tebl/RC6502-Apple-1-Replica/Abandoned/RC6502 Video Adapter/export/pcb.png

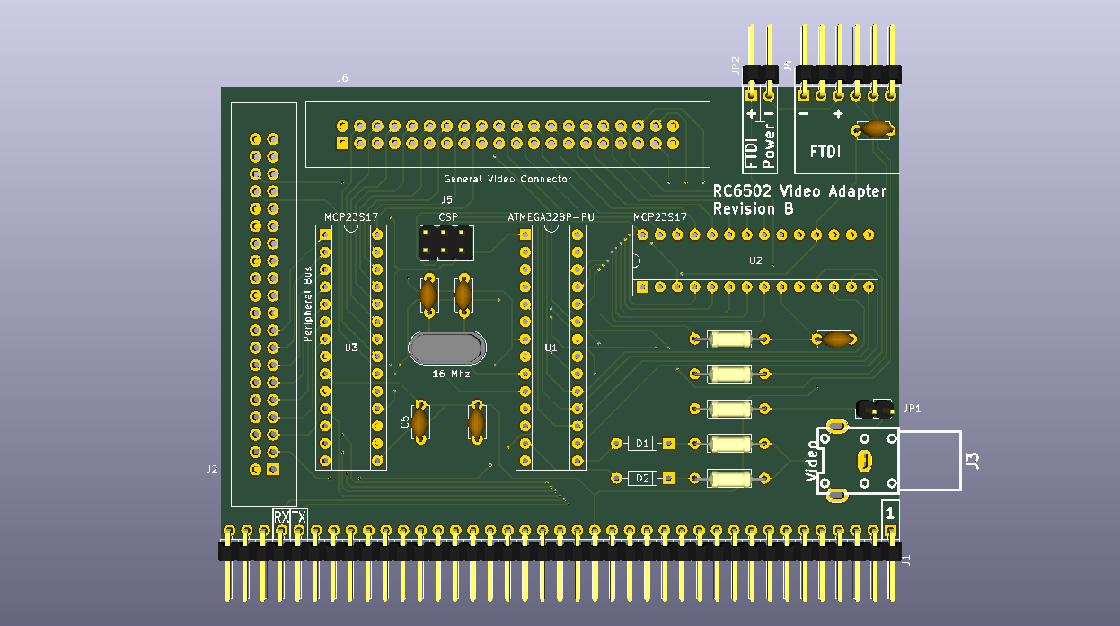
Abandoned/RC6502 Video Adapter/export/pcb.png
