tebl/RC6502-Apple-1-Replica/Gallery/2017-05-26 20.06.36.jpg

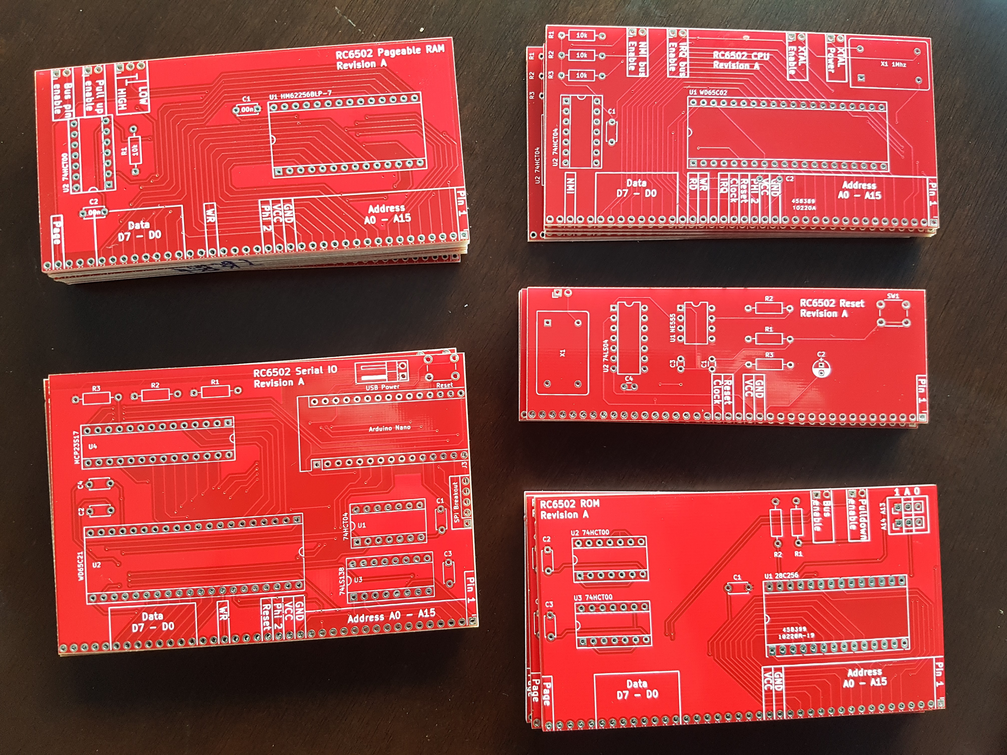
Gallery/2017-05-26 20.06.36.jpg
