tebl/RC6502-Apple-1-Replica/Gallery/2019-02-27 22.19.22.jpg

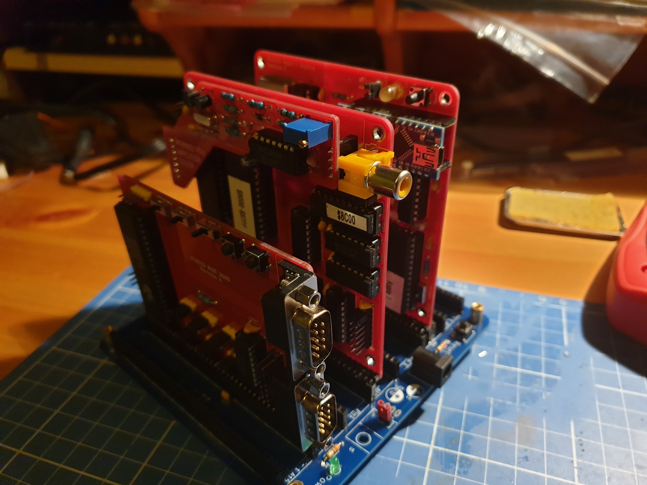
Gallery/2019-02-27 22.19.22.jpg
