tebl/RC6502-Apple-1-Replica/Gallery/apple_1_cover.jpg

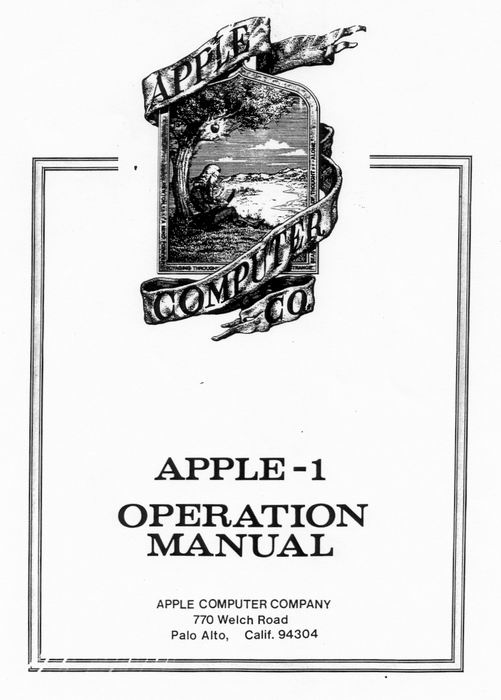
Gallery/apple_1_cover.jpg
