tebl/RC6502-Apple-1-Replica/RC6502 CPU/export/pcb.png

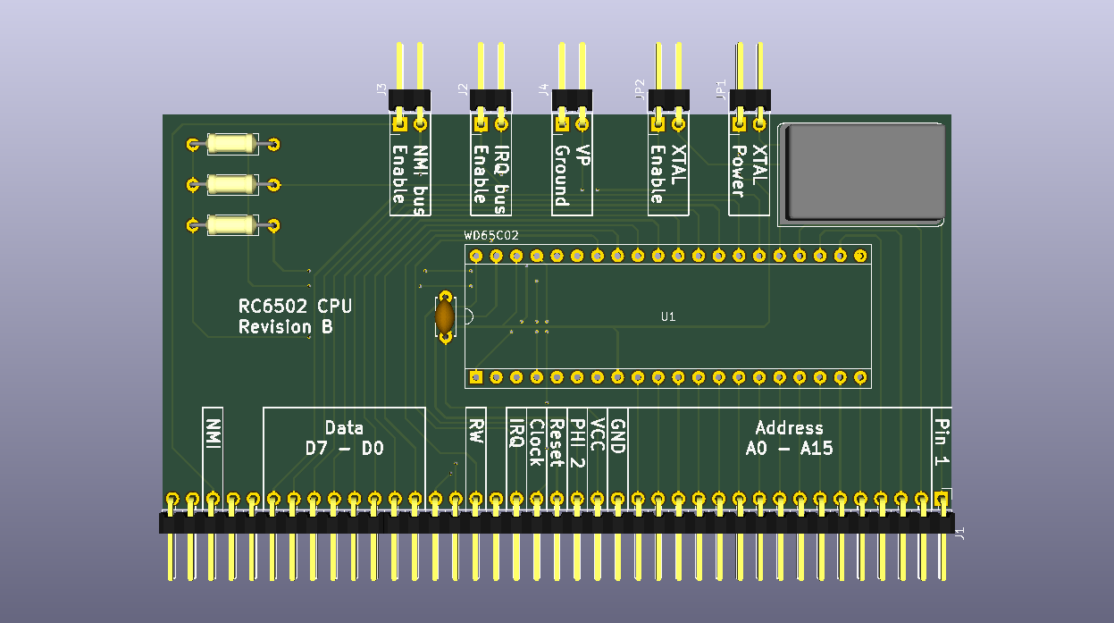
RC6502 CPU/export/pcb.png
