tebl/RC6502-Apple-1-Replica/RC6502 CPU/gallery/preview.PNG

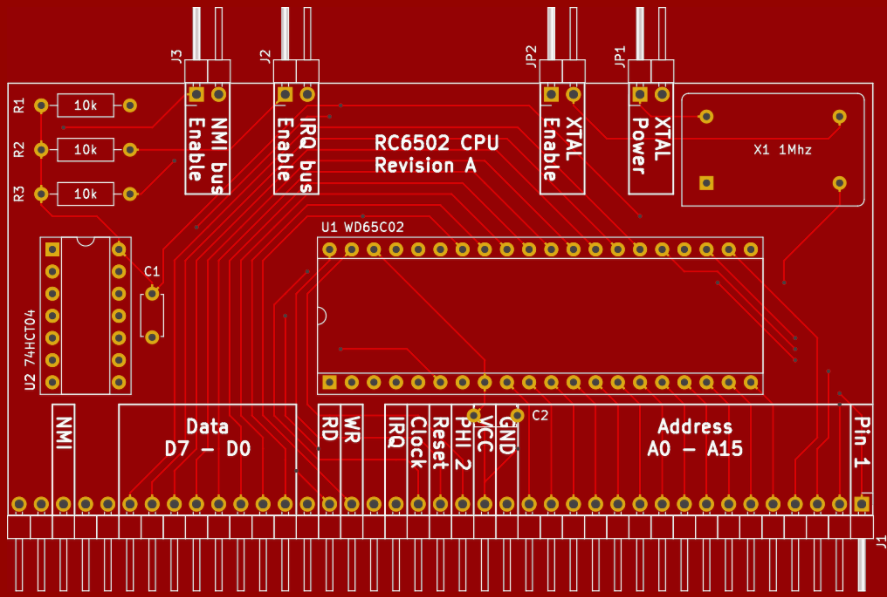
RC6502 CPU/gallery/preview.PNG
