tebl/RC6502-Apple-1-Replica/RC6502 RAM/gallery/RC6502 RAM Preview #1.png

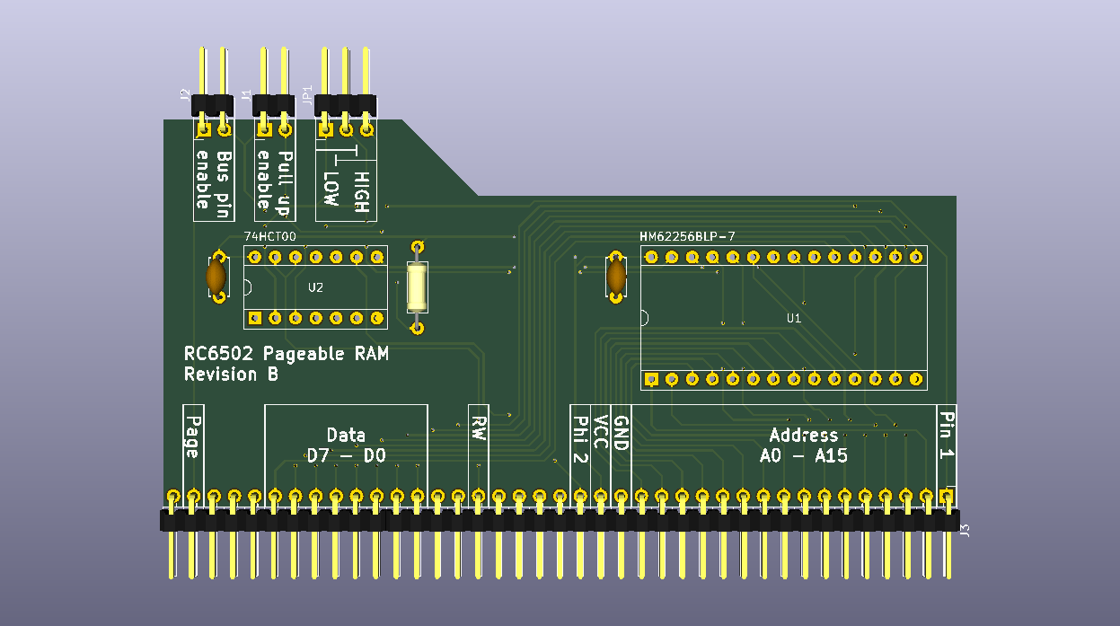
RC6502 RAM/gallery/RC6502 RAM Preview #1.png
