tebl/RC6502-Apple-1-Replica/RC6502 Reset Circuit/export/pcb.png

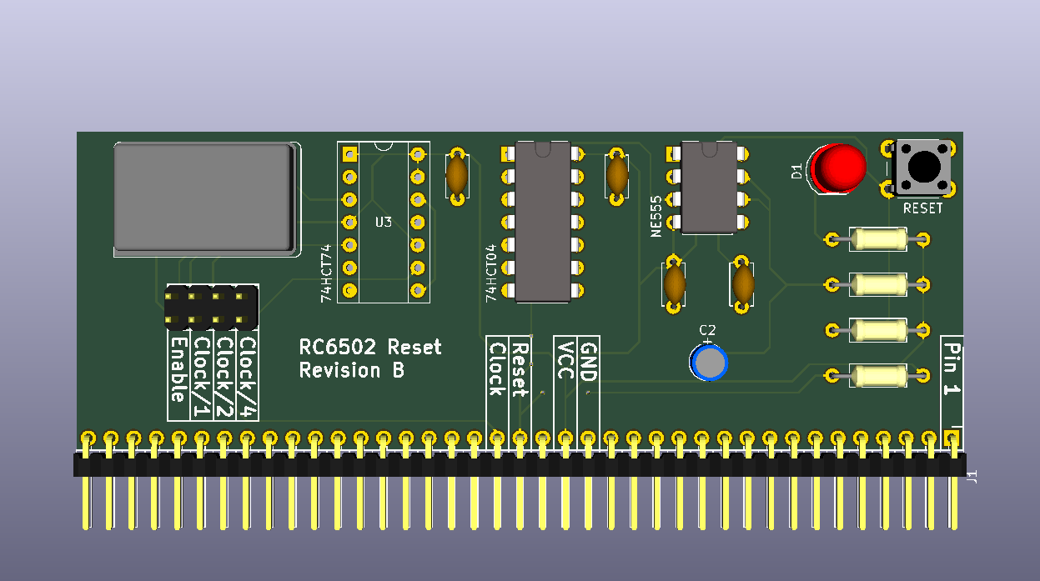
RC6502 Reset Circuit/export/pcb.png
