tebl/RC6502-Apple-1-Replica/RC6502 Reset Circuit/gallery/2017-06-02 19.52.55.jpg

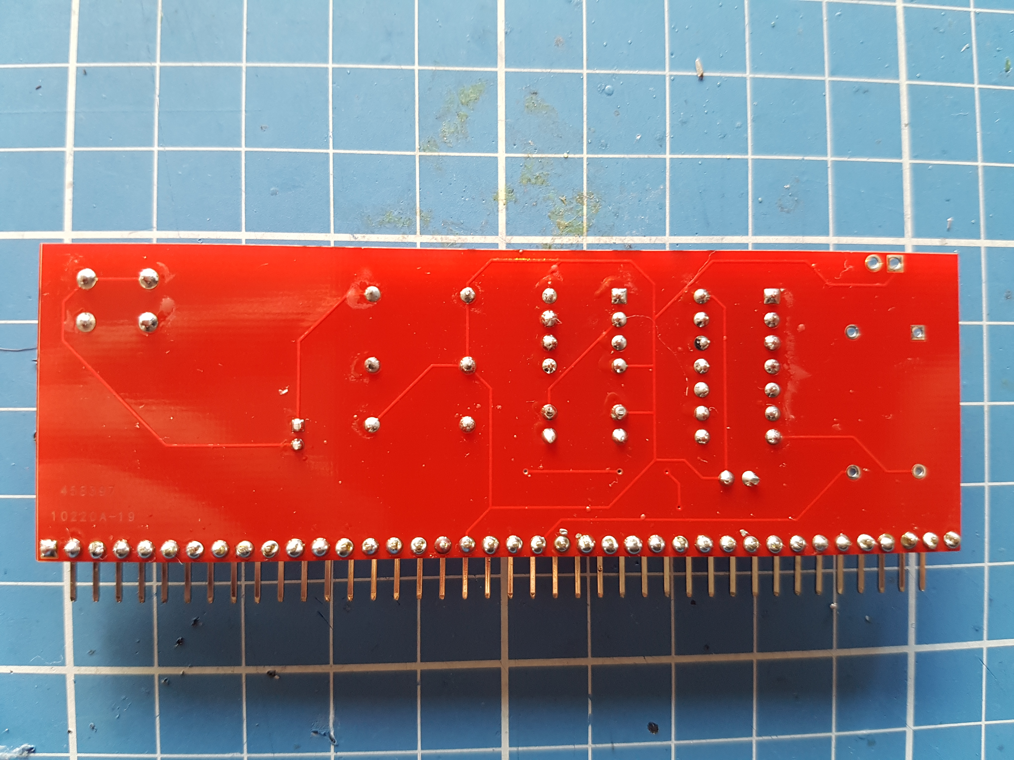
RC6502 Reset Circuit/gallery/2017-06-02 19.52.55.jpg
