tebl/RC6502-Apple-1-Replica/RC6502 RIOT/gallery/2019-02-21 22.14.20.jpg

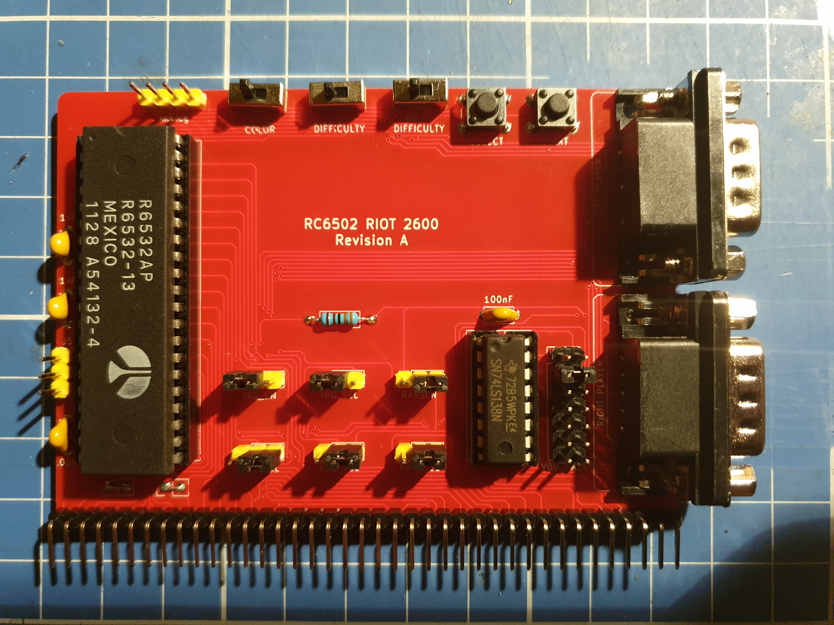
RC6502 RIOT/gallery/2019-02-21 22.14.20.jpg
