tebl/RC6502-Apple-1-Replica/RC6502 ROM/export/pcb.png

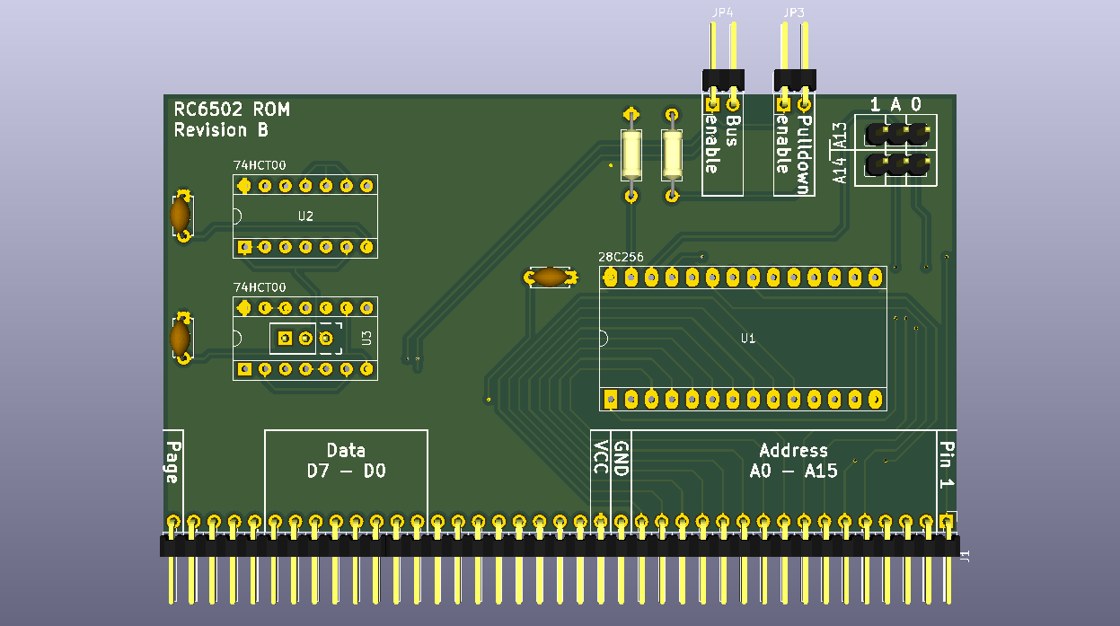
RC6502 ROM/export/pcb.png
