tebl/RC6502-Apple-1-Replica/RC6502 Serial IO/export/pcb.png

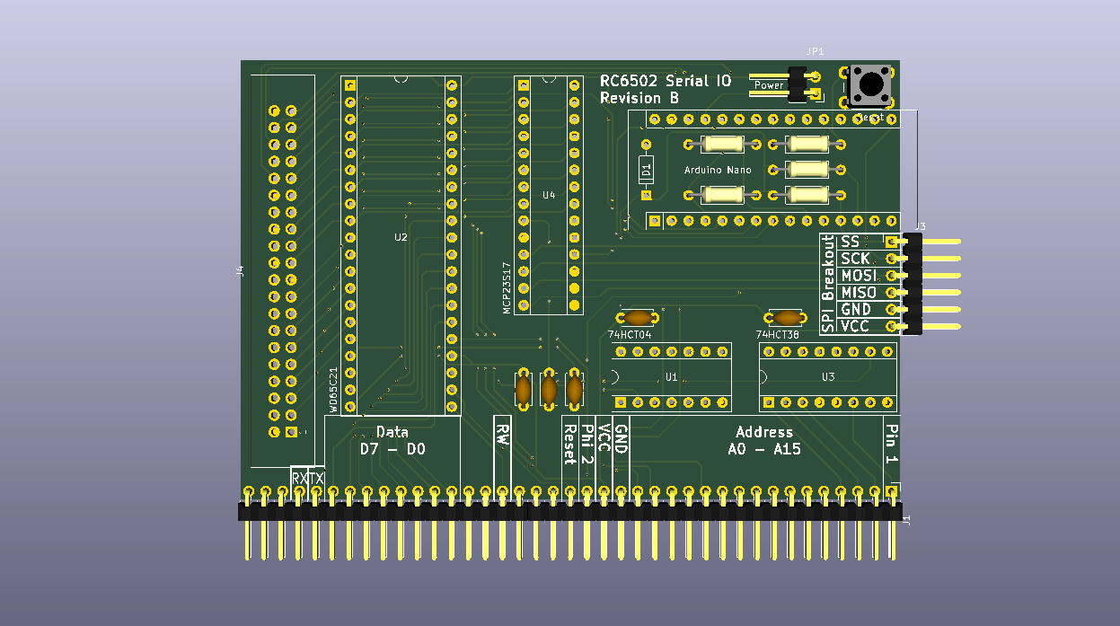
RC6502 Serial IO/export/pcb.png
