tebl/RC6502-Apple-1-Replica/RC6502 Terminal/gallery/2020-02-19 22.15.26.jpg

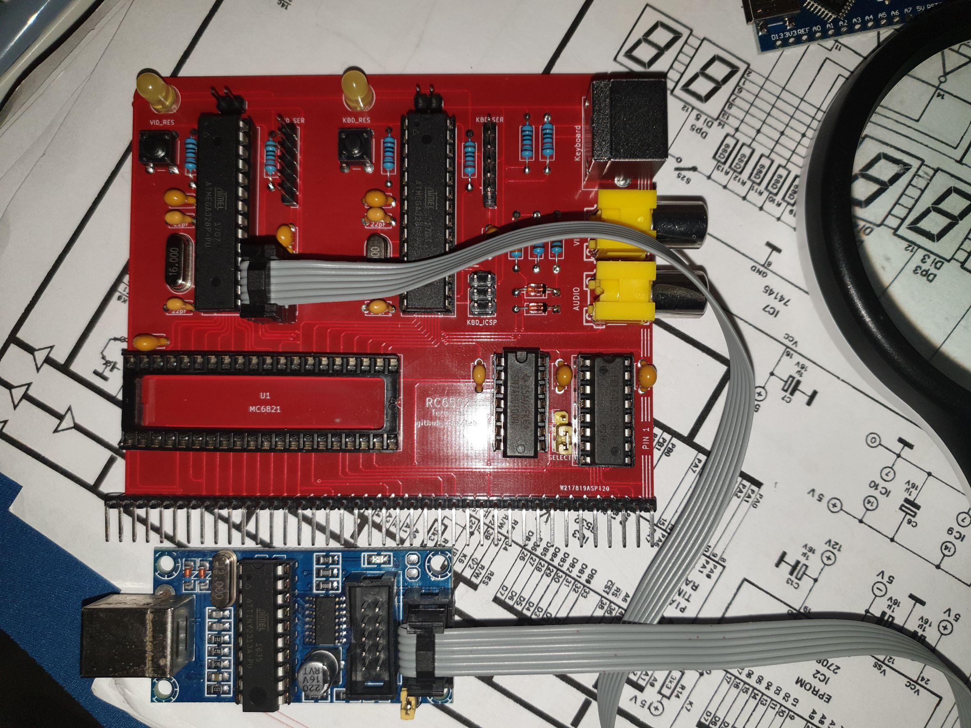
RC6502 Terminal/gallery/2020-02-19 22.15.26.jpg
