tebl/RC6502-Apple-1-Replica/RC6502 Terminal/gallery/2020-02-22 23.22.07.jpg

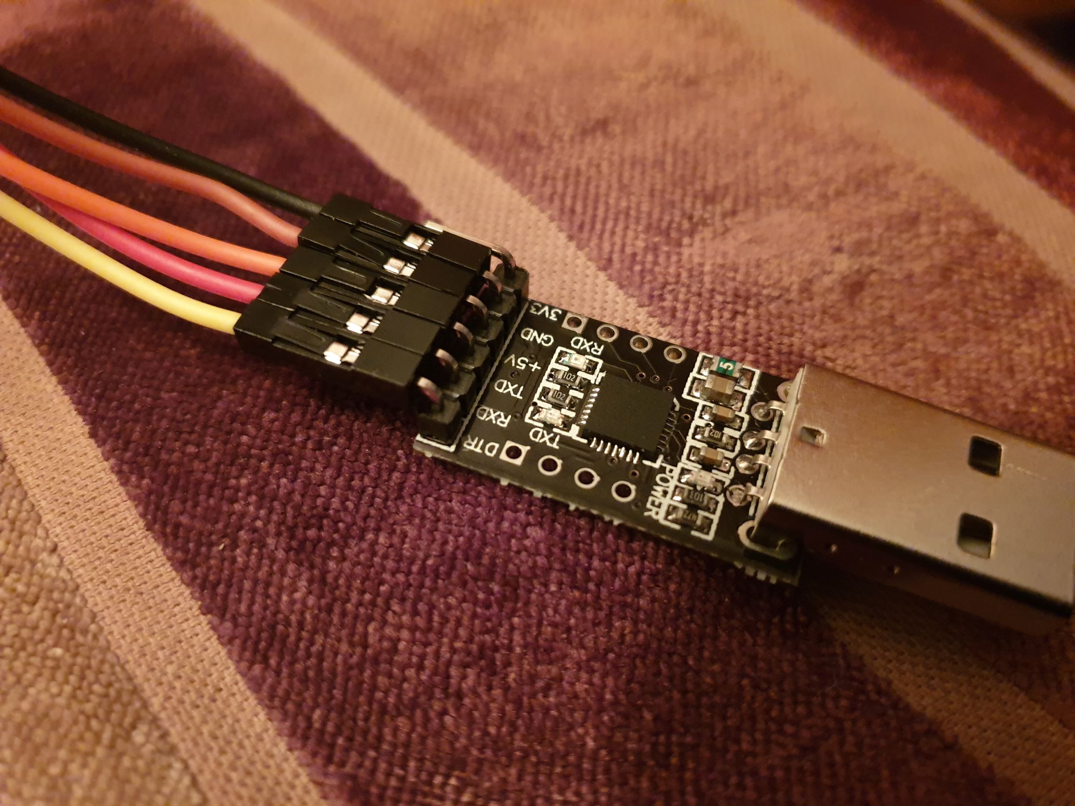
RC6502 Terminal/gallery/2020-02-22 23.22.07.jpg
