tebl/RC6502-Apple-1-Replica/RC6502 Terminal/gallery/2022-01-30 23.49.29.jpg

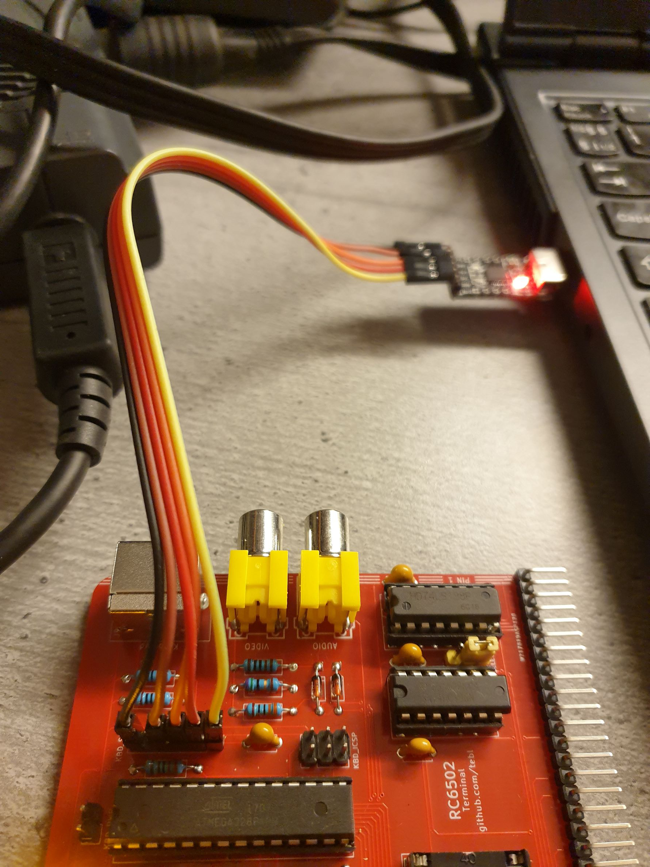
RC6502 Terminal/gallery/2022-01-30 23.49.29.jpg
