tebl/RC6502-Apple-1-Replica/RC6502 Terminal/gallery/Burn bootloader.png

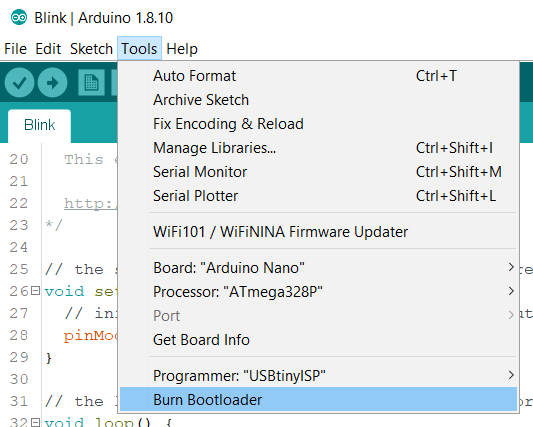
RC6502 Terminal/gallery/Burn bootloader.png
