tebl/RC6502-Apple-1-Replica/RC6502 Terminal/gallery/preview.png

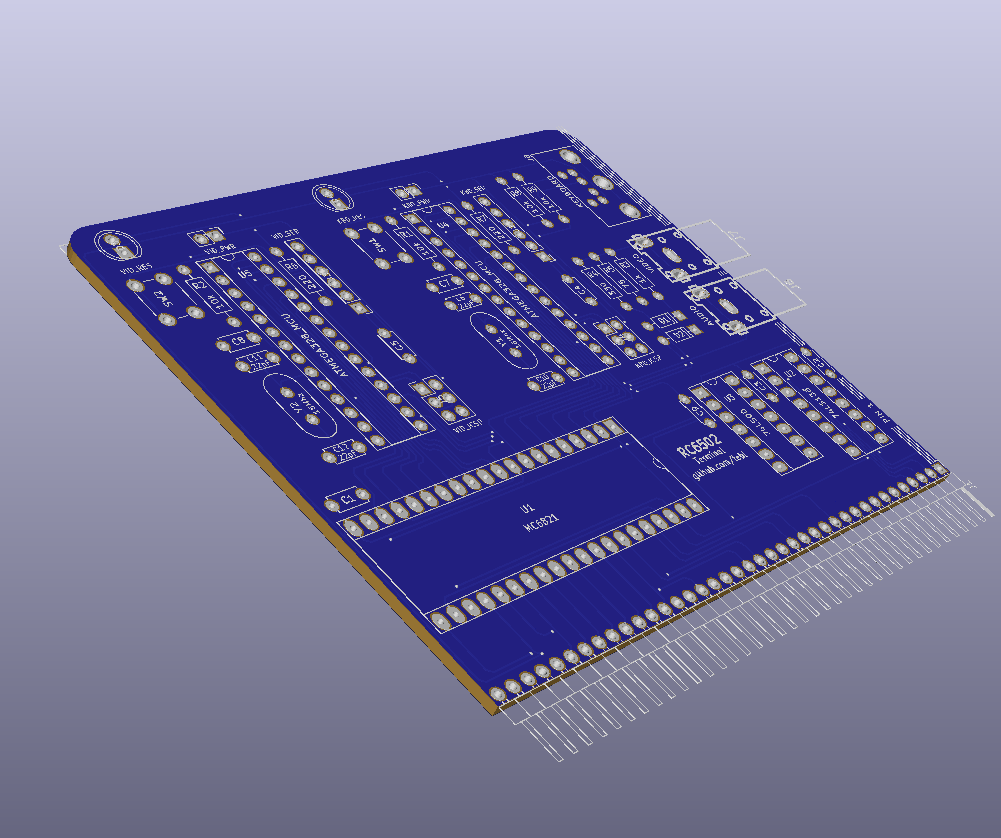
RC6502 Terminal/gallery/preview.png
