tebl/RC6502-Apple-1-Replica/RC6502 VDU Amplifier/gallery/2019-02-18 21.14.59.jpg

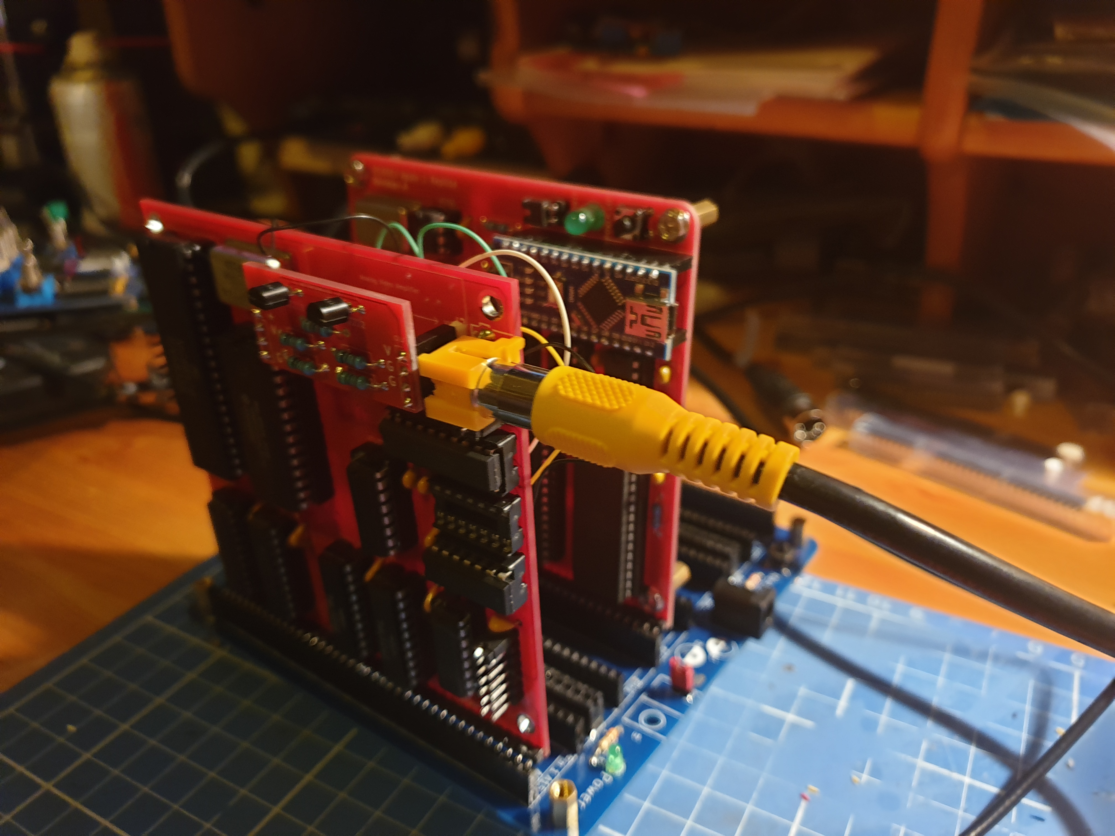
RC6502 VDU Amplifier/gallery/2019-02-18 21.14.59.jpg
