tebl/RC6502-Apple-1-Replica/RC6502 VDU Color Amplifier/gallery/2019-02-27 23.13.01-1.jpg

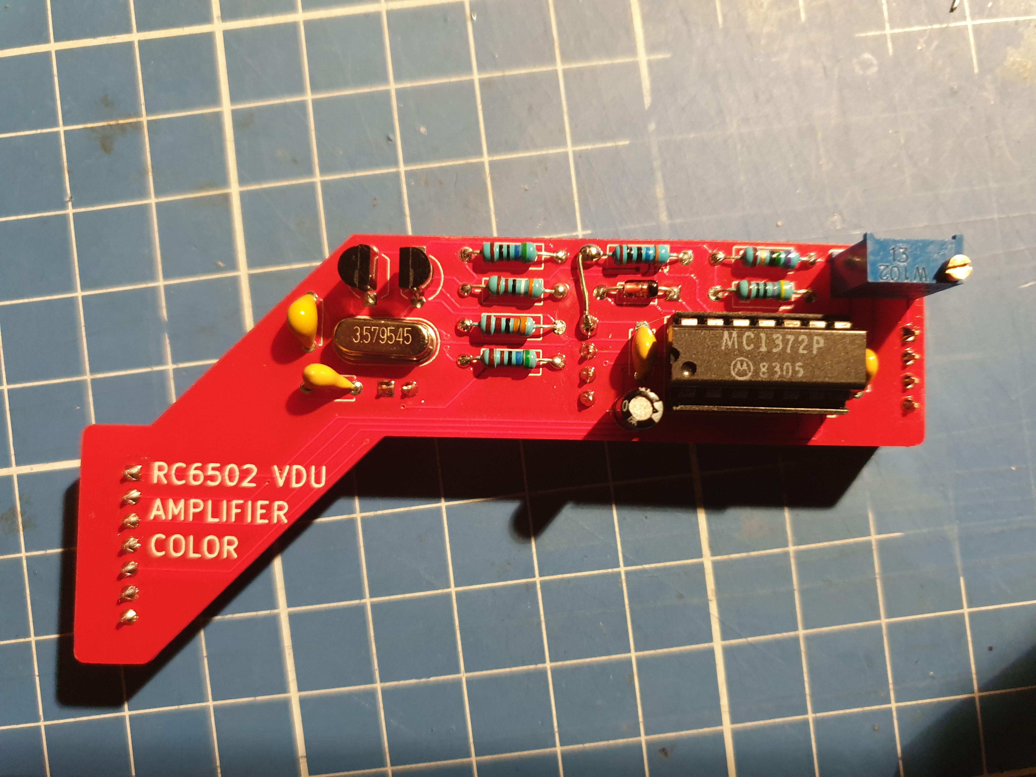
RC6502 VDU Color Amplifier/gallery/2019-02-27 23.13.01-1.jpg
