tebl/RC6502-Apple-1-Replica/Abandoned/RC6502 Video Adapter/export/RC6502 Video Adapter.pdf

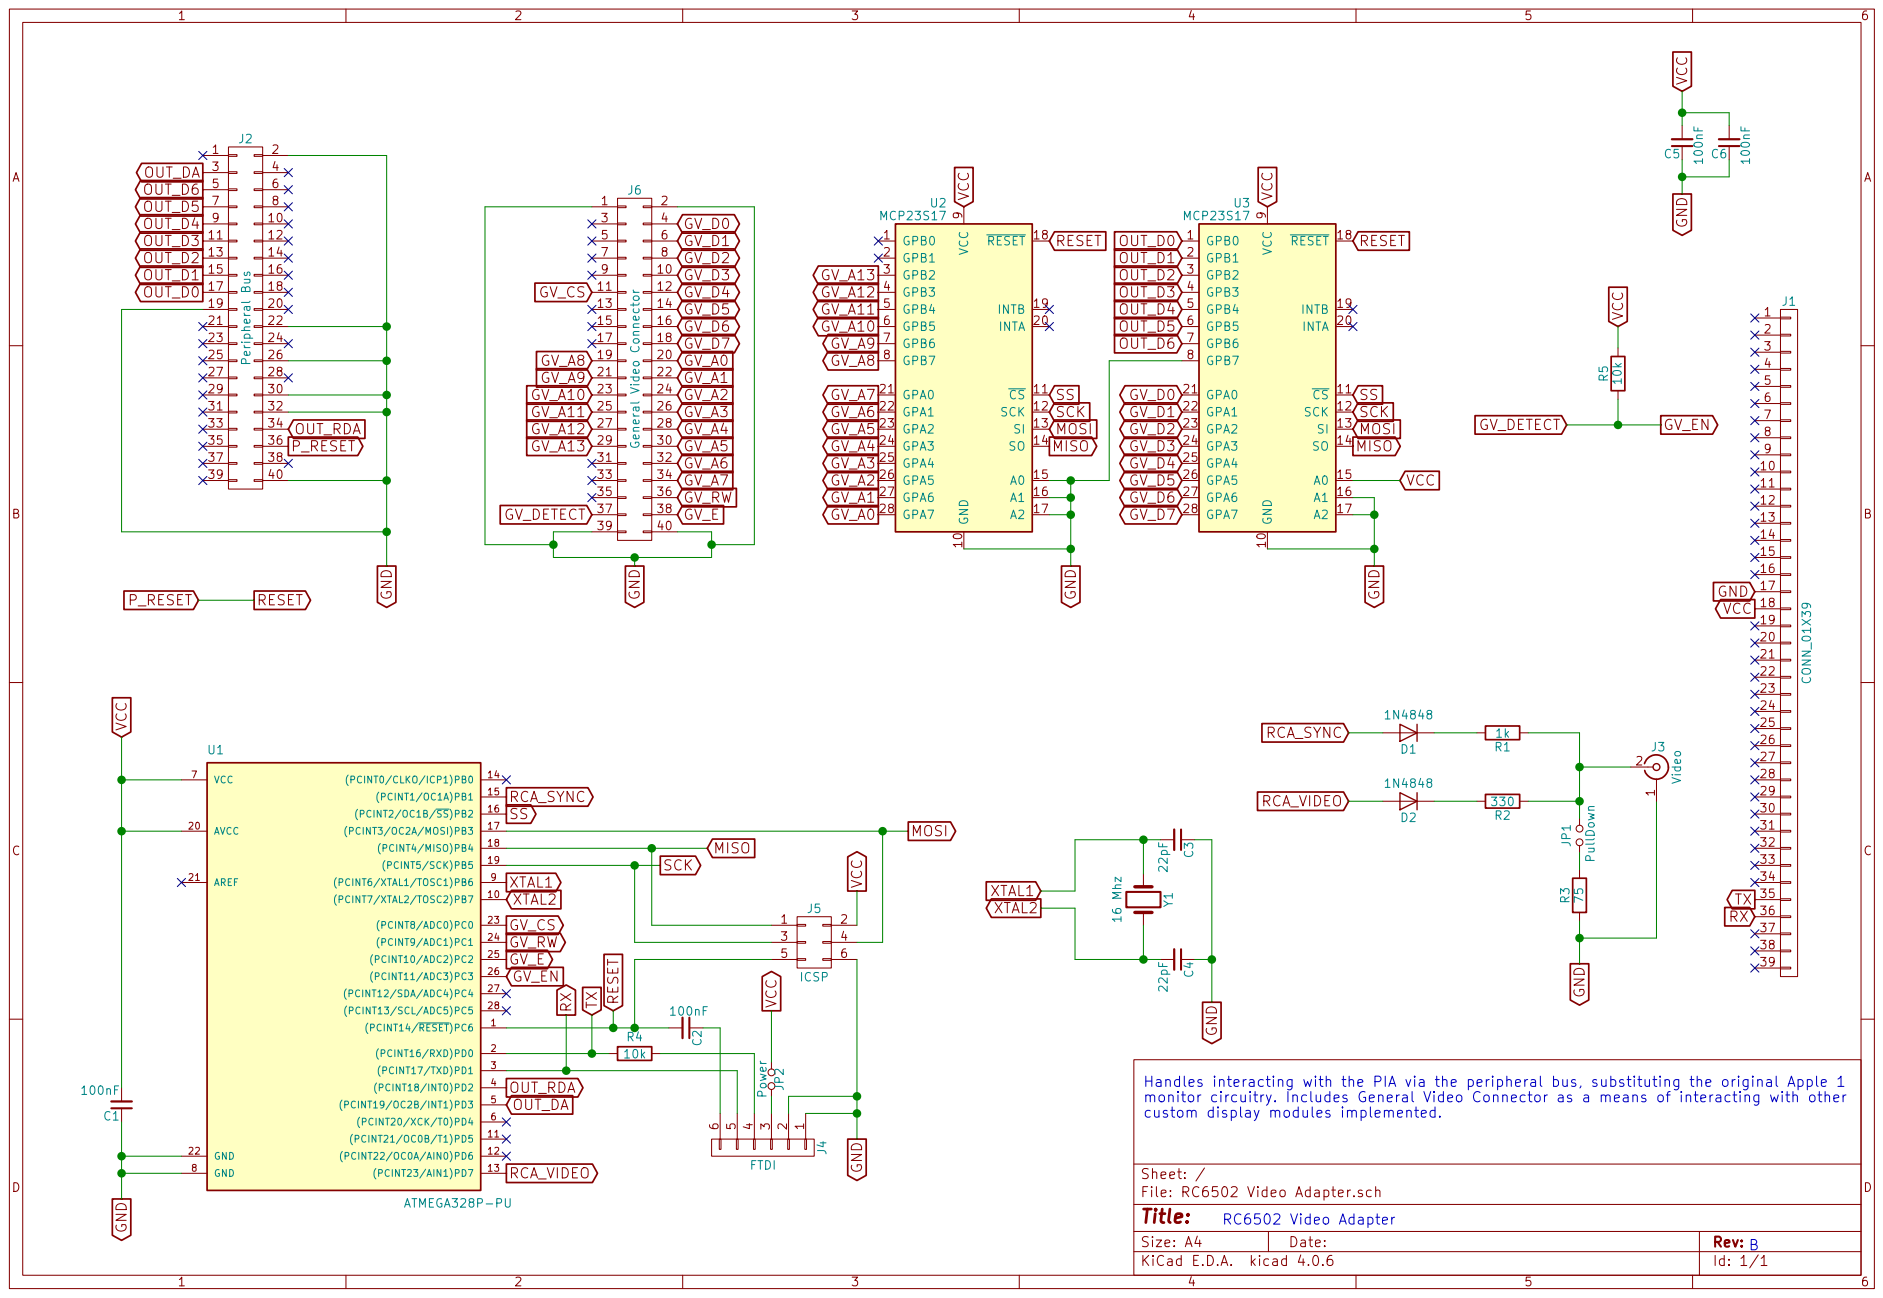
[picture p38: page 1]

Handles interacting with the PIA via the peripheral bus, substituting the original Apple 1
monitor circuitry. Includes General Video Connector as a means of interacting with other
custom display modules implemented.
