tebl/RC6502-Apple-1-Replica/RC6502 Prototyping/export/RC6502 Prototyping.pdf

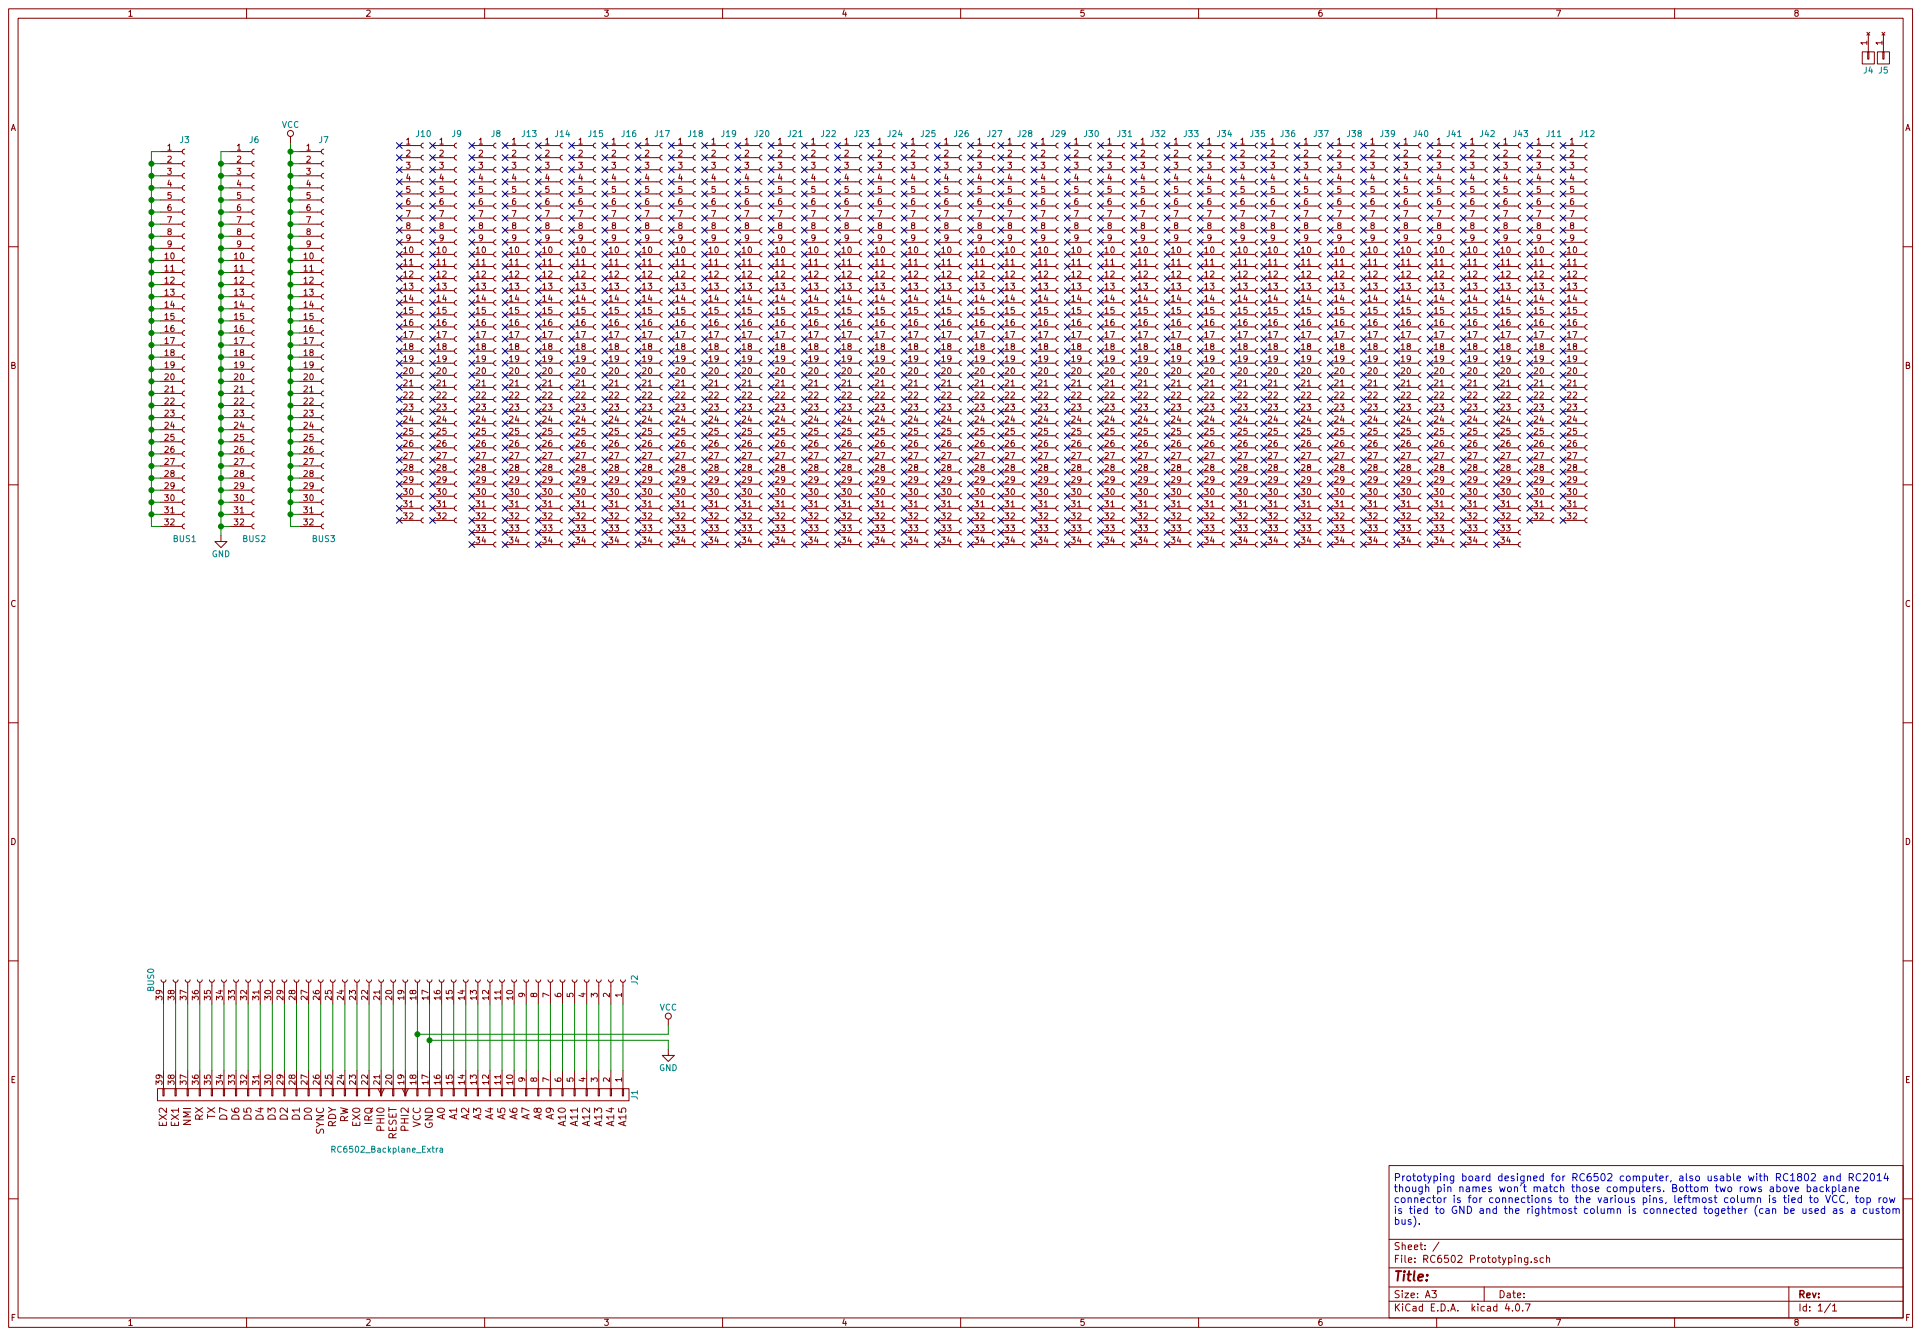
[picture p50: page 1]
