tebl/RC6502-Apple-1-Replica/RC6502 VDU Amplifier/export/RC6502 VDU Amplifier.pdf

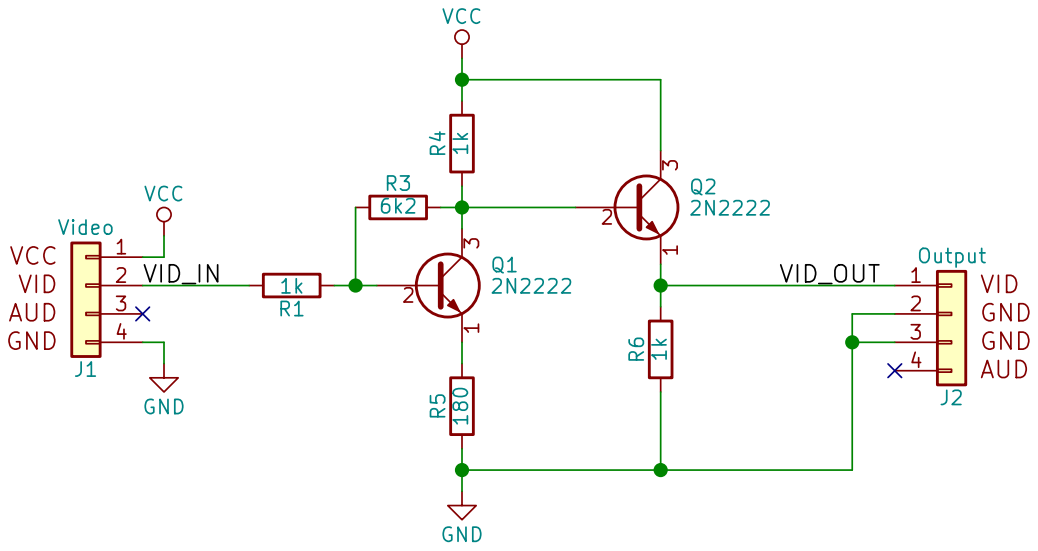
[picture p51: page 1]
