tebl/RC6502-Apple-1-Replica/RC6502 Reset Circuit/export/Reset circuit.pdf

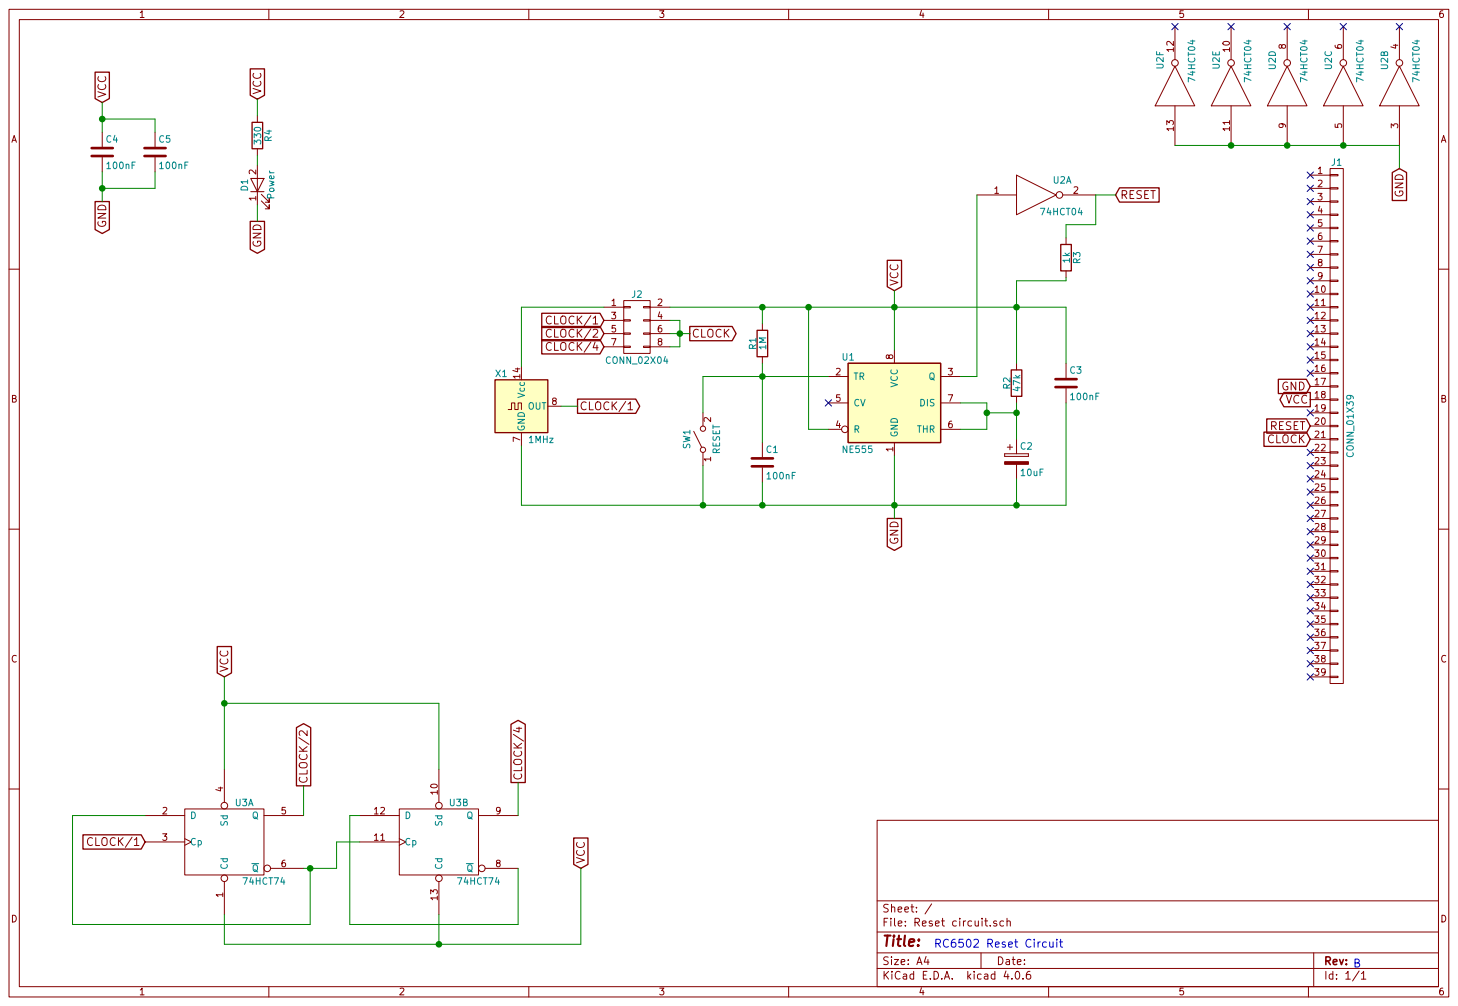
[picture p52: page 1]
