tebl/RC6502-Apple-1-Replica/RC6502 CPU/export/RC6502 CPU.pdf

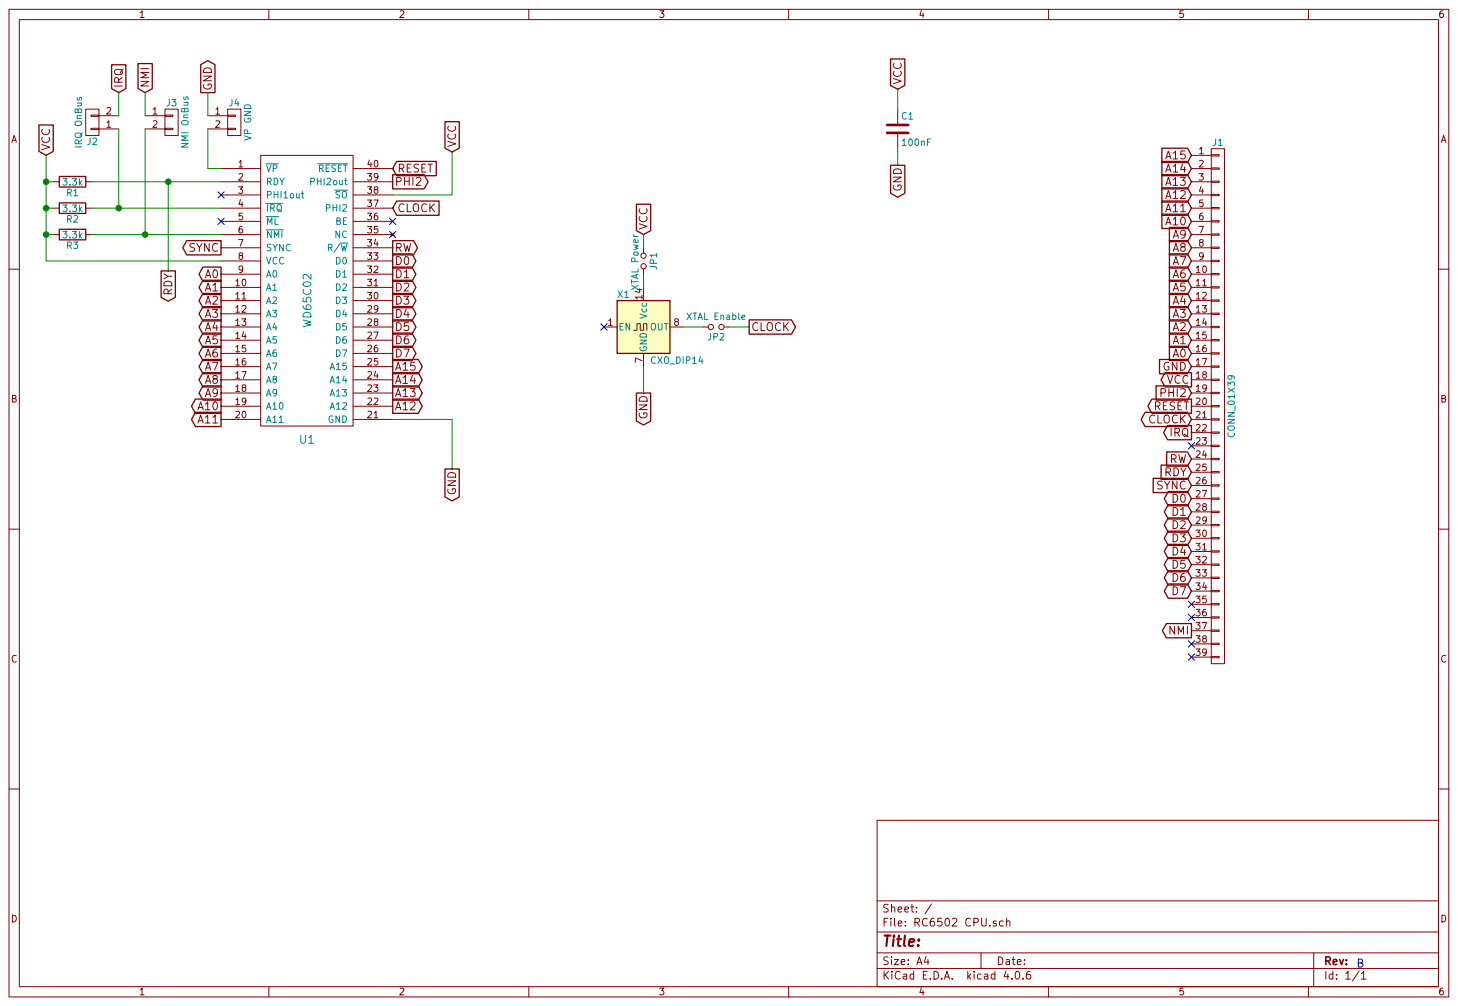
[picture p53: page 1]
