tebl/RC6502-Apple-1-Replica/RC6502 Serial IO/export/RC6502 Serial IO.pdf

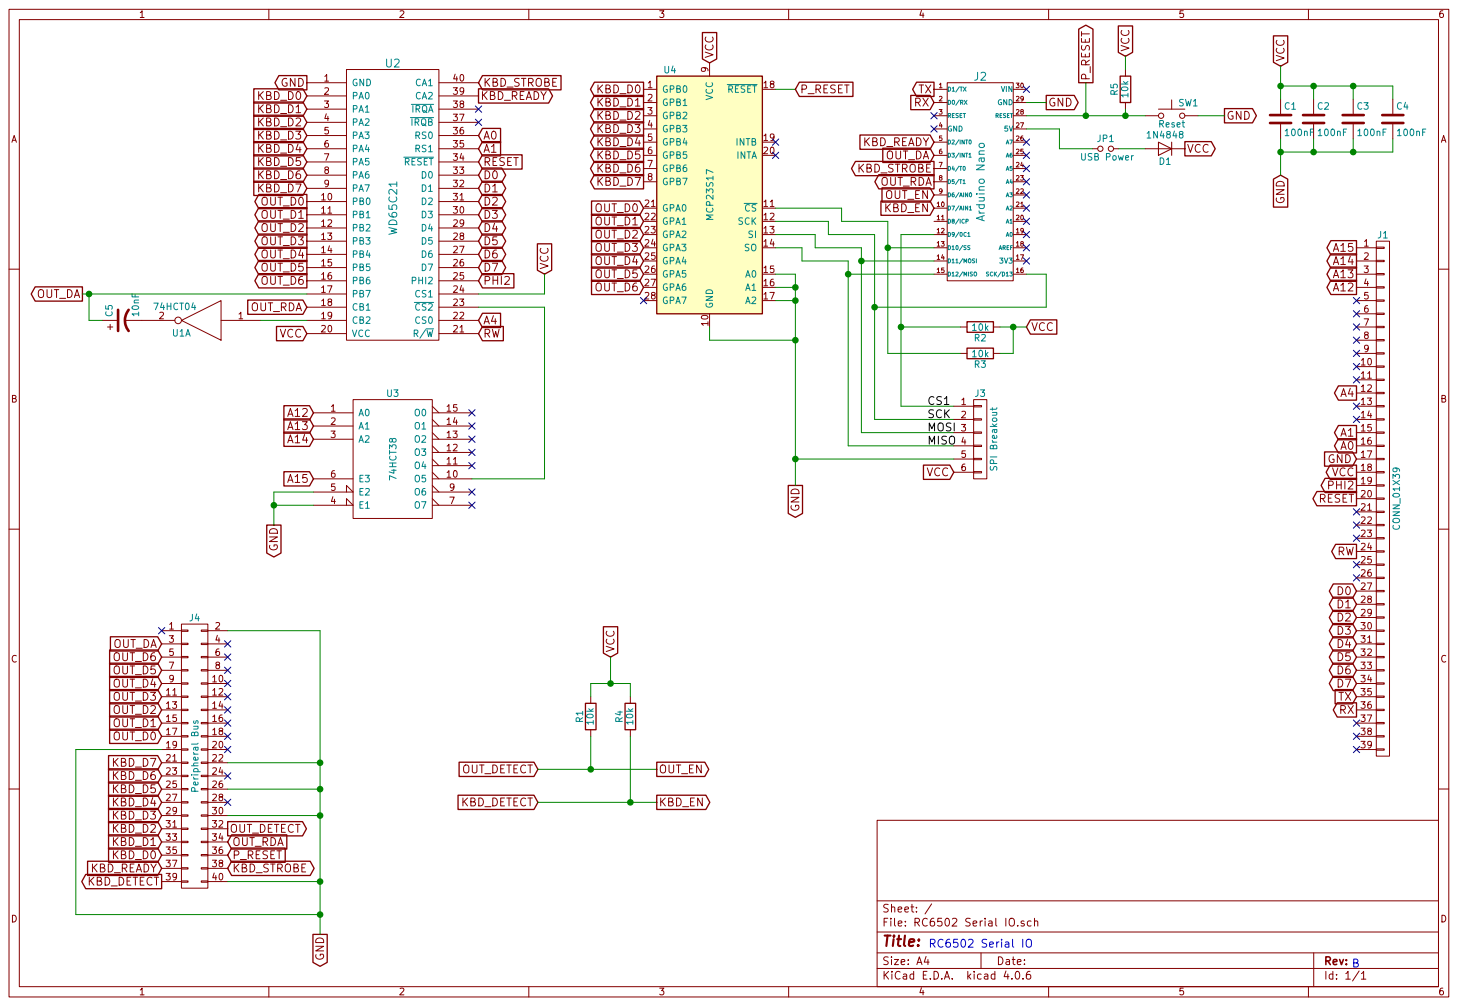
[picture p54: page 1]
