tebl/RC6502-Apple-1-Replica/RC6502 ROM/export/RC6502 ROM.pdf

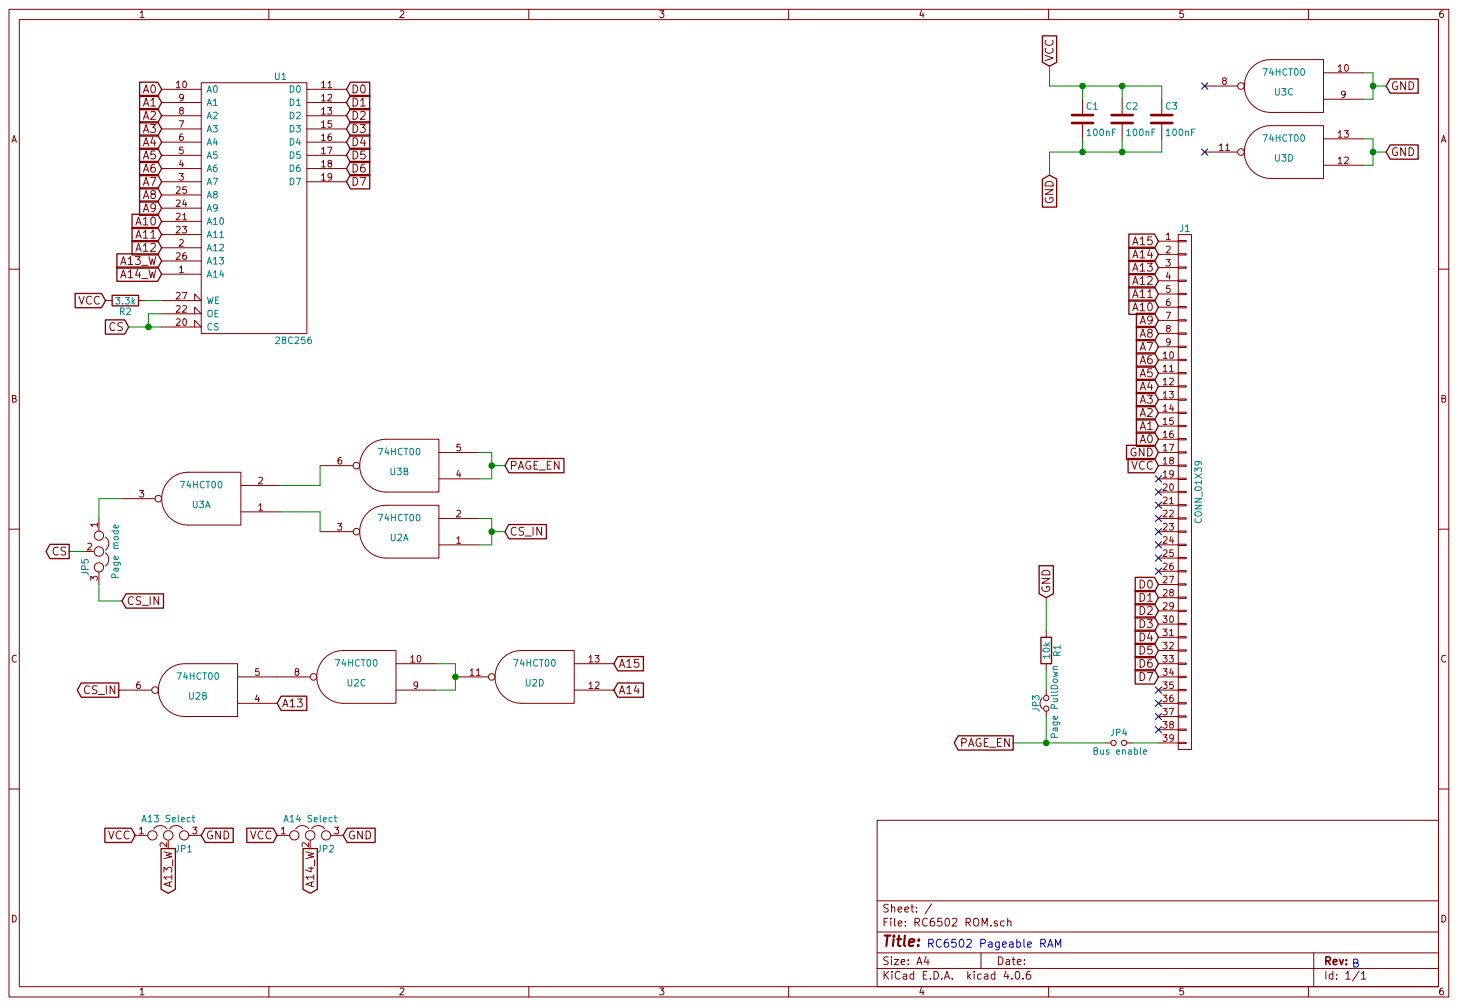
[picture p55: page 1]
