tebl/RC6502-Apple-1-Replica/RC6502 Apple 1 SBC/RC6502 Apple 1 SBC.kicad_pcb

## KiCad design RC6502 Apple 1 SBC/RC6502 Apple 1 SBC.kicad_pcb (2020-01-25)

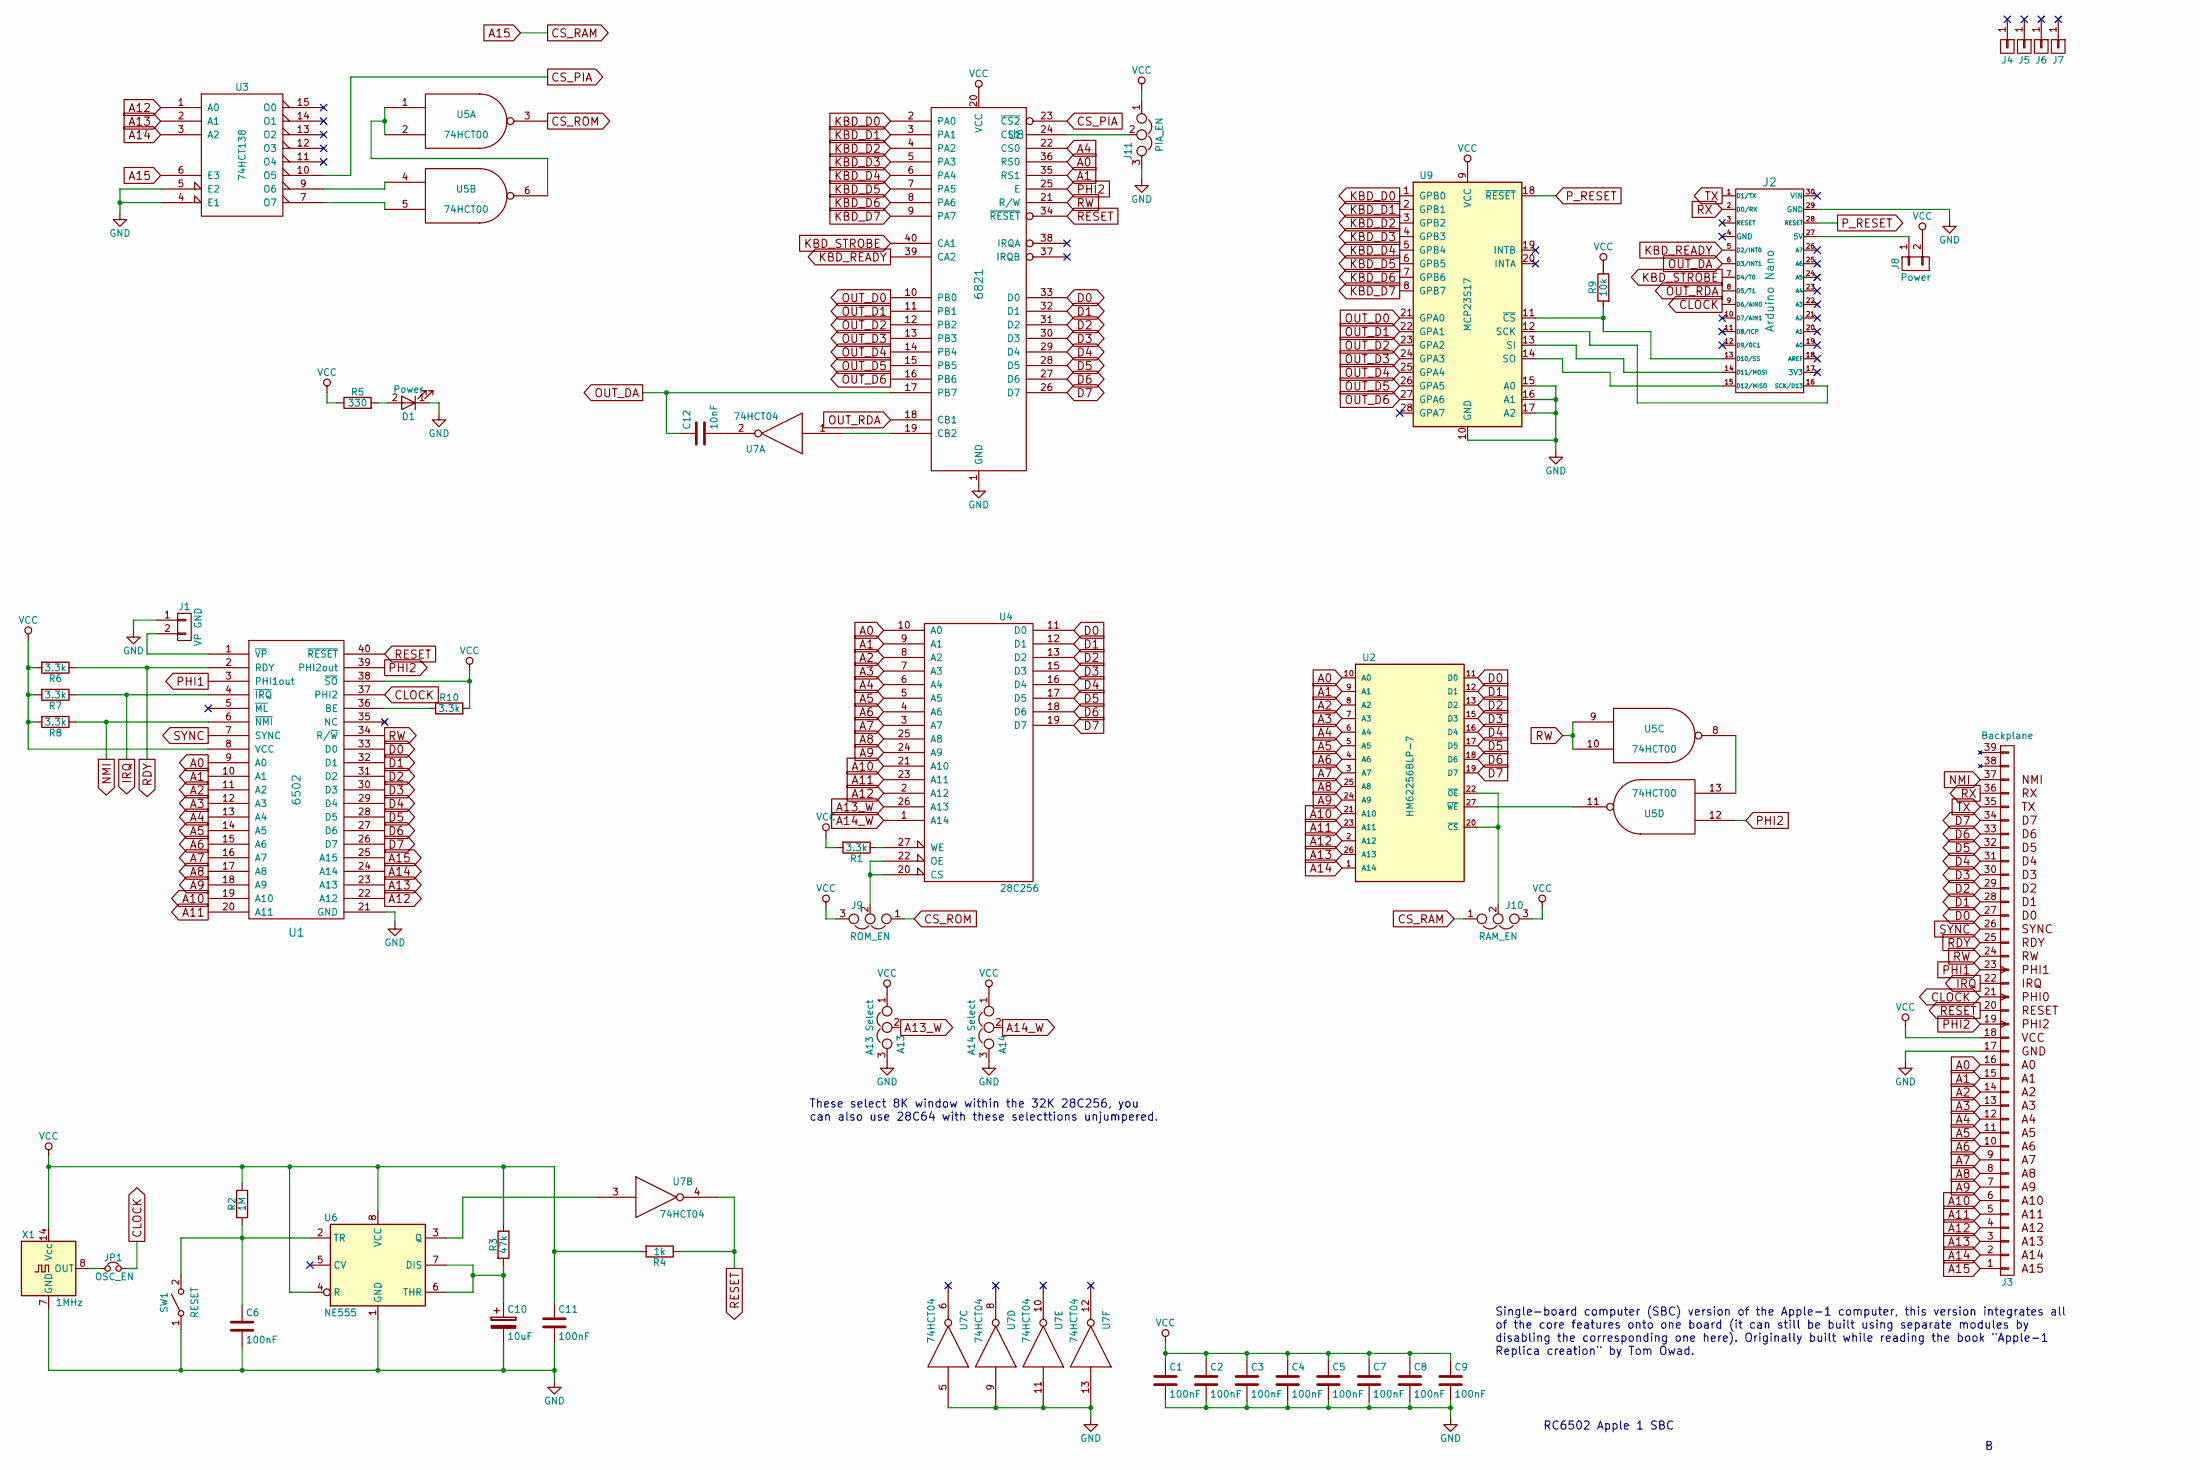
[picture p56: schematic RC6502 Apple 1 SBC.sch]

Parts:
A13: A13 Select; Pin_Header_Straight_1x03_Pitch2.54mm
A14: A14 Select; Pin_Header_Straight_1x03_Pitch2.54mm
C1, C2, C3, C4, C5, C6, C7, C8, C9, C11: 100nF; C_Disc_D4.7mm_W2.5mm_P5.00mm
C10: 10uF; CP_Radial_D4.0mm_P2.00mm
C12: 10nF; C_Disc_D4.7mm_W2.5mm_P5.00mm
D1: Power; LED_D5.0mm
J1: VP GND; Pin_Header_Straight_1x02_Pitch2.54mm
J2: Arduino Nano; Arduino_Nano
J3: Backplane; Pin_Header_Angled_1x39_Pitch2.54mm
J4, J5, J6, J7: Hole; Mounting
J8: Power; Pin_Header_Angled_1x02_Pitch2.54mm
J9: ROM_EN; Pin_Header_Straight_1x03_Pitch2.54mm
J10: RAM_EN; Pin_Header_Straight_1x03_Pitch2.54mm
J11: PIA_EN; Pin_Header_Straight_1x03_Pitch2.54mm
JP1: OSC_EN; Pin_Header_Straight_1x02_Pitch2.54mm
R1, R6, R7, R8, R10: 3.3k; R_Axial_DIN0207_L6.3mm_D2.5mm_P10.16mm_Horizontal
R2: 1M; R_Axial_DIN0207_L6.3mm_D2.5mm_P10.16mm_Horizontal
R3: 47k; R_Axial_DIN0207_L6.3mm_D2.5mm_P10.16mm_Horizontal
R4: 1k; R_Axial_DIN0207_L6.3mm_D2.5mm_P10.16mm_Horizontal
R5: 330; R_Axial_DIN0207_L6.3mm_D2.5mm_P10.16mm_Horizontal
R9: 10k; R_Axial_DIN0207_L6.3mm_D2.5mm_P10.16mm_Horizontal
SW1: RESET; SW_PUSH_6mm
U1: 6502; DIP-40_W15.24mm_Socket
U2: HM62256BLP-7; DIP-28_W15.24mm_Socket
U3: 74HCT138; DIP-16_W7.62mm_Socket
U4: 28C256; DIP-28_W15.24mm_Socket
U5: 74HCT00; DIP-14_W7.62mm_Socket
U6: NE555; DIP-8_W7.62mm
U7: 74HCT04; DIP-14_W7.62mm
U8: 6821; DIP-40_W15.24mm_Socket
U9: MCP23S17; DIP-28_W7.62mm_Socket
X1: 1MHz; Oscillator_DIP-14

Connections:
A0: J3.16 (A0), U1.9 (A0), U2.10 (A0), U4.10 (A0), U8.36 (RS0)
A1: J3.15 (A1), U1.10 (A1), U2.9 (A1), U4.9 (A1), U8.35 (RS1)
A2: J3.14 (A2), U1.11 (A2), U2.8 (A2), U4.8 (A2)
A3: J3.13 (A3), U1.12 (A3), U2.7 (A3), U4.7 (A3)
A4: J3.12 (A4), U1.13 (A4), U2.6 (A4), U4.6 (A4), U8.22 (CS0)
A5: J3.11 (A5), U1.14 (A5), U2.5 (A5), U4.5 (A5)
A6: J3.10 (A6), U1.15 (A6), U2.4 (A6), U4.4 (A6)
A7: J3.9 (A7), U1.16 (A7), U2.3 (A7), U4.3 (A7)
A8: J3.8 (A8), U1.17 (A8), U2.25 (A8), U4.25 (A8)
A9: J3.7 (A9), U1.18 (A9), U2.24 (A9), U4.24 (A9)
A10: J3.6 (A10), U1.19 (A10), U2.21 (A10), U4.21 (A10)
A11: J3.5 (A11), U1.20 (A11), U2.23 (A11), U4.23 (A11)
A12: J3.4 (A12), U1.22 (A12), U2.2 (A12), U3.1 (A0), U4.2 (A12)
A13: J3.3 (A13), U1.23 (A13), U2.26 (A13), U3.2 (A1)
A13_W: A13.2, U4.26 (A13)
A14: J3.2 (A14), U1.24 (A14), U2.1 (A14), U3.3 (A2)
A14_W: A14.2, U4.1 (A14)
A15: J3.1 (A15), J10.1, U1.25 (A15), U3.6 (E3)
CLOCK: J2.9 (D6/AIN0), J3.21 (PHI0), JP1.2, U1.37 (PHI2)
CS_PIA: U3.10 (O5), U8.23 (~CS2)
CS_ROM: J9.1, U5.3
D0: J3.27 (D0), U1.33 (D0), U2.11 (D0), U4.11 (D0), U8.33 (D0)
D1: J3.28 (D1), U1.32 (D1), U2.12 (D1), U4.12 (D1), U8.32 (D1)
D2: J3.29 (D2), U1.31 (D2), U2.13 (D2), U4.13 (D2), U8.31 (D2)
D3: J3.30 (D3), U1.30 (D3), U2.15 (D3), U4.15 (D3), U8.30 (D3)
D4: J3.31 (D4), U1.29 (D4), U2.16 (D4), U4.16 (D4), U8.29 (D4)
D5: J3.32 (D5), U1.28 (D5), U2.17 (D5), U4.17 (D5), U8.28 (D5)
D6: J3.33 (D6), U1.27 (D6), U2.18 (D6), U4.18 (D6), U8.27 (D6)
D7: J3.34 (D7), U1.26 (D7), U2.19 (D7), U4.19 (D7), U8.26 (D7)
GND: A13.3, A14.3, C1.2, C2.2, C3.2, C4.2, C5.2, C6.2, C7.2, C8.2, C9.2, C10.2, C11.2, D1.1 (K), J1.1, J2.29 (GND), J3.17, J11.3, SW1.1 (A), U1.21 (GND), U2.14 (GND), U3.4 (E1), U3.5 (E2), U3.8 (GND), U4.14 (GND), U5.7 (GND), U6.1 (GND), U7.5, U7.7 (GND), U7.9, U7.11, U7.13, U8.1 (GND), U9.10 (GND), U9.15 (A0), U9.16 (A1), U9.17 (A2), X1.7 (GND)
IRQ: J3.22 (IRQ), R7.1, U1.4 (~IRQ)
KBD_D0: U8.2 (PA0), U9.1 (GPB0)
KBD_D1: U8.3 (PA1), U9.2 (GPB1)
KBD_D2: U8.4 (PA2), U9.3 (GPB2)
KBD_D3: U8.5 (PA3), U9.4 (GPB3)
KBD_D4: U8.6 (PA4), U9.5 (GPB4)
KBD_D5: U8.7 (PA5), U9.6 (GPB5)
KBD_D6: U8.8 (PA6), U9.7 (GPB6)
KBD_D7: U8.9 (PA7), U9.8 (GPB7)
KBD_READY: J2.5 (D2/INT0), U8.39 (CA2)
KBD_STROBE: J2.7 (D4/T0), U8.40 (CA1)
NMI: J3.37 (NMI), R8.1, U1.6 (~NMI)
unnamed: C6.1, R2.2, SW1.2 (B), U6.2 (TR)
unnamed: C10.1, R3.2, U6.6 (THR), U6.7 (DIS)
unnamed: C12.2, U7.2
unnamed: D1.2 (A), R5.2
unnamed: J1.2, U1.1 (~VP)
unnamed: J2.13 (D10/SS), R9.2, U9.11 (~CS)
unnamed: J2.14 (D11/MOSI), U9.13 (SI)
unnamed: J2.15 (D12/MISO), U9.14 (SO)
unnamed: J2.16 (SCK/D13), U9.12 (SCK)
unnamed: J2.27 (5V), J8.1
unnamed: J9.2, U4.20 (CS), U4.22 (OE)
unnamed: J10.2, U2.20 (~CS), U2.22 (~OE)
unnamed: J11.2, U8.24 (CS1)
unnamed: JP1.1, X1.8 (OUT)
unnamed: R1.1, U4.27 (WE)
unnamed: R10.1, U1.36 (BE)
unnamed: U2.27 (~WE), U5.11
unnamed: U3.7 (O7), U5.5
unnamed: U3.9 (O6), U5.4
unnamed: U5.1, U5.2, U5.6
unnamed: U5.8, U5.13
unnamed: U6.3 (Q), U7.3
unnamed: U7.1, U8.19 (CB2)
OUT_D0: U8.10 (PB0), U9.21 (GPA0)
OUT_D1: U8.11 (PB1), U9.22 (GPA1)
OUT_D2: U8.12 (PB2), U9.23 (GPA2)
OUT_D3: U8.13 (PB3), U9.24 (GPA3)
OUT_D4: U8.14 (PB4), U9.25 (GPA4)
OUT_D5: U8.15 (PB5), U9.26 (GPA5)
OUT_D6: U8.16 (PB6), U9.27 (GPA6)
OUT_DA: C12.1, J2.6 (D3/INT1), U8.17 (PB7)
OUT_RDA: J2.8 (D5/T1), U8.18 (CB1)
PHI1: J3.23 (PHI1), U1.3 (PHI1out)
PHI2: J3.19 (PHI2), U1.39 (PHI2out), U5.12, U8.25 (E)
P_RESET: J2.28 (RESET), U9.18 (~RESET)
RDY: J3.25 (READY), R6.1, U1.2 (RDY)
RESET: J3.20 (RESET), R4.1, U1.40 (~RESET), U7.4, U8.34 (~RESET)
RW: J3.24 (RW), U1.34 (R/~W), U5.9, U5.10, U8.21 (R/W)
RX: J2.2 (D0/RX), J3.36 (RX)
SYNC: J3.26 (SYNC), U1.7 (SYNC)
TX: J2.1 (D1/TX), J3.35 (TX)
VCC: A13.1, A14.1, C1.1, C2.1, C3.1, C4.1, C5.1, C7.1, C8.1, C9.1, C11.1, J3.18, J8.2, J9.3, J10.3, J11.1, R1.2, R2.1, R3.1, R4.2, R5.1, R6.2, R7.2, R8.2, R9.1, R10.2, U1.8 (VCC), U1.38 (~SO), U2.28 (VCC), U3.16 (VCC), U4.28 (VCC), U5.14 (VCC), U6.4 (R), U6.8 (VCC), U7.14 (VCC), U8.20 (VCC), U9.9 (VCC), X1.14 (Vcc)

Notes on the sheet:
RC6502 Apple 1 SBC
Single-board computer (SBC) version of the Apple-1 computer, this version integrates all of the core features onto one board (it can still be built using separate modules by disabling the corresponding one here). Originally built while reading the book "Apple-1 Replica creation" by Tom Owad.
These select 8K window within the 32K 28C256, you can also use 28C64 with these selecttions unjumpered.

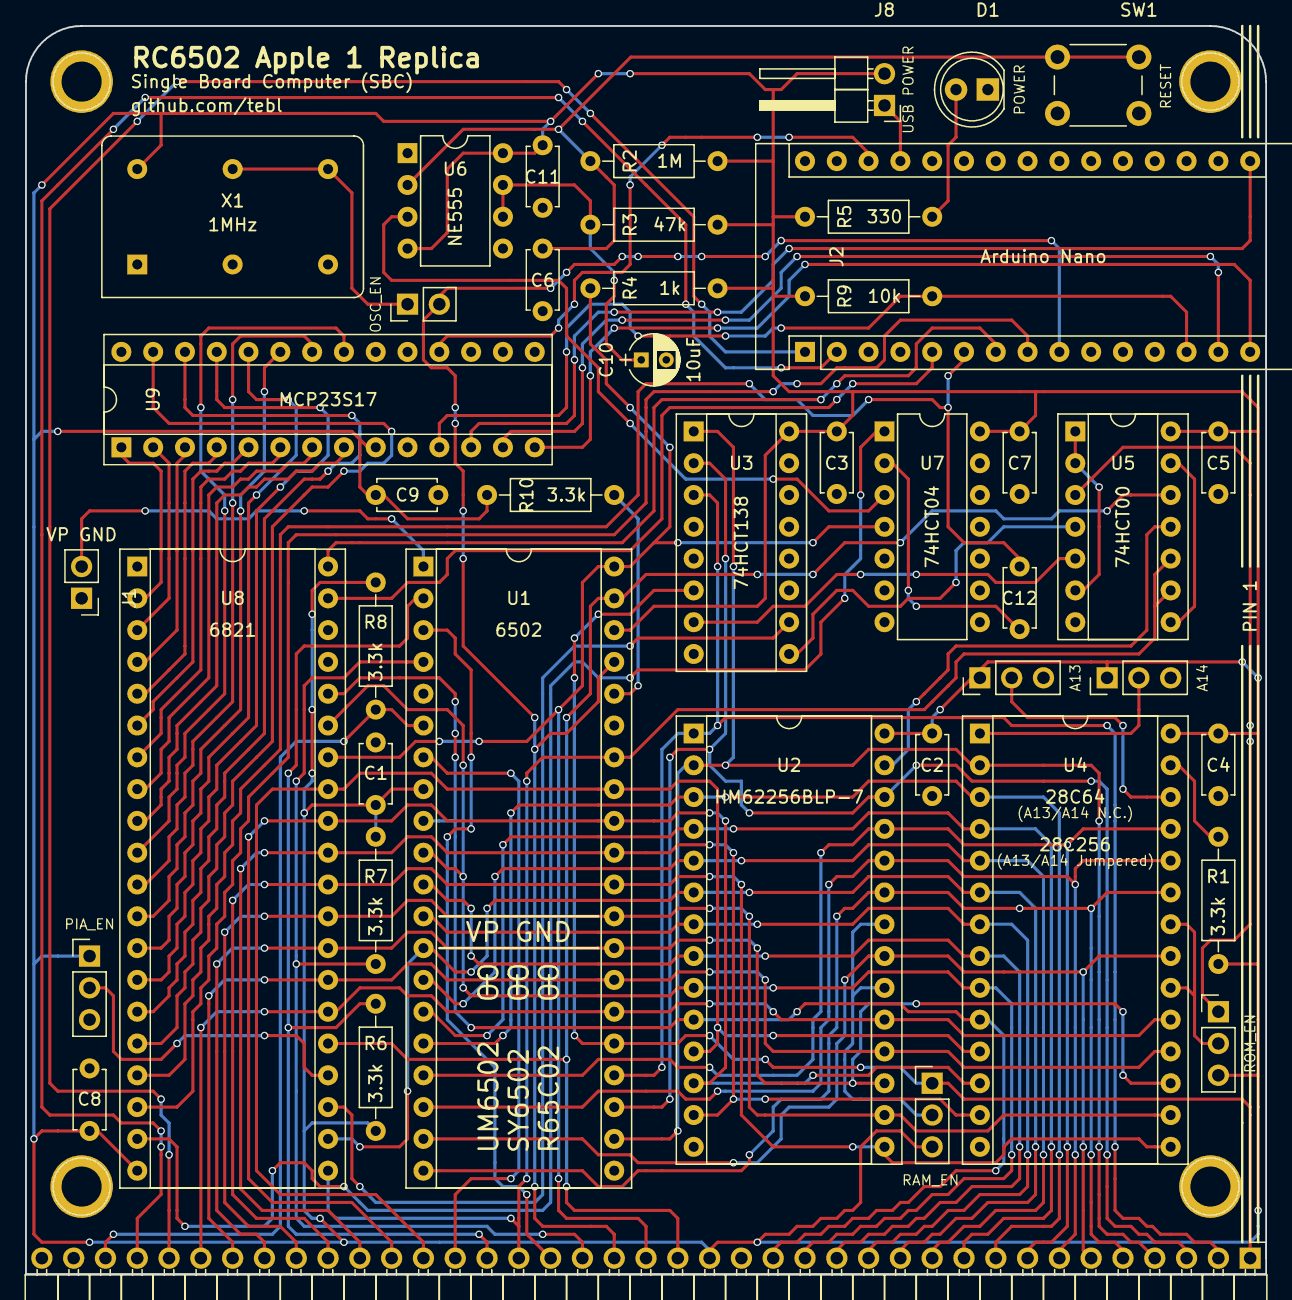
[picture p57: board RC6502 Apple 1 SBC.kicad_pcb from above]

Board: 2 copper layers, 99.1 x 99.7 mm, 48 parts (0 on the bottom side), 84 nets.
