tebl/RC6502-Apple-1-Replica/RC6502 PSG/RC6502 PSG.kicad_pcb

## KiCad design RC6502 PSG/RC6502 PSG.kicad_pcb (2020-01-21)

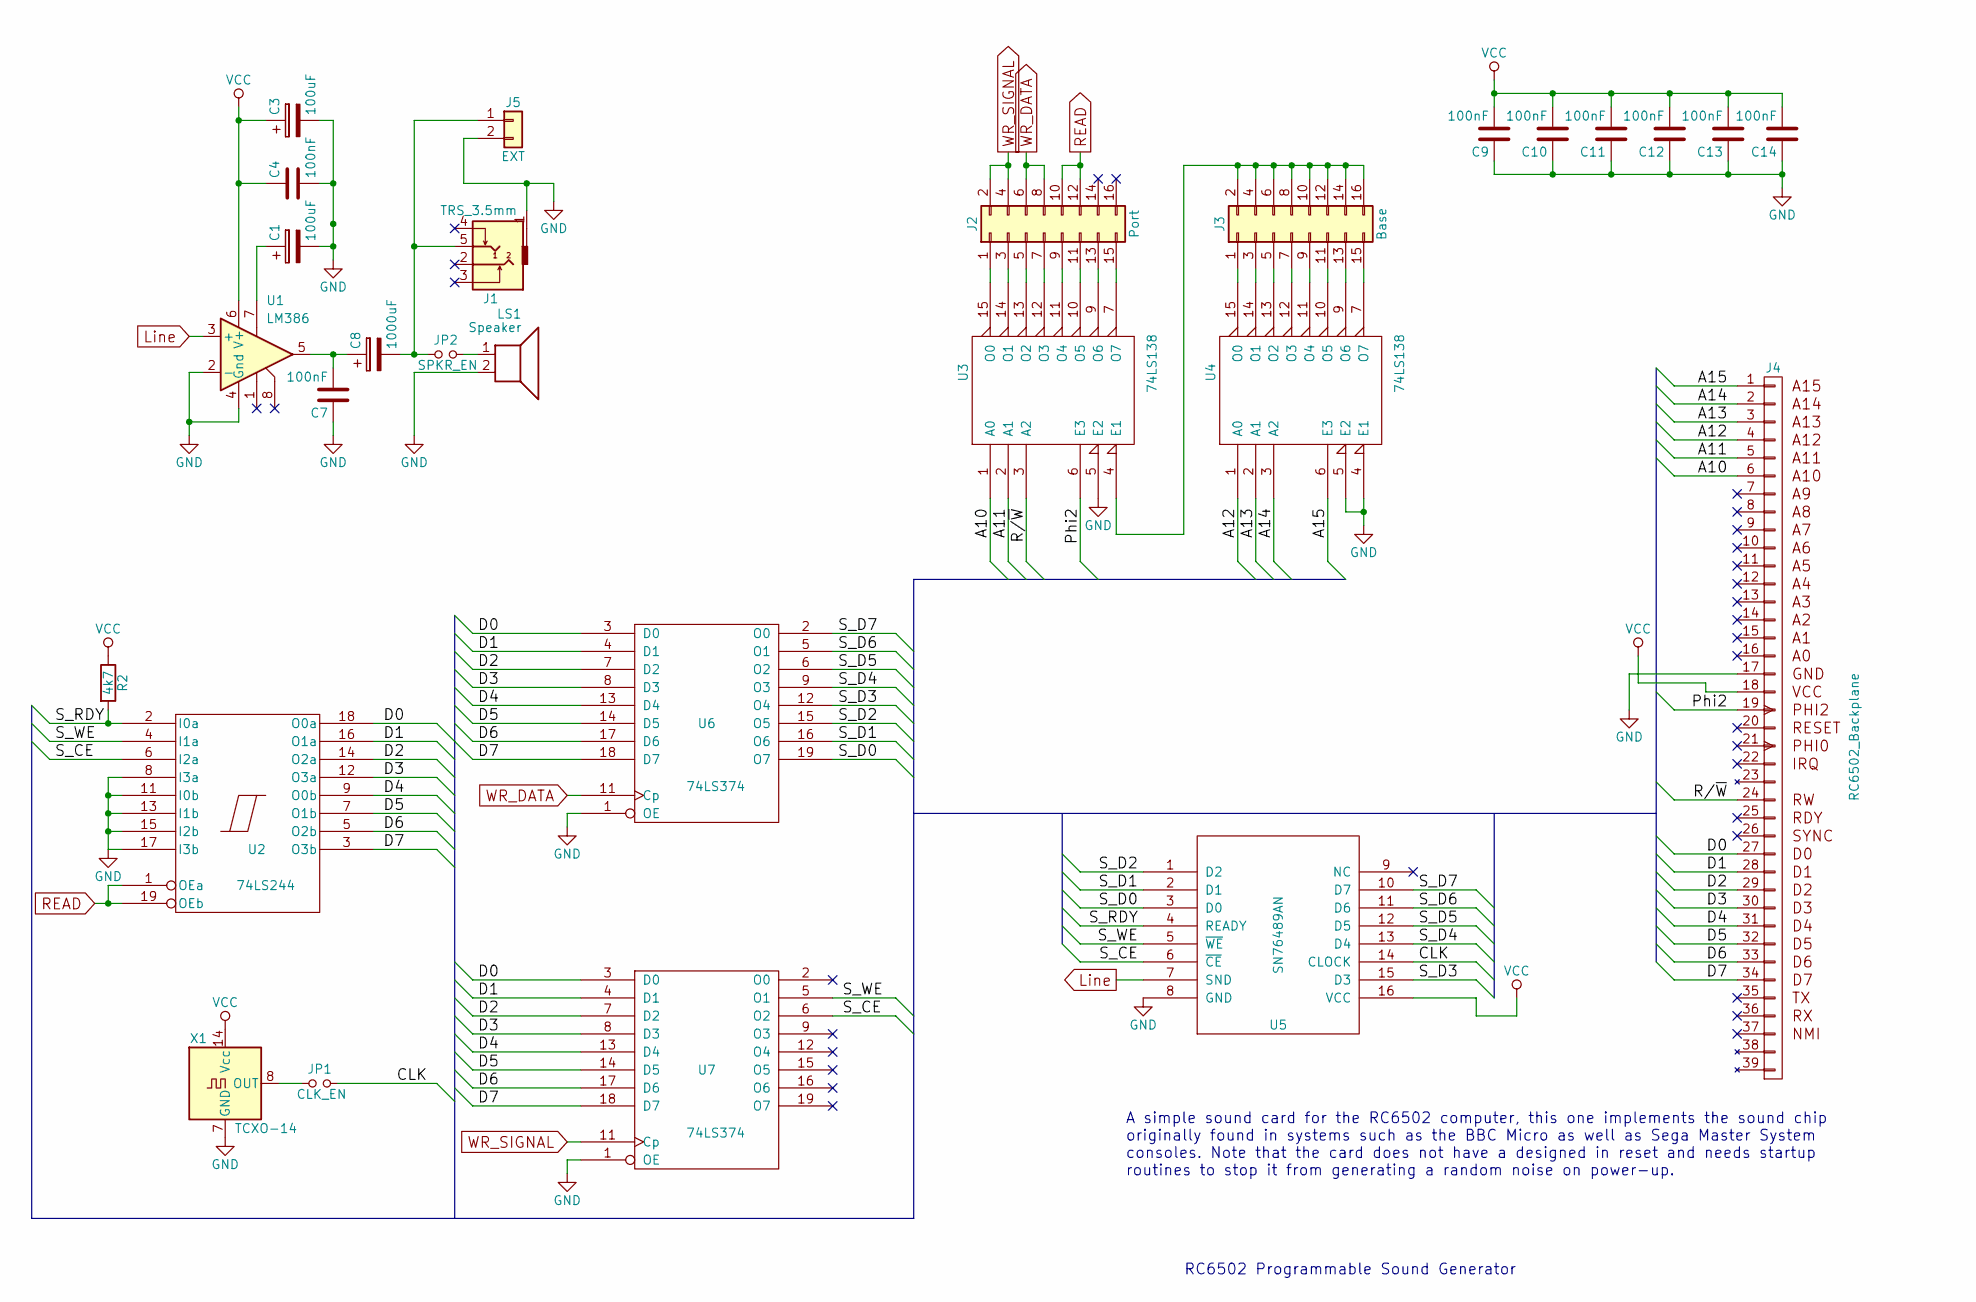
[picture p58: schematic RC6502 PSG.sch]

Parts:
C1, C3: 100uF; CP_Radial_D5.0mm_P2.50mm
C4, C7, C9, C10, C11, C12, C13, C14: 100nF; C_Disc_D4.7mm_W2.5mm_P5.00mm
C8: 1000uF; CP_Radial_D8.0mm_P3.80mm
J1: TRS_3.5mm; Tayda_3.5mm_stereo_TRS_jack_A-853
J2: Port; Pin_Header_Straight_2x08_Pitch2.54mm
J3: Base; Pin_Header_Straight_2x08_Pitch2.54mm
J4: RC6502_Backplane; Pin_Header_Angled_1x39_Pitch2.54mm
J5: EXT; Pin_Header_Angled_1x02_Pitch2.54mm
JP1: CLK_EN; Pin_Header_Straight_1x02_Pitch2.54mm
JP2: SPKR_EN; Pin_Header_Straight_1x02_Pitch2.54mm
LS1: Speaker; Buzzer_12x9.5RM7.6
R2: 4k7; R_Axial_DIN0207_L6.3mm_D2.5mm_P10.16mm_Horizontal
U1: LM386; DIP-8_W7.62mm_Socket
U2: 74LS244; DIP-20_W7.62mm_Socket
U3, U4: 74LS138; DIP-16_W7.62mm_Socket
U5: SN76489AN; DIP-16_W7.62mm_Socket
U6, U7: 74LS374; DIP-20_W7.62mm_Socket
X1: TCXO-14; Oscillator_DIP-14

Connections:
/A10: J4.6 (A10), U3.1 (A0)
/A11: J4.5 (A11), U3.2 (A1)
/A12: J4.4 (A12), U4.1 (A0)
/A13: J4.3 (A13), U4.2 (A1)
/A14: J4.2 (A14), U4.3 (A2)
/A15: J4.1 (A15), U4.6 (E3)
/CLK: JP1.2, U5.14 (CLOCK)
/D0: J4.27 (D0), U2.18 (O0a), U6.3 (D0), U7.3 (D0)
/D1: J4.28 (D1), U2.16 (O1a), U6.4 (D1), U7.4 (D1)
/D2: J4.29 (D2), U2.14 (O2a), U6.7 (D2), U7.7 (D2)
/D3: J4.30 (D3), U2.12 (O3a), U6.8 (D3), U7.8 (D3)
/D4: J4.31 (D4), U2.9 (O0b), U6.13 (D4), U7.13 (D4)
/D5: J4.32 (D5), U2.7 (O1b), U6.14 (D5), U7.14 (D5)
/D6: J4.33 (D6), U2.5 (O2b), U6.17 (D6), U7.17 (D6)
/D7: J4.34 (D7), U2.3 (O3b), U6.18 (D7), U7.18 (D7)
/Phi2: J4.19 (PHI2), U3.6 (E3)
/R/~W: J4.24 (RW), U3.3 (A2)
/S_CE: U2.6 (I2a), U5.6 (~CE), U7.6 (O2)
/S_D0: U5.3 (D0), U6.19 (O7)
/S_D1: U5.2 (D1), U6.16 (O6)
/S_D2: U5.1 (D2), U6.15 (O5)
/S_D3: U5.15 (D3), U6.12 (O4)
/S_D4: U5.13 (D4), U6.9 (O3)
/S_D5: U5.12 (D5), U6.6 (O2)
/S_D6: U5.11 (D6), U6.5 (O1)
/S_D7: U5.10 (D7), U6.2 (O0)
/S_RDY: R2.2, U2.2 (I0a), U5.4 (READY)
/S_WE: U2.4 (I1a), U5.5 (~WE), U7.5 (O1)
GND: C1.2, C3.2, C4.2, C7.1, C9.1, C10.1, C11.1, C12.1, C13.1, C14.1, J1.1, J4.17, J5.2, LS1.2, U1.2 (-), U1.4 (Gnd), U2.8 (I3a), U2.10 (GND), U2.11 (I0b), U2.13 (I1b), U2.15 (I2b), U2.17 (I3b), U3.5 (E2), U3.8 (GND), U4.4 (E1), U4.5 (E2), U4.8 (GND), U5.8 (GND), U6.1 (OE), U6.10 (GND), U7.1 (OE), U7.10 (GND), X1.7 (GND)
Line: U1.3 (+), U5.7 (SND)
unnamed: C1.1, U1.7
unnamed: C7.2, C8.1, U1.5
unnamed: C8.2, J1.5, J5.1, JP2.1
unnamed: J2.1, U3.15 (O0)
unnamed: J2.3, U3.14 (O1)
unnamed: J2.5, U3.13 (O2)
unnamed: J2.7, U3.12 (O3)
unnamed: J2.9, U3.11 (O4)
unnamed: J2.11, U3.10 (O5)
unnamed: J2.13, U3.9 (O6)
unnamed: J2.15, U3.7 (O7)
unnamed: J3.1, U4.15 (O0)
unnamed: J3.3, U4.14 (O1)
unnamed: J3.5, U4.13 (O2)
unnamed: J3.7, U4.12 (O3)
unnamed: J3.9, U4.11 (O4)
unnamed: J3.2, J3.4, J3.6, J3.8, J3.10, J3.12, J3.14, J3.16, U3.4 (E1)
unnamed: J3.11, U4.10 (O5)
unnamed: J3.13, U4.9 (O6)
unnamed: J3.15, U4.7 (O7)
unnamed: JP1.1, X1.8 (OUT)
unnamed: JP2.2, LS1.1
READ: J2.10, J2.12, U2.1 (OEa), U2.19 (OEb)
VCC: C3.1, C4.1, C9.2, C10.2, C11.2, C12.2, C13.2, C14.2, J4.18, R2.1, U1.6 (V+), U2.20 (VCC), U3.16 (VCC), U4.16 (VCC), U5.16 (VCC), U6.20 (VCC), U7.20 (VCC), X1.14 (Vcc)
WR_DATA: J2.6, J2.8, U6.11 (Cp)
WR_SIGNAL: J2.2, J2.4, U7.11 (Cp)

Notes on the sheet:
RC6502 Programmable Sound Generator
A simple sound card for the RC6502 computer, this one implements the sound chip originally found in systems such as the BBC Micro as well as Sega Master System consoles. Note that the card does not have a designed in reset and needs startup routines to stop it from generating a random noise on powe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

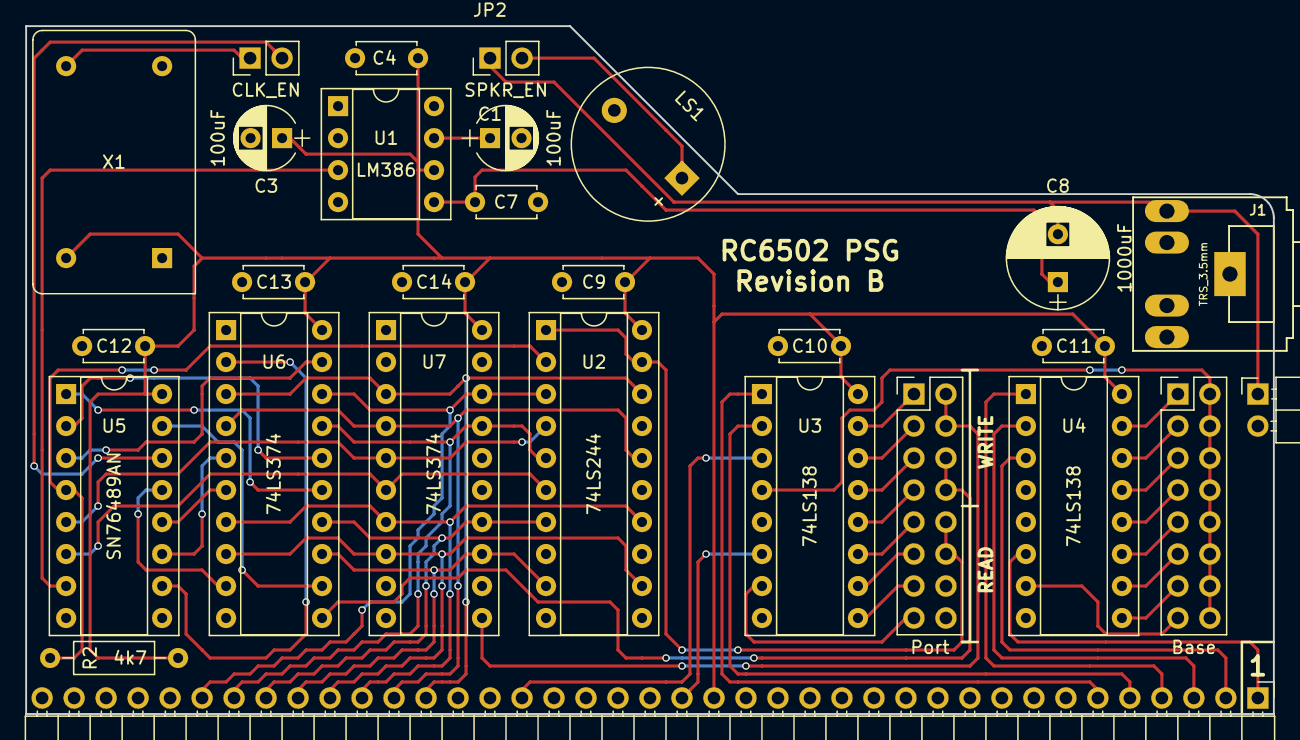
[picture p59: board RC6502 PSG.kicad_pcb from above]

Board: 2 copper layers, 99.1 x 54.6 mm, 28 parts (0 on the bottom side), 56 nets.
