tebl/RC6502-Apple-1-Replica/RC6502 TIA NTSC Clock/RC6502 TIA NTSC Clock.kicad_pcb

## KiCad design RC6502 TIA NTSC Clock/RC6502 TIA NTSC Clock.kicad_pcb (2019-03-08)

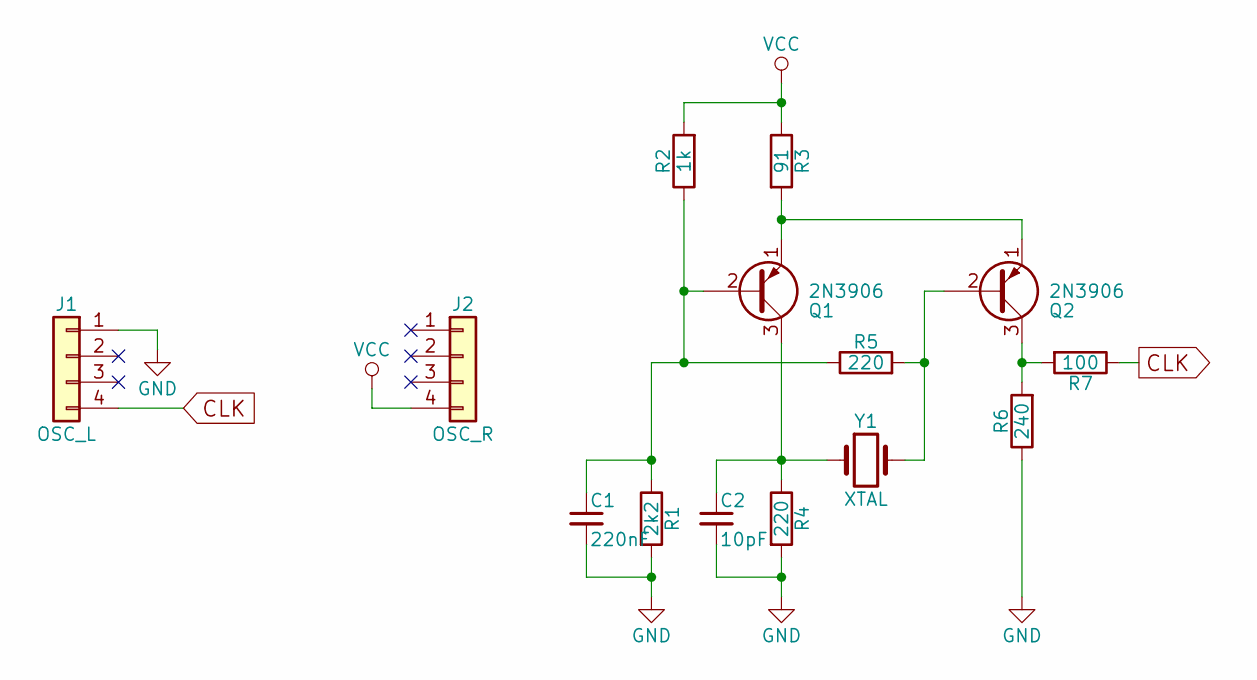
[picture p60: schematic RC6502 TIA NTSC Clock.sch]

Parts:
C1: 220nF; C_Disc_D5.0mm_W2.5mm_P5.00mm
C2: 10pF; C_Disc_D5.0mm_W2.5mm_P5.00mm
J1: OSC_L; Pin_Header_Straight_1x04_Pitch2.54mm
J2: OSC_R; Pin_Header_Straight_1x04_Pitch2.54mm
Q1, Q2: 2N3906; TO-92_Inline_Wide
R1: 2k2; R_Axial_DIN0207_L6.3mm_D2.5mm_P10.16mm_Horizontal
R2: 1k; R_Axial_DIN0207_L6.3mm_D2.5mm_P10.16mm_Horizontal
R3: 91; R_Axial_DIN0207_L6.3mm_D2.5mm_P10.16mm_Horizontal
R4, R5: 220; R_Axial_DIN0207_L6.3mm_D2.5mm_P10.16mm_Horizontal
R6: 240; R_Axial_DIN0207_L6.3mm_D2.5mm_P10.16mm_Horizontal
R7: 100; R_Axial_DIN0207_L6.3mm_D2.5mm_P10.16mm_Horizontal
Y1: XTAL; Crystal_HC49-U_Vertical

Connections:
CLK: J1.4, R7.1
GND: C1.2, C2.2, J1.1, R1.2, R4.2, R6.1
unnamed: C1.1, Q1.2 (B), R1.1, R2.1, R5.1
unnamed: C2.1, Q1.3 (C), R4.1, Y1.1
unnamed: Q1.1 (E), Q2.1 (E), R3.2
unnamed: Q2.2 (B), R5.2, Y1.2
unnamed: Q2.3 (C), R6.2, R7.2
VCC: J2.4, R2.2, R3.1

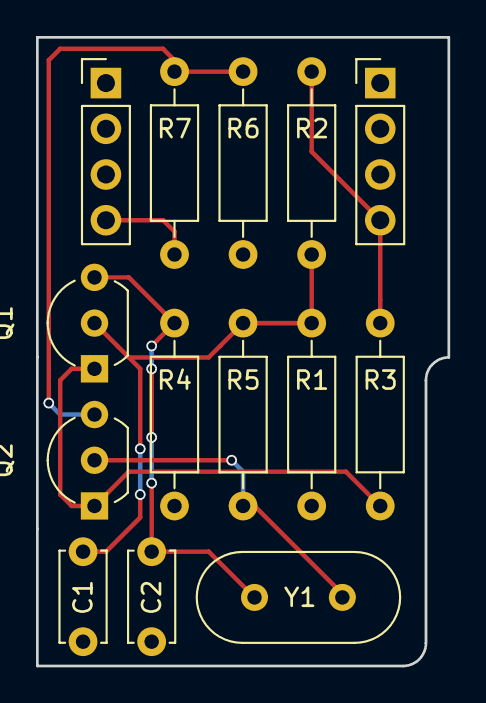
[picture p61: board RC6502 TIA NTSC Clock.kicad_pcb from above]

Board: 2 copper layers, 22.9 x 34.9 mm, 14 parts (0 on the bottom side), 8 nets.
