tebl/RC6502-Apple-1-Replica/RC6502 VDU Color Amplifier/RC6502 VDU Color.kicad_pcb

## KiCad design RC6502 VDU Color Amplifier/RC6502 VDU Color.kicad_pcb (2019-02-28)

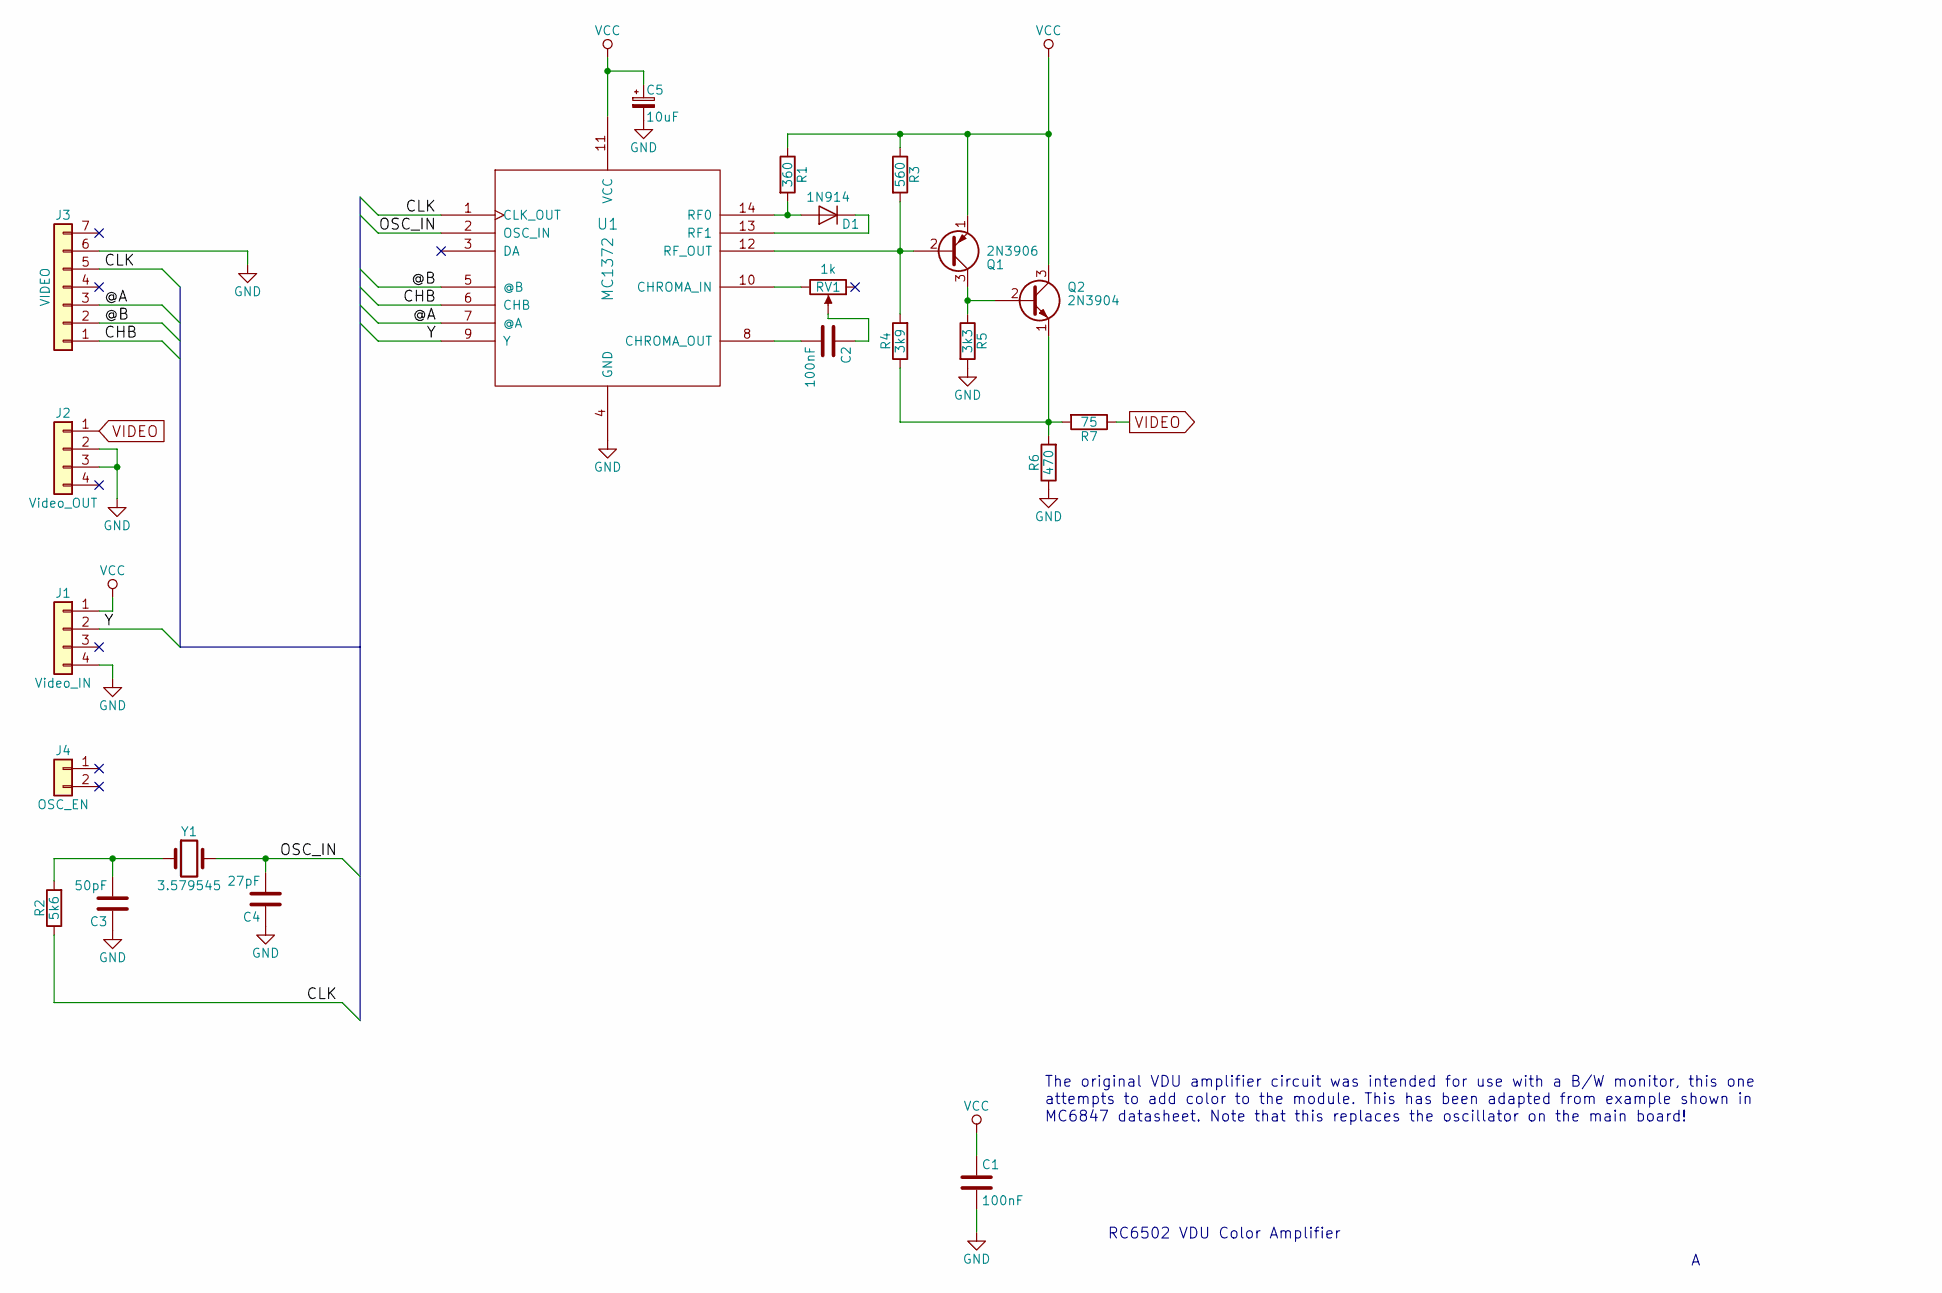
[picture p62: schematic RC6502 VDU Color.sch]

Parts:
C1, C2: 100nF; C_Disc_D4.7mm_W2.5mm_P5.00mm
C3: 50pF; C_Disc_D4.7mm_W2.5mm_P5.00mm
C4: 27pF; C_Disc_D4.7mm_W2.5mm_P5.00mm
C5: 10uF; CP_Radial_D4.0mm_P2.00mm
D1: 1N914; D_DO-35_SOD27_P7.62mm_Horizontal
J1: Video_IN; Pin_Header_Straight_1x04_Pitch2.54mm
J2: Video_OUT; Pin_Header_Straight_1x04_Pitch2.54mm
J3: VIDEO; Pin_Header_Straight_1x07_Pitch2.54mm
J4: OSC_EN; Pin_Header_Straight_1x02_Pitch2.54mm
Q1: 2N3906; TO-92_Inline_Wide
Q2: 2N3904; TO-92_Inline_Wide
R1: 360; R_Axial_DIN0207_L6.3mm_D2.5mm_P10.16mm_Horizontal
R2: 5k6; R_Axial_DIN0207_L6.3mm_D2.5mm_P10.16mm_Horizontal
R3: 560; R_Axial_DIN0207_L6.3mm_D2.5mm_P10.16mm_Horizontal
R4: 3k9; R_Axial_DIN0207_L6.3mm_D2.5mm_P10.16mm_Horizontal
R5: 3k3; R_Axial_DIN0207_L6.3mm_D2.5mm_P10.16mm_Horizontal
R6: 470; R_Axial_DIN0207_L6.3mm_D2.5mm_P10.16mm_Horizontal
R7: 75; R_Axial_DIN0207_L6.3mm_D2.5mm_P10.16mm_Horizontal
RV1: 1k; Potentiometer_Trimmer_Bourns_3296W
U1: MC1372; DIP-14_W7.62mm_Socket
Y1: 3.579545; Crystal_HC49-U_Vertical

Connections:
/@A: J3.3, U1.7 (@A)
/@B: J3.2, U1.5 (@B)
/CHB: J3.1, U1.6 (CHB)
/CLK: J3.5, R2.1, U1.1 (CLK_OUT)
/OSC_IN: C4.2, U1.2 (OSC_IN), Y1.2
/Y: J1.2, U1.9 (Y)
GND: C1.2, C3.1, C4.1, C5.2, J1.4, J2.2, J2.3, J3.6, R5.2, R6.1, U1.4 (GND)
unnamed: C2.1, RV1.2
unnamed: C2.2, U1.8 (CHROMA_OUT)
unnamed: C3.2, R2.2, Y1.1
unnamed: D1.1 (K), U1.13 (RF1)
unnamed: D1.2 (A), R1.2, U1.14 (RF0)
unnamed: Q1.2 (B), R3.2, R4.2, U1.12 (RF_OUT)
unnamed: Q1.3 (C), Q2.2 (B), R5.1
unnamed: Q2.1 (E), R4.1, R6.2, R7.2
unnamed: RV1.3, U1.10 (CHROMA_IN)
VCC: C1.1, C5.1, J1.1, Q1.1 (E), Q2.3 (C), R1.1, R3.1, U1.11 (VCC)
VIDEO: J2.1, R7.1

Notes on the sheet:
RC6502 VDU Color Amplifier
The original VDU amplifier circuit was intended for use with a B/W monitor, this one attempts to add color to the module. This has been adapted from example shown in MC6847 datasheet. Note that this replaces the oscillator on the main board!

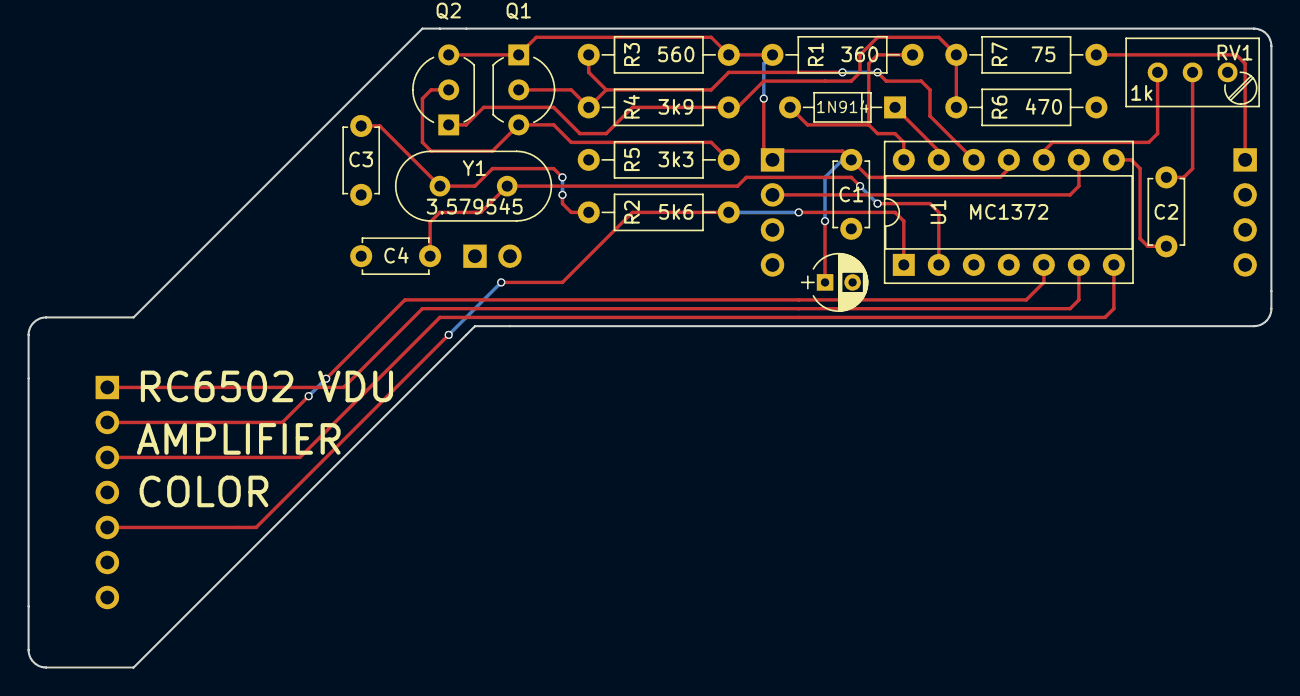
[picture p63: board RC6502 VDU Color.kicad_pcb from above]

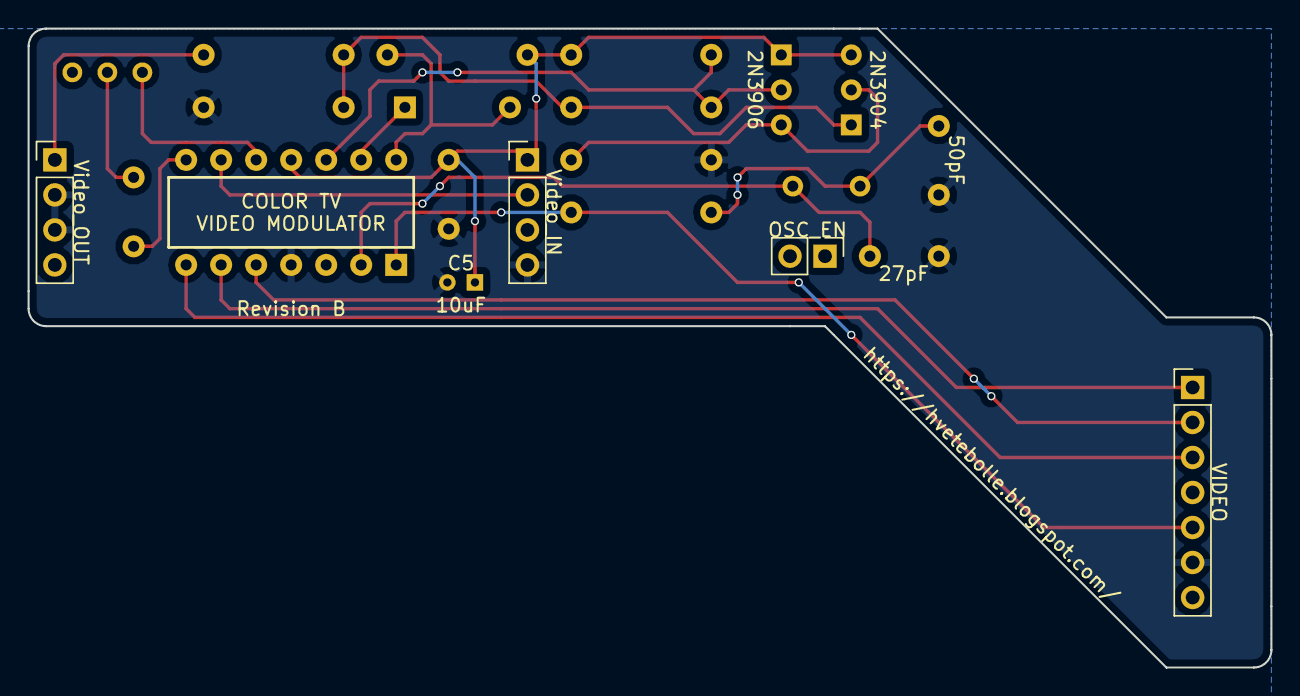
[picture p64: board RC6502 VDU Color.kicad_pcb from below]

Board: 2 copper layers, 90.2 x 46.4 mm, 22 parts (4 on the bottom side), 18 nets.
