tebl/RC6502-Apple-1-Replica/RC6502 VDU/RC6502 VDU.kicad_pcb

## KiCad design RC6502 VDU/RC6502 VDU.kicad_pcb (2019-02-27)

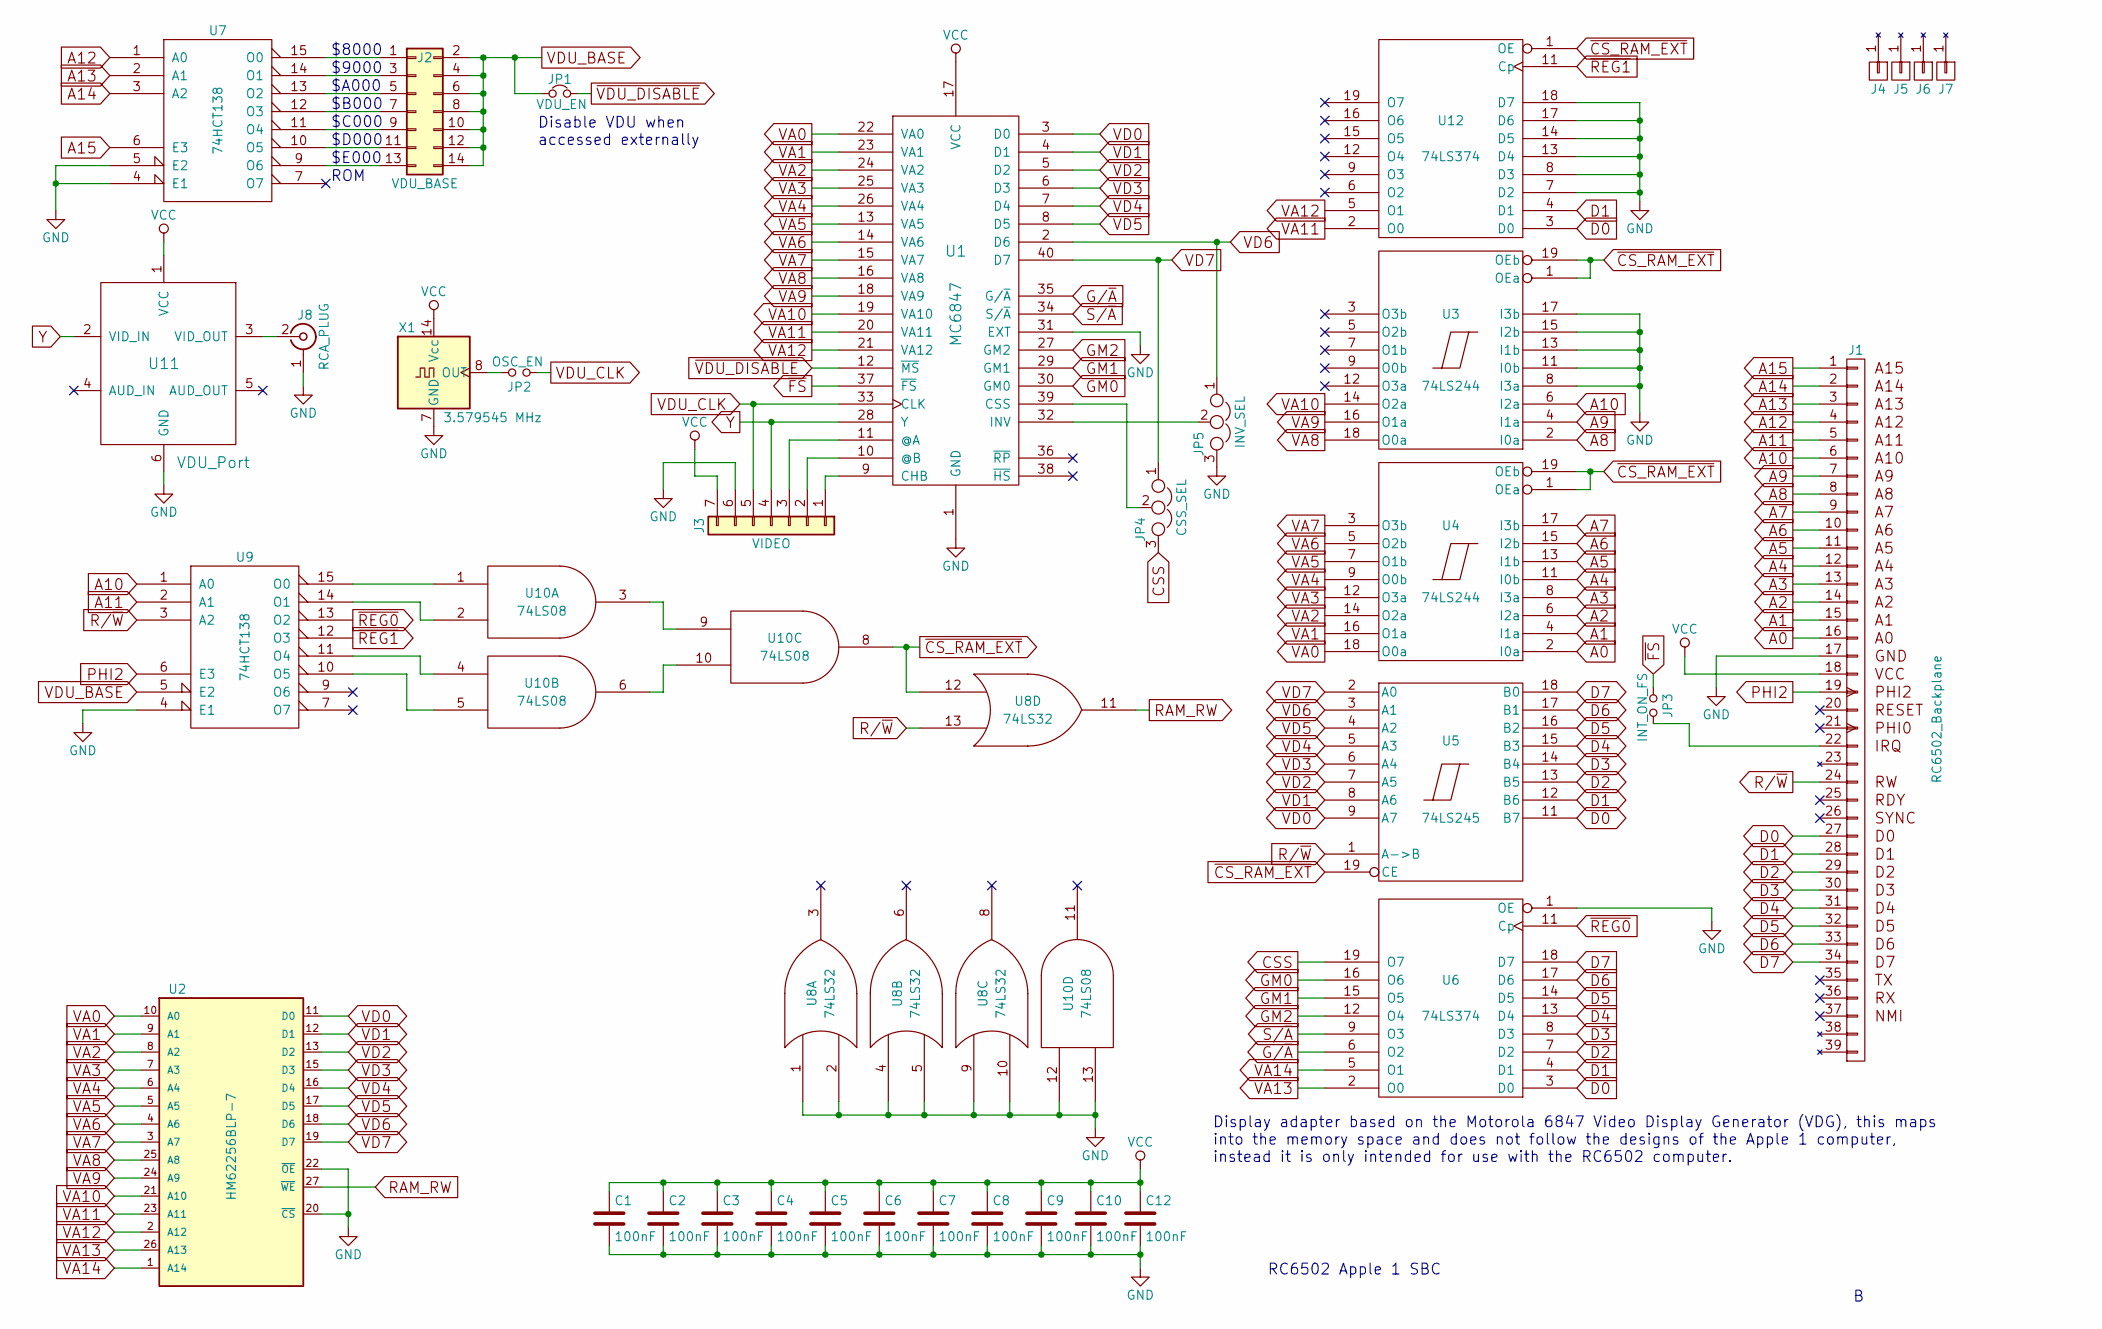
[picture p65: schematic RC6502 VDU.sch]

Parts:
C1, C2, C3, C4, C5, C6, C7, C8, C9, C10, C12: 100nF; C_Disc_D4.7mm_W2.5mm_P5.00mm
J1: RC6502_Backplane; Pin_Header_Angled_1x39_Pitch2.54mm
J2: VDU_BASE; Pin_Header_Straight_2x07_Pitch2.54mm
J3: VIDEO; Pin_Header_Straight_1x07_Pitch2.54mm
J4, J5, J6, J7: Hole; Mounting
J8: RCA_PLUG; rca_yellow
JP1: VDU_EN; Pin_Header_Straight_1x02_Pitch2.54mm
JP2: OSC_EN; Pin_Header_Straight_1x02_Pitch2.54mm
JP3: INT_ON_FS; Pin_Header_Straight_1x02_Pitch2.54mm
JP4: CSS_SEL; Pin_Header_Straight_1x03_Pitch2.54mm
JP5: INV_SEL; Pin_Header_Straight_1x03_Pitch2.54mm
U1: MC6847; DIP-40_W15.24mm_Socket
U2: HM62256BLP-7; DIP-28_W15.24mm_Socket
U3, U4: 74LS244; DIP-20_W7.62mm_Socket
U5: 74LS245; DIP-20_W7.62mm_Socket
U6, U12: 74LS374; DIP-20_W7.62mm_Socket
U7, U9: 74HCT138; DIP-16_W7.62mm_Socket
U8: 74LS32; DIP-14_W7.62mm_Socket
U10: 74LS08; DIP-14_W7.62mm_Socket
U11: VDU_Port; Amplifier
X1: 3.579545 MHz; Oscillator_DIP-14

Connections:
A0: J1.16 (A0), U4.2 (I0a)
A1: J1.15 (A1), U4.4 (I1a)
A2: J1.14 (A2), U4.6 (I2a)
A3: J1.13 (A3), U4.8 (I3a)
A4: J1.12 (A4), U4.11 (I0b)
A5: J1.11 (A5), U4.13 (I1b)
A6: J1.10 (A6), U4.15 (I2b)
A7: J1.9 (A7), U4.17 (I3b)
A8: J1.8 (A8), U3.2 (I0a)
A9: J1.7 (A9), U3.4 (I1a)
A10: J1.6 (A10), U3.6 (I2a), U9.1 (A0)
A11: J1.5 (A11), U9.2 (A1)
A12: J1.4 (A12), U7.1 (A0)
A13: J1.3 (A13), U7.2 (A1)
A14: J1.2 (A14), U7.3 (A2)
A15: J1.1 (A15), U7.6 (E3)
CSS: JP4.3, U6.19 (O7)
D0: J1.27 (D0), U5.11 (B7), U6.3 (D0), U12.3 (D0)
D1: J1.28 (D1), U5.12 (B6), U6.4 (D1), U12.4 (D1)
D2: J1.29 (D2), U5.13 (B5), U6.7 (D2)
D3: J1.30 (D3), U5.14 (B4), U6.8 (D3)
D4: J1.31 (D4), U5.15 (B3), U6.13 (D4)
D5: J1.32 (D5), U5.16 (B2), U6.14 (D5)
D6: J1.33 (D6), U5.17 (B1), U6.17 (D6)
D7: J1.34 (D7), U5.18 (B0), U6.18 (D7)
G/~A: U1.35 (G/~A), U6.6 (O2)
GM0: U1.30 (GM0), U6.16 (O6)
GM1: U1.29 (GM1), U6.15 (O5)
GM2: U1.27 (GM2), U6.12 (O4)
GND: C1.2, C2.2, C3.2, C4.2, C5.2, C6.2, C7.2, C8.2, C9.2, C10.2, C12.2, J1.17, J3.6, J8.1 (Ext), JP5.3, U1.1 (GND), U1.31 (EXT), U2.14 (GND), U2.20 (~CS), U2.22 (~OE), U3.8 (I3a), U3.10 (GND), U3.11 (I0b), U3.13 (I1b), U3.15 (I2b), U3.17 (I3b), U4.10 (GND), U5.10 (GND), U6.1 (OE), U6.10 (GND), U7.4 (E1), U7.5 (E2), U7.8 (GND), U8.1, U8.2, U8.4, U8.5, U8.7 (GND), U8.9, U8.10, U9.4 (E1), U9.8 (GND), U10.7 (GND), U10.12, U10.13, U11.6 (GND), U12.7 (D2), U12.8 (D3), U12.10 (GND), U12.13 (D4), U12.14 (D5), U12.17 (D6), U12.18 (D7), X1.7 (GND)
unnamed: J1.22 (IRQ), JP3.2
unnamed: J2.1, U7.15 (O0)
unnamed: J2.3, U7.14 (O1)
unnamed: J2.5, U7.13 (O2)
unnamed: J2.7, U7.12 (O3)
unnamed: J2.9, U7.11 (O4)
unnamed: J2.11, U7.10 (O5)
unnamed: J2.13, U7.9 (O6)
unnamed: J3.1, U1.9 (CHB)
unnamed: J3.2, U1.10 (@B)
unnamed: J3.3, U1.11 (@A)
unnamed: J8.2 (In), U11.3 (VID_OUT)
unnamed: JP2.2, X1.8 (OUT)
unnamed: JP4.2, U1.39 (CSS)
unnamed: JP5.2, U1.32 (INV)
unnamed: U9.15 (O0), U10.1
unnamed: U9.14 (O1), U10.2
unnamed: U10.3, U10.9
unnamed: U9.11 (O4), U10.4
unnamed: U9.10 (O5), U10.5
unnamed: U10.6, U10.10
PHI2: J1.19 (PHI2), U9.6 (E3)
R/~W: J1.24 (RW), U5.1 (A->B), U8.13, U9.3 (A2)
RAM_RW: U2.27 (~WE), U8.11
S/~A: U1.34 (S/~A), U6.9 (O3)
VA0: U1.22 (VA0), U2.10 (A0), U4.18 (O0a)
VA1: U1.23 (VA1), U2.9 (A1), U4.16 (O1a)
VA2: U1.24 (VA2), U2.8 (A2), U4.14 (O2a)
VA3: U1.25 (VA3), U2.7 (A3), U4.12 (O3a)
VA4: U1.26 (VA4), U2.6 (A4), U4.9 (O0b)
VA5: U1.13 (VA5), U2.5 (A5), U4.7 (O1b)
VA6: U1.14 (VA6), U2.4 (A6), U4.5 (O2b)
VA7: U1.15 (VA7), U2.3 (A7), U4.3 (O3b)
VA8: U1.16 (VA8), U2.25 (A8), U3.18 (O0a)
VA9: U1.18 (VA9), U2.24 (A9), U3.16 (O1a)
VA10: U1.19 (VA10), U2.21 (A10), U3.14 (O2a)
VA11: U1.20 (VA11), U2.23 (A11), U12.2 (O0)
VA12: U1.21 (VA12), U2.2 (A12), U12.5 (O1)
VA13: U2.26 (A13), U6.2 (O0)
VA14: U2.1 (A14), U6.5 (O1)
VCC: C1.1, C2.1, C3.1, C4.1, C5.1, C6.1, C7.1, C8.1, C9.1, C10.1, C12.1, J1.18, J3.7, U1.17 (VCC), U2.28 (VCC), U3.20 (VCC), U4.20 (VCC), U5.20 (VCC), U6.20 (VCC), U7.16 (VCC), U8.14 (VCC), U9.16 (VCC), U10.14 (VCC), U11.1 (VCC), U12.20 (VCC), X1.14 (Vcc)
VD0: U1.3 (D0), U2.11 (D0), U5.9 (A7)
VD1: U1.4 (D1), U2.12 (D1), U5.8 (A6)
VD2: U1.5 (D2), U2.13 (D2), U5.7 (A5)
VD3: U1.6 (D3), U2.15 (D3), U5.6 (A4)
VD4: U1.7 (D4), U2.16 (D4), U5.5 (A3)
VD5: U1.8 (D5), U2.17 (D5), U5.4 (A2)
VD6: JP5.1, U1.2 (D6), U2.18 (D6), U5.3 (A1)
VD7: JP4.1, U1.40 (D7), U2.19 (D7), U5.2 (A0)
VDU_BASE: J2.2, J2.4, J2.6, J2.8, J2.10, J2.12, J2.14, JP1.1, U9.5 (E2)
VDU_CLK: J3.5, JP2.1, U1.33 (CLK)
Y: J3.4, U1.28 (Y), U11.2 (VID_IN)
~CS_RAM_EXT: U3.1 (OEa), U3.19 (OEb), U4.1 (OEa), U4.19 (OEb), U5.19 (CE), U8.12, U10.8, U12.1 (OE)
~FS: JP3.1, U1.37 (~FS)
~REG0: U6.11 (Cp), U9.13 (O2)
~REG1: U9.12 (O3), U12.11 (Cp)
~VDU_DISABLE: JP1.2, U1.12 (~MS)

Notes on the sheet:
RC6502 Apple 1 SBC
ROM
$C000
$B000
$A000
$9000
$8000
Disable VDU when accessed externally
Display adapter based on the Motorola 6847 Video Display Generator (VDG), this maps into the memory space and does not follow the designs of the Apple 1 computer, instead it is only intended for use with the RC6502 computer.
$D000
$E000

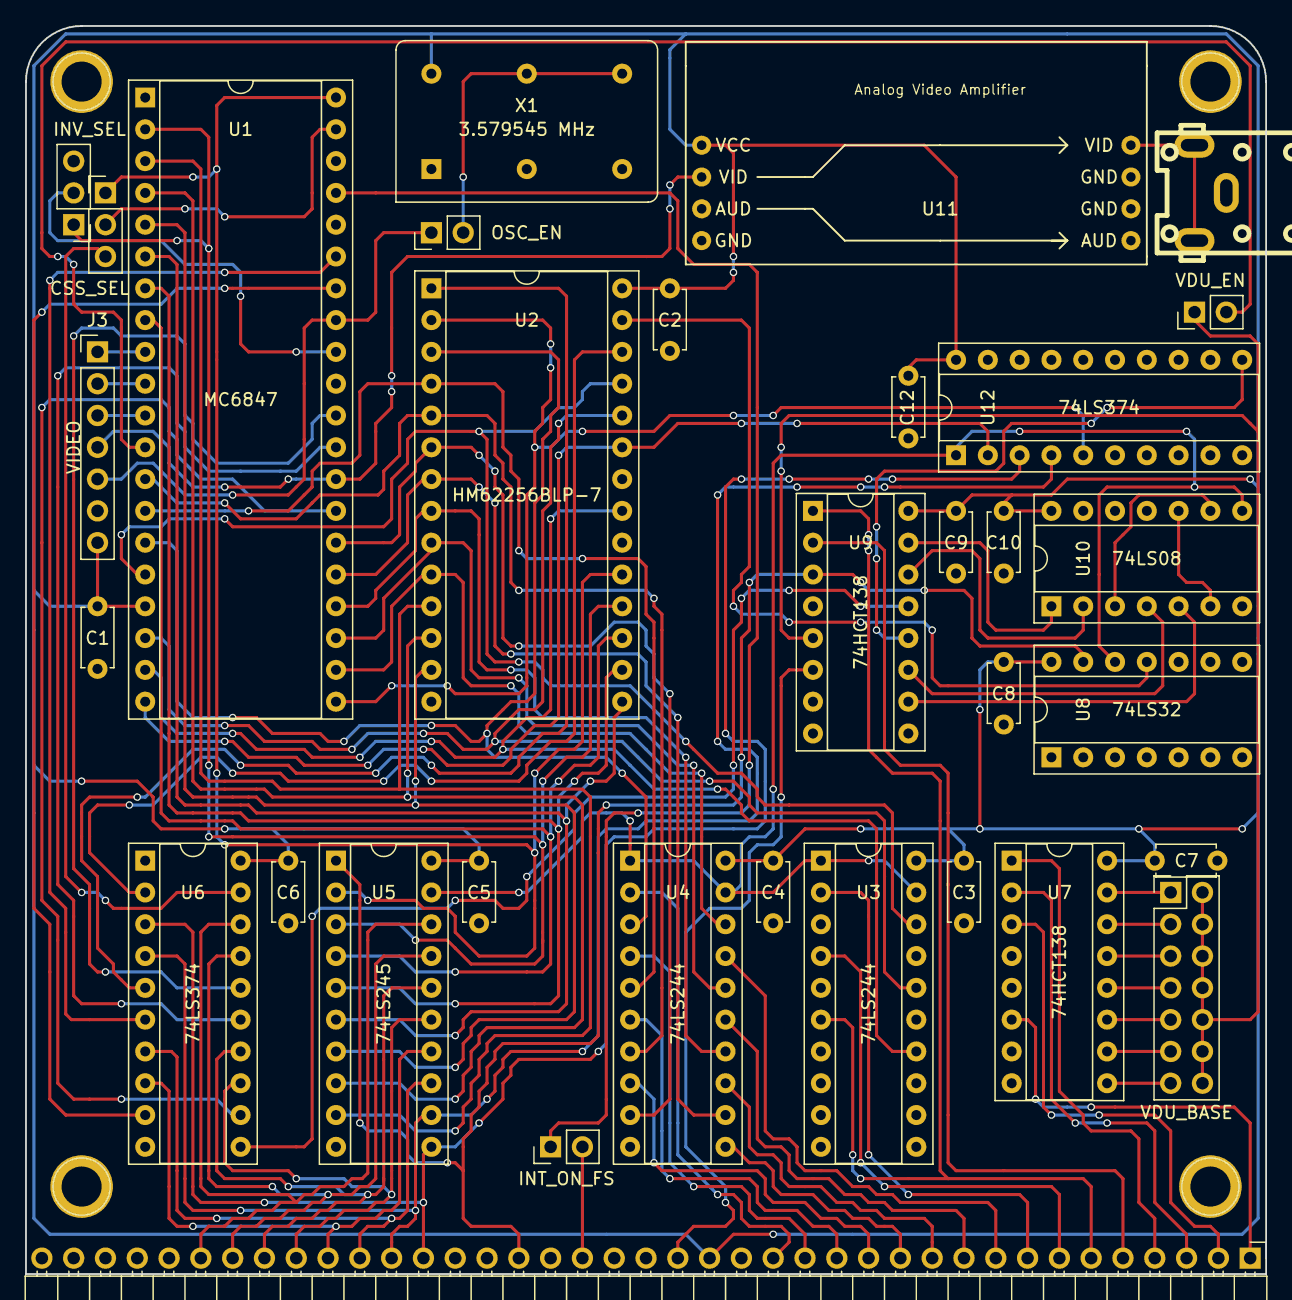
[picture p66: board RC6502 VDU.kicad_pcb from above]

Board: 2 copper layers, 99.1 x 99.7 mm, 37 parts (0 on the bottom side), 87 nets.
