tebl/RC6502-Apple-1-Replica/RC6502 RIOT/RC6502 RIOT.kicad_pcb

## KiCad design RC6502 RIOT/RC6502 RIOT.kicad_pcb (2019-02-20)

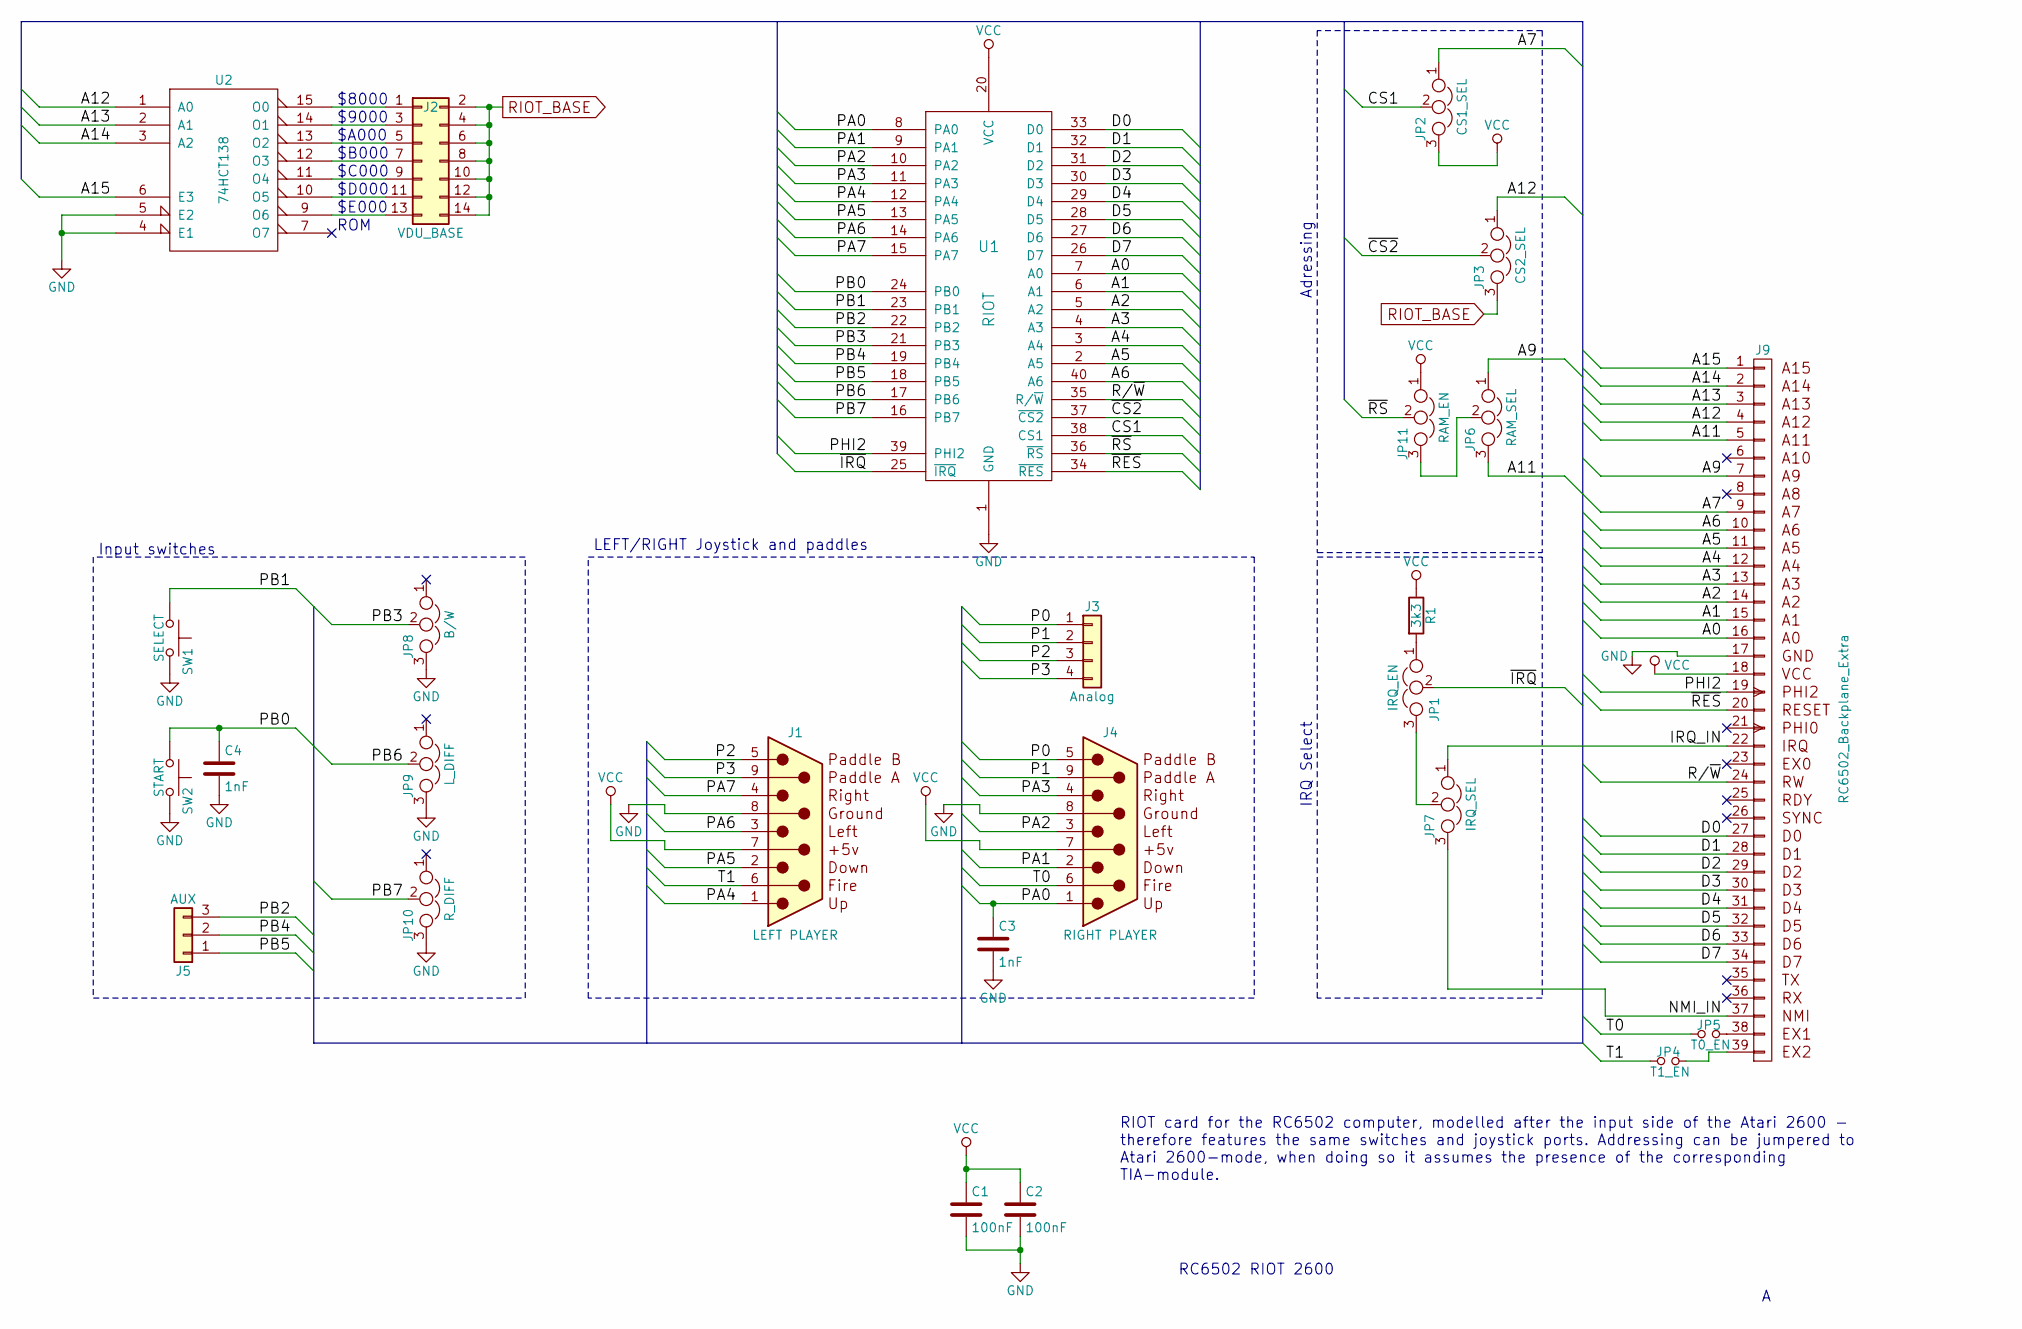
[picture p67: schematic RC6502 RIOT.sch]

Parts:
C1, C2: 100nF; C_Disc_D4.7mm_W2.5mm_P5.00mm
C3, C4: 1nF; C_Disc_D4.7mm_W2.5mm_P5.00mm
J1: LEFT PLAYER; DSUB-9_Male_Vertical_Pitch2.77x2.84mm
J2: VDU_BASE; Pin_Header_Straight_2x07_Pitch2.54mm
J3: Analog; Pin_Header_Straight_1x04_Pitch2.54mm
J4: RIGHT PLAYER; DSUB-9_Male_Vertical_Pitch2.77x2.84mm
J5: AUX; Pin_Header_Straight_1x03_Pitch2.54mm
J9: RC6502_Backplane_Extra; Pin_Header_Angled_1x39_Pitch2.54mm
JP1: IRQ_EN; Pin_Header_Straight_1x03_Pitch2.54mm
JP2: CS1_SEL; Pin_Header_Straight_1x03_Pitch2.54mm
JP3: CS2_SEL; Pin_Header_Straight_1x03_Pitch2.54mm
JP4: T1_EN; Pin_Header_Straight_1x02_Pitch2.54mm
JP5: T0_EN; Pin_Header_Straight_1x02_Pitch2.54mm
JP6: RAM_SEL; Pin_Header_Straight_1x03_Pitch2.54mm
JP7: IRQ_SEL; Pin_Header_Straight_1x03_Pitch2.54mm
JP8: B/W; Pin_Header_Straight_1x03_Pitch2.54mm
JP9: L_DIFF; Pin_Header_Straight_1x03_Pitch2.54mm
JP10: R_DIFF; Pin_Header_Straight_1x03_Pitch2.54mm
JP11: RAM_EN; Pin_Header_Straight_1x03_Pitch2.54mm
R1: 3k3; R_Axial_DIN0207_L6.3mm_D2.5mm_P10.16mm_Horizontal
SW1: SELECT; SW_PUSH_6mm
SW2: START; SW_PUSH_6mm
U1: RIOT; DIP-40_W15.24mm_Socket
U2: 74HCT138; DIP-16_W7.62mm_Socket

Connections:
/A0: J9.16 (A0), U1.7 (A0)
/A1: J9.15 (A1), U1.6 (A1)
/A2: J9.14 (A2), U1.5 (A2)
/A3: J9.13 (A3), U1.4 (A3)
/A4: J9.12 (A4), U1.3 (A4)
/A5: J9.11 (A5), U1.2 (A5)
/A6: J9.10 (A6), U1.40 (A6)
/A7: J9.9 (A7), JP2.1
/A9: J9.7 (A9), JP6.1
/A11: J9.5 (A11), JP6.3
/A12: J9.4 (A12), JP3.1, U2.1 (A0)
/A13: J9.3 (A13), U2.2 (A1)
/A14: J9.2 (A14), U2.3 (A2)
/A15: J9.1 (A15), U2.6 (E3)
/CS1: JP2.2, U1.38 (CS1)
/D0: J9.27 (D0), U1.33 (D0)
/D1: J9.28 (D1), U1.32 (D1)
/D2: J9.29 (D2), U1.31 (D2)
/D3: J9.30 (D3), U1.30 (D3)
/D4: J9.31 (D4), U1.29 (D4)
/D5: J9.32 (D5), U1.28 (D5)
/D6: J9.33 (D6), U1.27 (D6)
/D7: J9.34 (D7), U1.26 (D7)
/IRQ_IN: J9.22 (IRQ), JP7.1
/NMI_IN: J9.37 (NMI), JP7.3
/P0: J3.1, J4.5
/P1: J3.2, J4.9
/P2: J1.5, J3.3
/P3: J1.9, J3.4
/PA0: C3.1, J4.1, U1.8 (PA0)
/PA1: J4.2, U1.9 (PA1)
/PA2: J4.3, U1.10 (PA2)
/PA3: J4.4, U1.11 (PA3)
/PA4: J1.1, U1.12 (PA4)
/PA5: J1.2, U1.13 (PA5)
/PA6: J1.3, U1.14 (PA6)
/PA7: J1.4, U1.15 (PA7)
/PB0: C4.1, SW2.1, U1.24 (PB0)
/PB1: SW1.1, U1.23 (PB1)
/PB2: J5.3, U1.22 (PB2)
/PB3: JP8.2, U1.21 (PB3)
/PB4: J5.2, U1.19 (PB4)
/PB5: J5.1, U1.18 (PB5)
/PB6: JP9.2, U1.17 (PB6)
/PB7: JP10.2, U1.16 (PB7)
/PHI2: J9.19 (PHI2), U1.39 (PHI2)
/R/~W: J9.24 (RW), U1.35 (R/~W)
/T0: J4.6, JP5.1
/T1: J1.6, JP4.1
/~CS2: JP3.2, U1.37 (~CS2)
/~IRQ: JP1.2, U1.25 (~IRQ)
/~RES: J9.20 (RESET), U1.34 (~RES)
/~RS: JP11.2, U1.36 (~RS)
GND: C1.2, C2.2, C3.2, C4.2, J1.8, J4.8, J9.17, JP8.3, JP9.3, JP10.3, SW1.2, SW2.2, U1.1 (GND), U2.4 (E1), U2.5 (E2), U2.8 (GND)
unnamed: J2.1, U2.15 (O0)
unnamed: J2.3, U2.14 (O1)
unnamed: J2.5, U2.13 (O2)
unnamed: J2.7, U2.12 (O3)
unnamed: J2.9, U2.11 (O4)
unnamed: J2.11, U2.10 (O5)
unnamed: J2.13, U2.9 (O6)
unnamed: J9.38 (EX1), JP5.2
unnamed: J9.39 (EX2), JP4.2
unnamed: JP1.1, R1.2
unnamed: JP1.3, JP7.2
unnamed: JP6.2, JP11.3
RIOT_BASE: J2.2, J2.4, J2.6, J2.8, J2.10, J2.12, J2.14, JP3.3
VCC: C1.1, C2.1, J1.7, J4.7, J9.18, JP2.3, JP11.1, R1.1, U1.20 (VCC), U2.16 (VCC)

Notes on the sheet:
RC6502 RIOT 2600
ROM
$C000
$B000
$A000
$9000
$8000
$D000
$E000
Adressing
IRQ Select
LEFT/RIGHT Joystick and paddles
Input switches
RIOT card for the RC6502 computer, modelled after the input side of the Atari 2600 - therefore features the same switches and joystick ports. Addressing can be jumpered to Atari 2600-mode, when doing so it assumes the presence of the corresponding TIA-module.

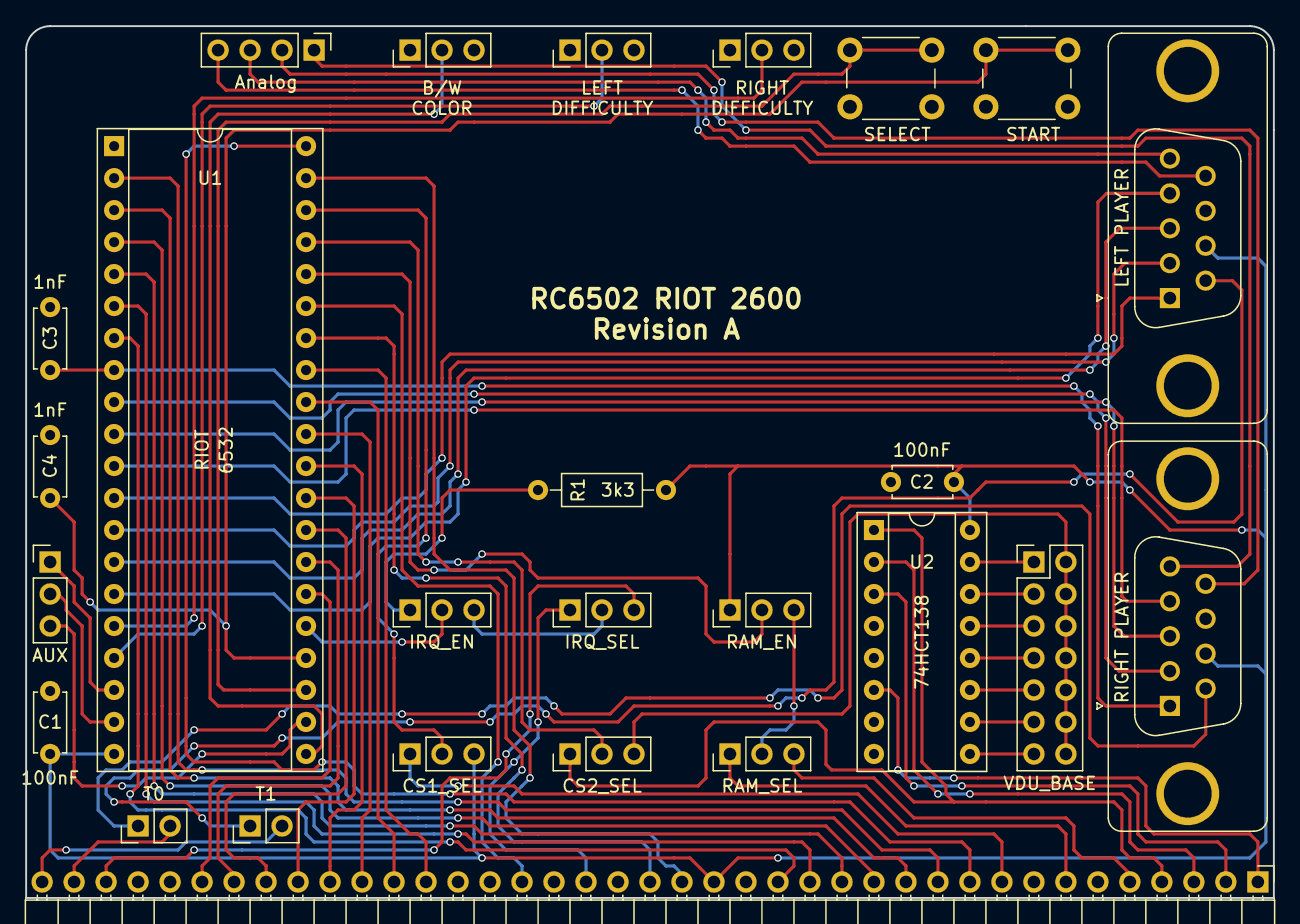
[picture p68: board RC6502 RIOT.kicad_pcb from above]

Board: 2 copper layers, 99.1 x 69.2 mm, 26 parts (0 on the bottom side), 68 nets.
