tebl/RC6502-Apple-1-Replica/RC6502 RAM/RC6502 RAM.kicad_pcb

## KiCad design RC6502 RAM/RC6502 RAM.kicad_pcb (2019-02-16)

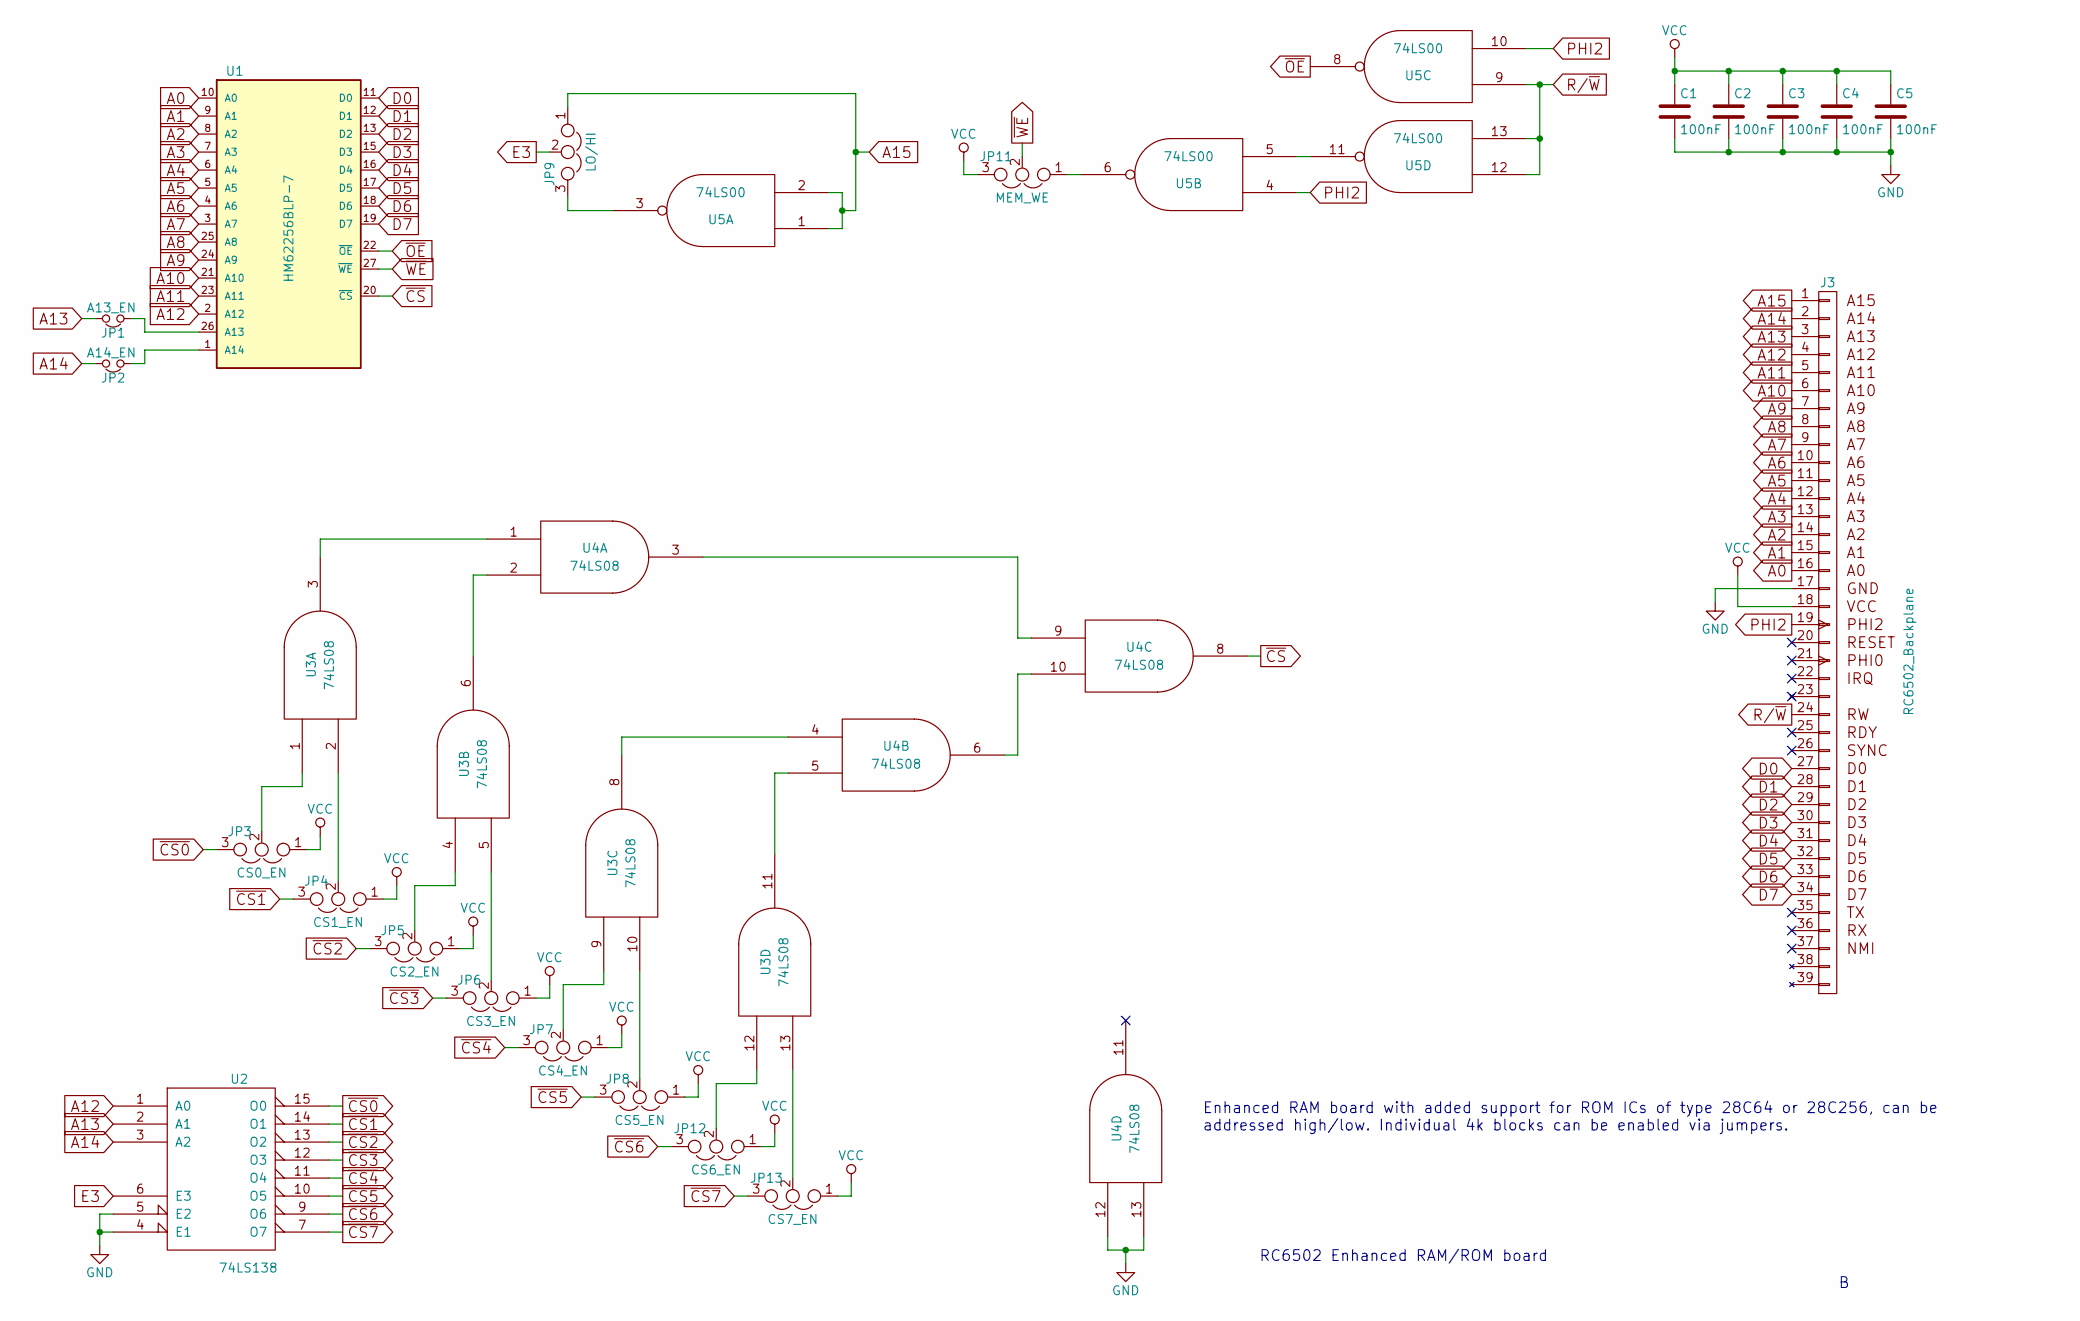
[picture p69: schematic RC6502 RAM.sch]

Parts:
C1, C2, C3, C4, C5: 100nF; C_Disc_D4.7mm_W2.5mm_P5.00mm
J3: RC6502_Backplane; Pin_Header_Angled_1x39_Pitch2.54mm
JP1: A13_EN; Pin_Header_Straight_1x02_Pitch2.54mm
JP2: A14_EN; Pin_Header_Straight_1x02_Pitch2.54mm
JP3: CS0_EN; Pin_Header_Straight_1x03_Pitch2.54mm
JP4: CS1_EN; Pin_Header_Straight_1x03_Pitch2.54mm
JP5: CS2_EN; Pin_Header_Straight_1x03_Pitch2.54mm
JP6: CS3_EN; Pin_Header_Straight_1x03_Pitch2.54mm
JP7: CS4_EN; Pin_Header_Straight_1x03_Pitch2.54mm
JP8: CS5_EN; Pin_Header_Straight_1x03_Pitch2.54mm
JP9: LO/HI; Pin_Header_Straight_1x03_Pitch2.54mm
JP11: MEM_WE; Pin_Header_Straight_1x03_Pitch2.54mm
JP12: CS6_EN; Pin_Header_Straight_1x03_Pitch2.54mm
JP13: CS7_EN; Pin_Header_Straight_1x03_Pitch2.54mm
U1: HM62256BLP-7; DIP-28_W15.24mm_Socket
U2: 74LS138; DIP-16_W7.62mm_Socket
U3, U4: 74LS08; DIP-14_W7.62mm_Socket
U5: 74LS00; DIP-14_W7.62mm_Socket

Connections:
A0: J3.16 (A0), U1.10 (A0)
A1: J3.15 (A1), U1.9 (A1)
A2: J3.14 (A2), U1.8 (A2)
A3: J3.13 (A3), U1.7 (A3)
A4: J3.12 (A4), U1.6 (A4)
A5: J3.11 (A5), U1.5 (A5)
A6: J3.10 (A6), U1.4 (A6)
A7: J3.9 (A7), U1.3 (A7)
A8: J3.8 (A8), U1.25 (A8)
A9: J3.7 (A9), U1.24 (A9)
A10: J3.6 (A10), U1.21 (A10)
A11: J3.5 (A11), U1.23 (A11)
A12: J3.4 (A12), U1.2 (A12), U2.1 (A0)
A13: J3.3 (A13), JP1.2, U2.2 (A1)
A14: J3.2 (A14), JP2.2, U2.3 (A2)
A15: J3.1 (A15), JP9.1, U5.1, U5.2
D0: J3.27 (D0), U1.11 (D0)
D1: J3.28 (D1), U1.12 (D1)
D2: J3.29 (D2), U1.13 (D2)
D3: J3.30 (D3), U1.15 (D3)
D4: J3.31 (D4), U1.16 (D4)
D5: J3.32 (D5), U1.17 (D5)
D6: J3.33 (D6), U1.18 (D6)
D7: J3.34 (D7), U1.19 (D7)
E3: JP9.2, U2.6 (E3)
GND: C1.2, C2.2, C3.2, C4.2, C5.2, J3.17, U1.14 (GND), U2.4 (E1), U2.5 (E2), U2.8 (GND), U3.7 (GND), U4.7 (GND), U4.12, U4.13, U5.7 (GND)
unnamed: JP1.1, U1.26 (A13)
unnamed: JP2.1, U1.1 (A14)
unnamed: JP3.2, U3.1
unnamed: JP4.2, U3.2
unnamed: JP5.2, U3.4
unnamed: JP6.2, U3.5
unnamed: JP7.2, U3.9
unnamed: JP8.2, U3.10
unnamed: JP9.3, U5.3
unnamed: JP11.1, U5.6
unnamed: JP12.2, U3.12
unnamed: JP13.2, U3.13
unnamed: U3.3, U4.1
unnamed: U3.6, U4.2
unnamed: U3.8, U4.4
unnamed: U3.11, U4.5
unnamed: U4.3, U4.9
unnamed: U4.6, U4.10
unnamed: U5.5, U5.11
PHI2: J3.19 (PHI2), U5.4, U5.10
R/~W: J3.24 (RW), U5.9, U5.12, U5.13
VCC: C1.1, C2.1, C3.1, C4.1, C5.1, J3.18, JP3.1, JP4.1, JP5.1, JP6.1, JP7.1, JP8.1, JP11.3, JP12.1, JP13.1, U1.28 (VCC), U2.16 (VCC), U3.14 (VCC), U4.14 (VCC), U5.14 (VCC)
~CS: U1.20 (~CS), U4.8
~CS0: JP3.3, U2.15 (O0)
~CS1: JP4.3, U2.14 (O1)
~CS2: JP5.3, U2.13 (O2)
~CS3: JP6.3, U2.12 (O3)
~CS4: JP7.3, U2.11 (O4)
~CS5: JP8.3, U2.10 (O5)
~CS6: JP12.3, U2.9 (O6)
~CS7: JP13.3, U2.7 (O7)
~OE: U1.22 (~OE), U5.8
~WE: JP11.2, U1.27 (~WE)

Notes on the sheet:
RC6502 Enhanced RAM/ROM board
Enhanced RAM board with added support for ROM ICs of type 28C64 or 28C256, can be addressed high/low. Individual 4k blocks can be enabled via jumpers.

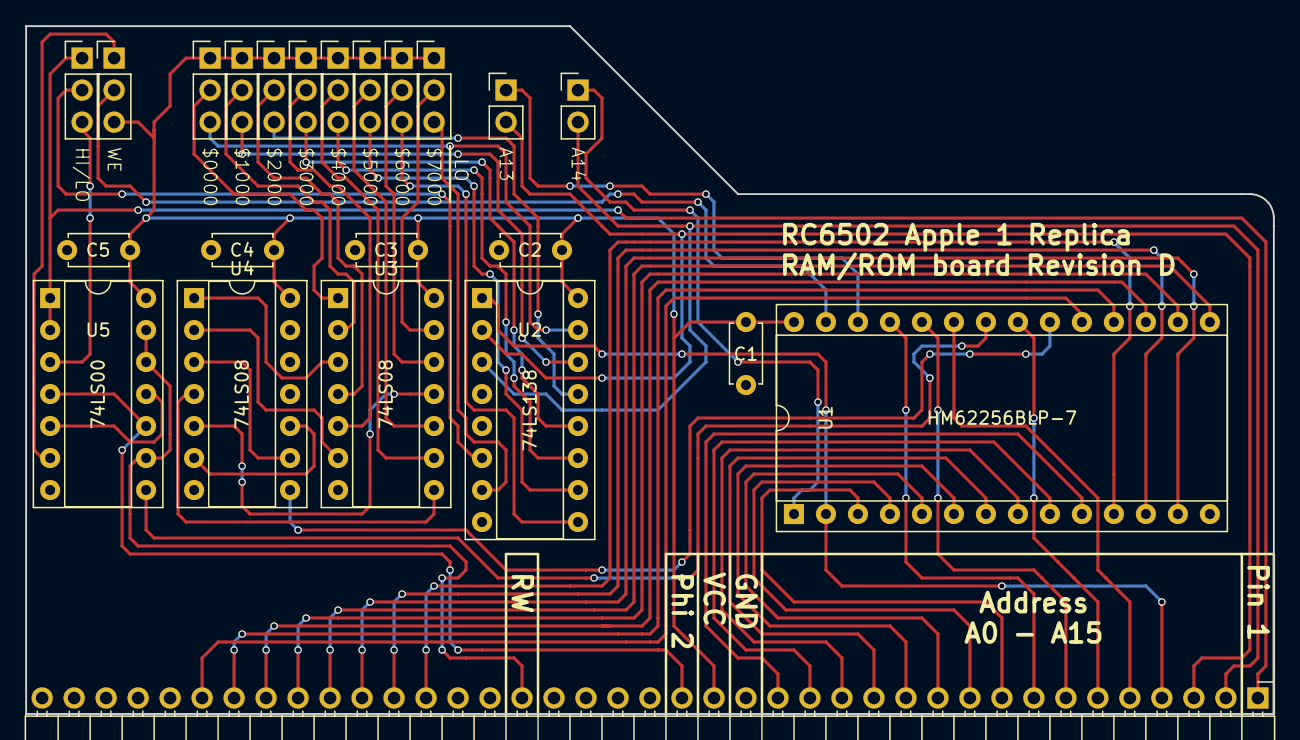
[picture p70: board RC6502 RAM.kicad_pcb from above]

Board: 2 copper layers, 99.1 x 54.6 mm, 23 parts (0 on the bottom side), 59 nets.
