tebl/RC6502-Apple-1-Replica/RC6502 TIA NTSC/RC6502 TIA NTSC.kicad_pcb

## KiCad design RC6502 TIA NTSC/RC6502 TIA NTSC.kicad_pcb (2019-02-14)

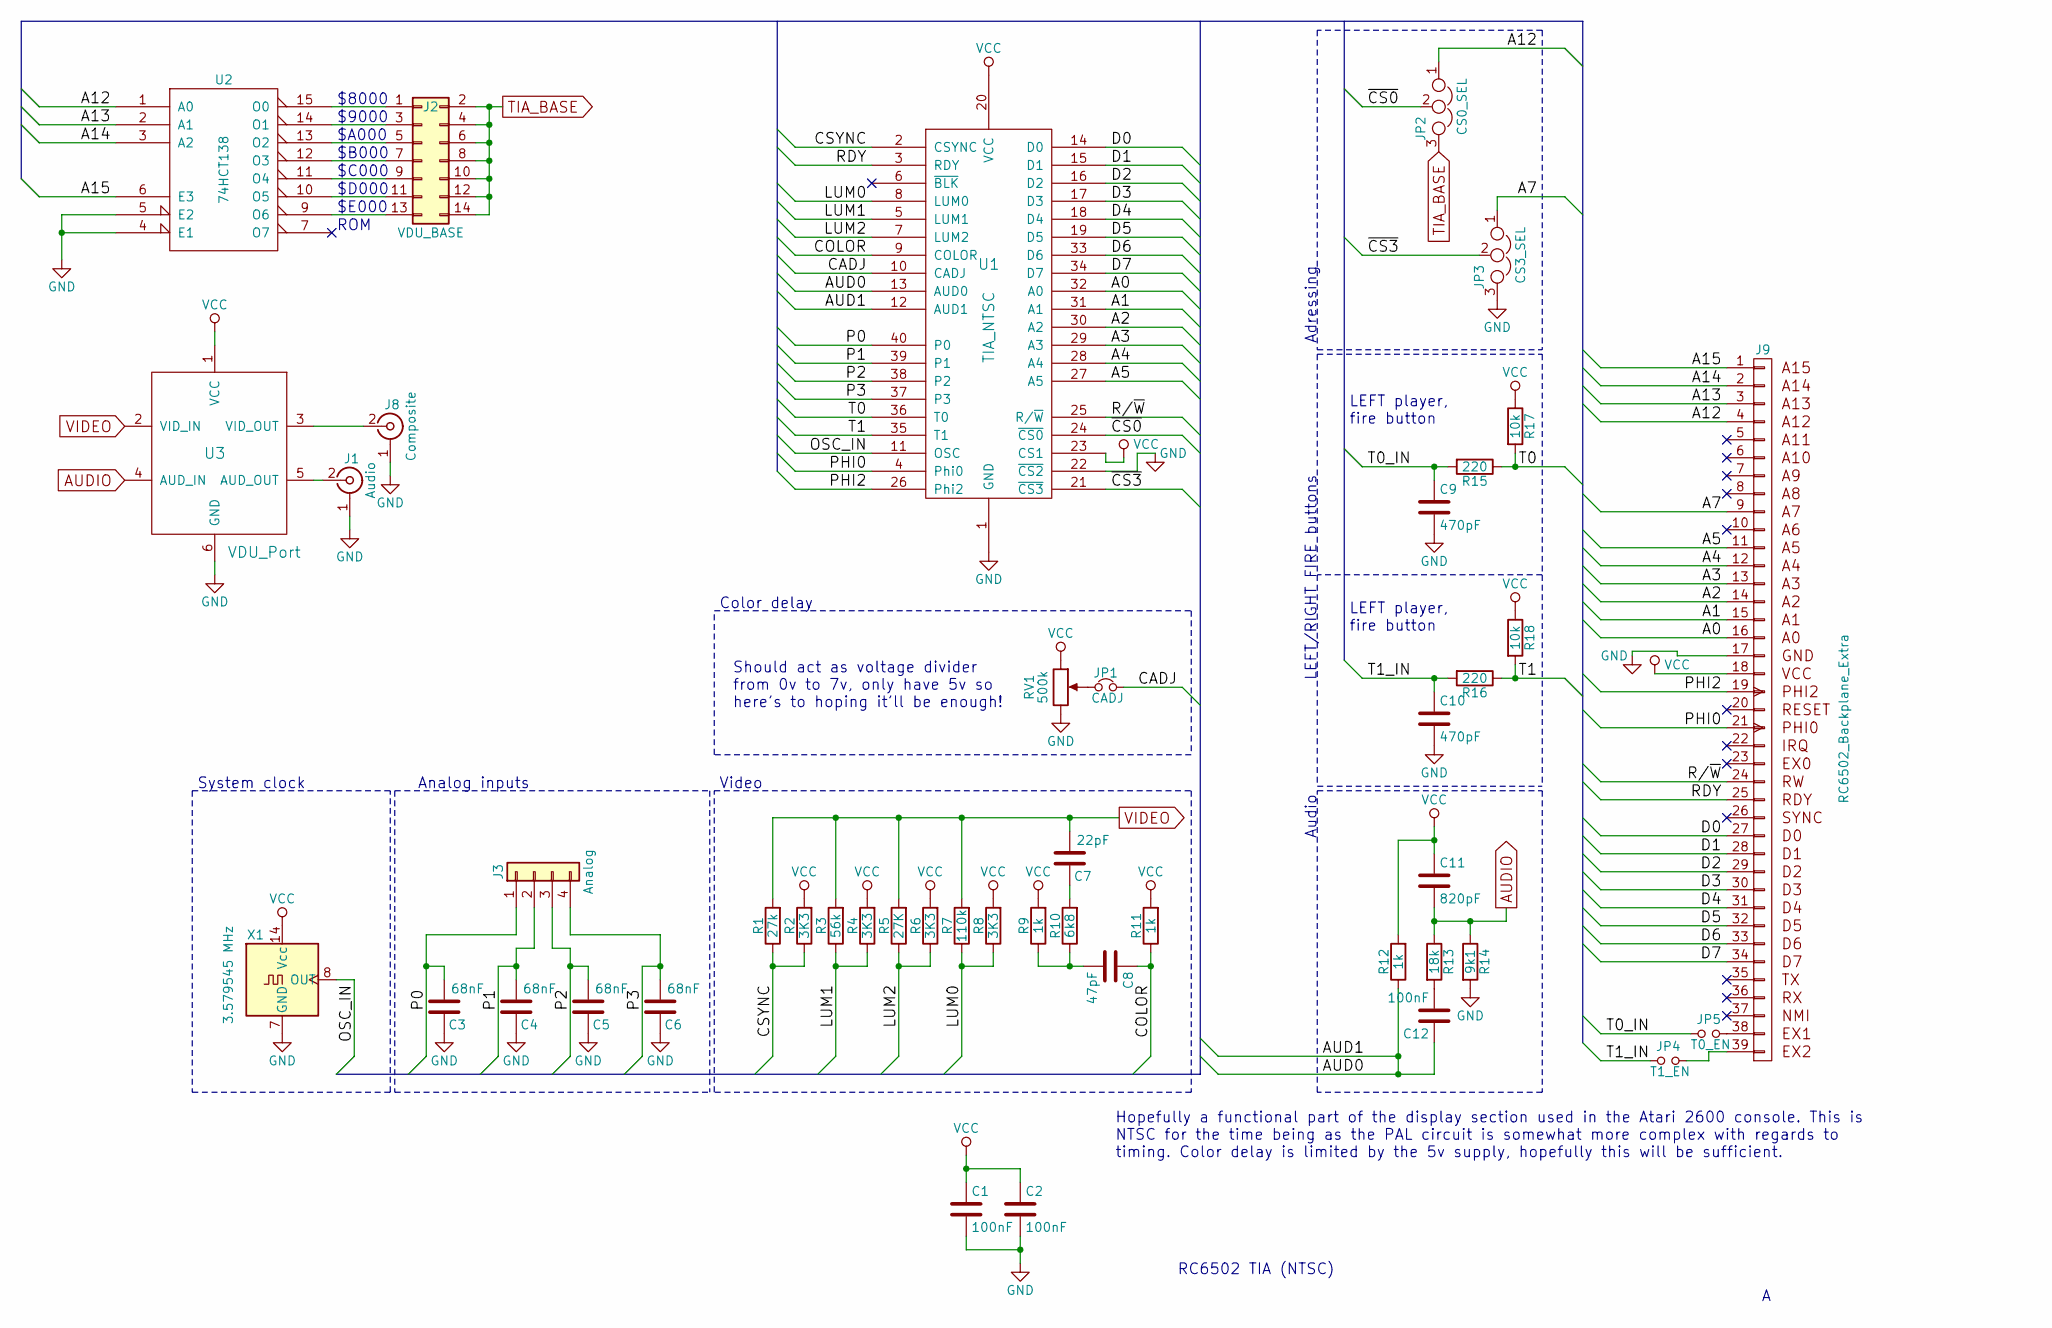
[picture p71: schematic RC6502 TIA NTSC.sch]

Parts:
C1, C2, C12: 100nF; C_Disc_D4.7mm_W2.5mm_P5.00mm
C3, C4, C5, C6: 68nF; C_Disc_D4.7mm_W2.5mm_P5.00mm
C7: 22pF; C_Disc_D4.7mm_W2.5mm_P5.00mm
C8: 47pF; C_Disc_D4.7mm_W2.5mm_P5.00mm
C9, C10: 470pF; C_Disc_D4.7mm_W2.5mm_P5.00mm
C11: 820pF; C_Disc_D4.7mm_W2.5mm_P5.00mm
J1: Audio; rca_yellow
J2: VDU_BASE; Pin_Header_Straight_2x07_Pitch2.54mm
J3: Analog; Pin_Header_Straight_1x04_Pitch2.54mm
J8: Composite; rca_yellow
J9: RC6502_Backplane_Extra; Pin_Header_Angled_1x39_Pitch2.54mm
JP1: CADJ; Pin_Header_Straight_1x02_Pitch2.54mm
JP2: CS0_SEL; Pin_Header_Straight_1x03_Pitch2.54mm
JP3: CS3_SEL; Pin_Header_Straight_1x03_Pitch2.54mm
JP4: T1_EN; Pin_Header_Straight_1x02_Pitch2.54mm
JP5: T0_EN; Pin_Header_Straight_1x02_Pitch2.54mm
R1: 27k; R_Axial_DIN0207_L6.3mm_D2.5mm_P10.16mm_Horizontal
R2, R4, R6, R8: 3K3; R_Axial_DIN0207_L6.3mm_D2.5mm_P10.16mm_Horizontal
R3: 56k; R_Axial_DIN0207_L6.3mm_D2.5mm_P10.16mm_Horizontal
R5: 27K; R_Axial_DIN0207_L6.3mm_D2.5mm_P10.16mm_Horizontal
R7: 110k; R_Axial_DIN0207_L6.3mm_D2.5mm_P10.16mm_Horizontal
R9, R11, R12: 1k; R_Axial_DIN0207_L6.3mm_D2.5mm_P10.16mm_Horizontal
R10: 6k8; R_Axial_DIN0207_L6.3mm_D2.5mm_P10.16mm_Horizontal
R13: 18k; R_Axial_DIN0207_L6.3mm_D2.5mm_P10.16mm_Horizontal
R14: 9k1; R_Axial_DIN0207_L6.3mm_D2.5mm_P10.16mm_Horizontal
R15, R16: 220; R_Axial_DIN0207_L6.3mm_D2.5mm_P10.16mm_Horizontal
R17, R18: 10k; R_Axial_DIN0207_L6.3mm_D2.5mm_P10.16mm_Horizontal
RV1: 500k; Potentiometer_Trimmer_Bourns_3296W
U1: TIA_NTSC; DIP-40_W15.24mm_Socket
U2: 74HCT138; DIP-16_W7.62mm_Socket
U3: VDU_Port; Amplifier
X1: 3.579545 MHz; Oscillator_DIP-14

Connections:
/A0: J9.16 (A0), U1.32 (A0)
/A1: J9.15 (A1), U1.31 (A1)
/A2: J9.14 (A2), U1.30 (A2)
/A3: J9.13 (A3), U1.29 (A3)
/A4: J9.12 (A4), U1.28 (A4)
/A5: J9.11 (A5), U1.27 (A5)
/A7: J9.9 (A7), JP3.1
/A12: J9.4 (A12), JP2.1, U2.1 (A0)
/A13: J9.3 (A13), U2.2 (A1)
/A14: J9.2 (A14), U2.3 (A2)
/A15: J9.1 (A15), U2.6 (E3)
/AUD0: C12.1, R12.1, U1.12 (AUD1), U1.13 (AUD0)
/CADJ: JP1.2, U1.10 (CADJ)
/COLOR: C8.1, R11.1, U1.9 (COLOR)
/CSYNC: R1.1, R2.1, U1.2 (CSYNC)
/D0: J9.27 (D0), U1.14 (D0)
/D1: J9.28 (D1), U1.15 (D1)
/D2: J9.29 (D2), U1.16 (D2)
/D3: J9.30 (D3), U1.17 (D3)
/D4: J9.31 (D4), U1.18 (D4)
/D5: J9.32 (D5), U1.19 (D5)
/D6: J9.33 (D6), U1.33 (D6)
/D7: J9.34 (D7), U1.34 (D7)
/LUM0: R7.1, R8.1, U1.8 (LUM0)
/LUM1: R3.1, R4.1, U1.5 (LUM1)
/LUM2: R5.1, R6.1, U1.7 (LUM2)
/OSC_IN: U1.11 (OSC), X1.8 (OUT)
/P0: C3.2, J3.1, U1.40 (P0)
/P1: C4.2, J3.2, U1.39 (P1)
/P2: C5.2, J3.3, U1.38 (P2)
/P3: C6.2, J3.4, U1.37 (P3)
/PHI0: J9.21 (PHI0), U1.4 (Phi0)
/PHI2: J9.19 (PHI2), U1.26 (Phi2)
/R/~W: J9.24 (RW), U1.25 (R/~W)
/RDY: J9.25 (READY), U1.3 (RDY)
/T0: R15.1, R17.2, U1.36 (T0)
/T0_IN: C9.1, JP5.1, R15.2
/T1: R16.1, R18.2, U1.35 (T1)
/T1_IN: C10.1, JP4.1, R16.2
/~CS0: JP2.2, U1.24 (~CS0)
/~CS3: JP3.2, U1.21 (~CS3)
AUDIO: C11.2, R13.1, R14.1, U3.4 (AUD_IN)
GND: C1.2, C2.2, C3.1, C4.1, C5.1, C6.1, C9.2, C10.2, J1.1 (Ext), J8.1 (Ext), J9.17, JP3.3, R14.2, RV1.3, U1.1 (GND), U1.22 (~CS2), U2.4 (E1), U2.5 (E2), U2.8 (GND), U3.6 (GND), X1.7 (GND)
unnamed: C7.1, R10.2
unnamed: C8.2, R9.1, R10.1
unnamed: C12.2, R13.2
unnamed: J1.2 (In), U3.5 (AUD_OUT)
unnamed: J2.1, U2.15 (O0)
unnamed: J2.3, U2.14 (O1)
unnamed: J2.5, U2.13 (O2)
unnamed: J2.7, U2.12 (O3)
unnamed: J2.9, U2.11 (O4)
unnamed: J2.11, U2.10 (O5)
unnamed: J2.13, U2.9 (O6)
unnamed: J8.2 (In), U3.3 (VID_OUT)
unnamed: J9.38 (EX1), JP5.2
unnamed: J9.39 (EX2), JP4.2
unnamed: JP1.1, RV1.2
TIA_BASE: J2.2, J2.4, J2.6, J2.8, J2.10, J2.12, J2.14, JP2.3
VCC: C1.1, C2.1, C11.1, J9.18, R2.2, R4.2, R6.2, R8.2, R9.2, R11.2, R12.2, R17.1, R18.1, RV1.1, U1.20 (VCC), U1.23 (CS1), U2.16 (VCC), U3.1 (VCC), X1.14 (Vcc)
VIDEO: C7.2, R1.2, R3.2, R5.2, R7.2, U3.2 (VID_IN)

Notes on the sheet:
RC6502 TIA (NTSC)
ROM
$C000
$B000
$A000
$9000
$8000
$D000
$E000
LEFT player, fire button
Video
Analog inputs
System clock
Audio
LEFT/RIGHT FIRE buttons
Adressing
Color delay
Should act as voltage divider from 0v to 7v, only have 5v so here's to hoping it'll be enough!
Hopefully a functional part of the display section used in the Atari 2600 console. This is NTSC for the time being as the PAL circuit is somewhat more complex with regards to timing. Color delay is limited by the 5v supply, hopefully this will be sufficient.

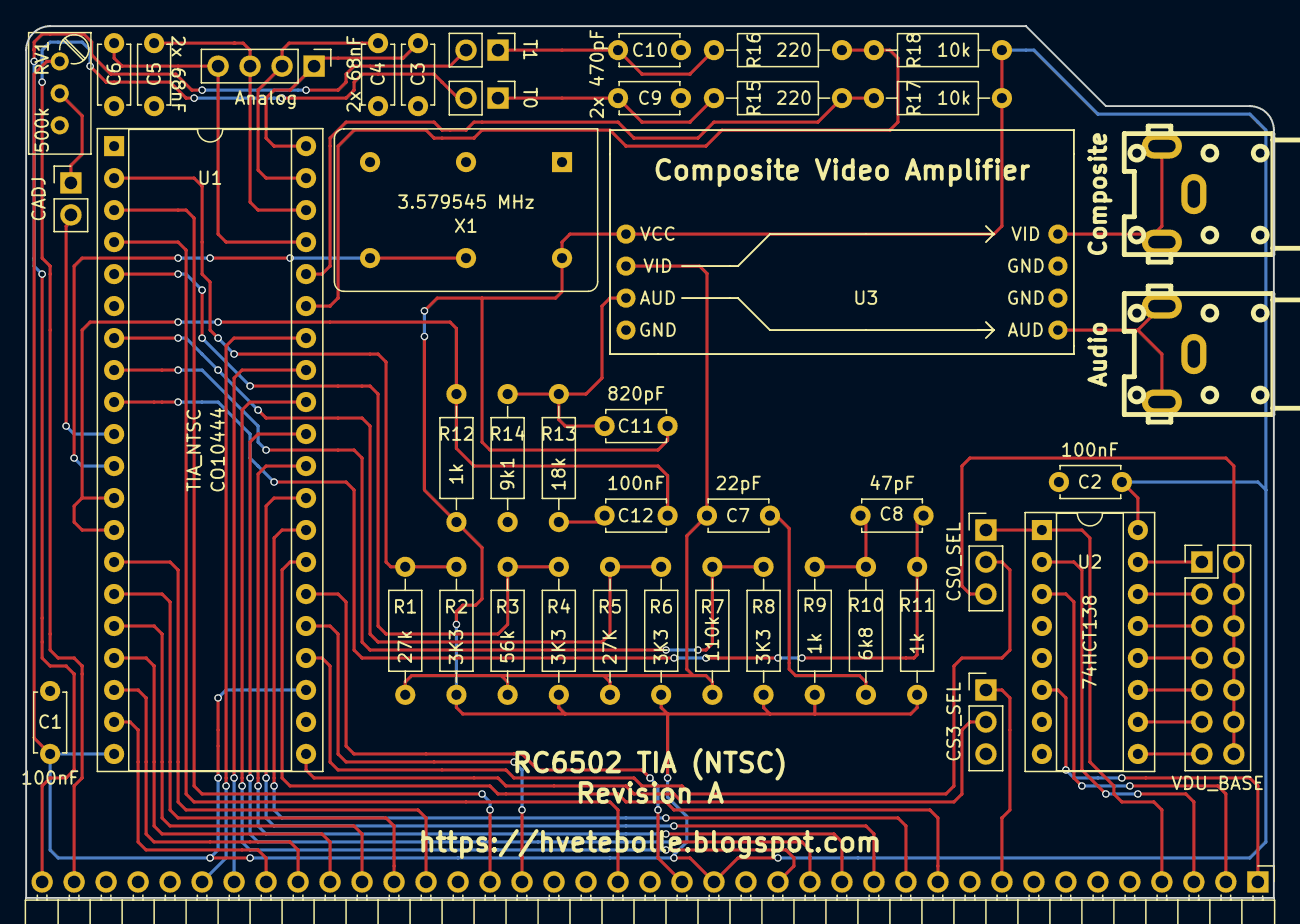
[picture p72: board RC6502 TIA NTSC.kicad_pcb from above]

Board: 2 copper layers, 99.1 x 69.2 mm, 45 parts (0 on the bottom side), 61 nets.
