tebl/RC6502-Apple-1-Replica/RC6502 Backplane/RC6502 Backplane.kicad_pcb

## KiCad design RC6502 Backplane/RC6502 Backplane.kicad_pcb (2019-02-11)

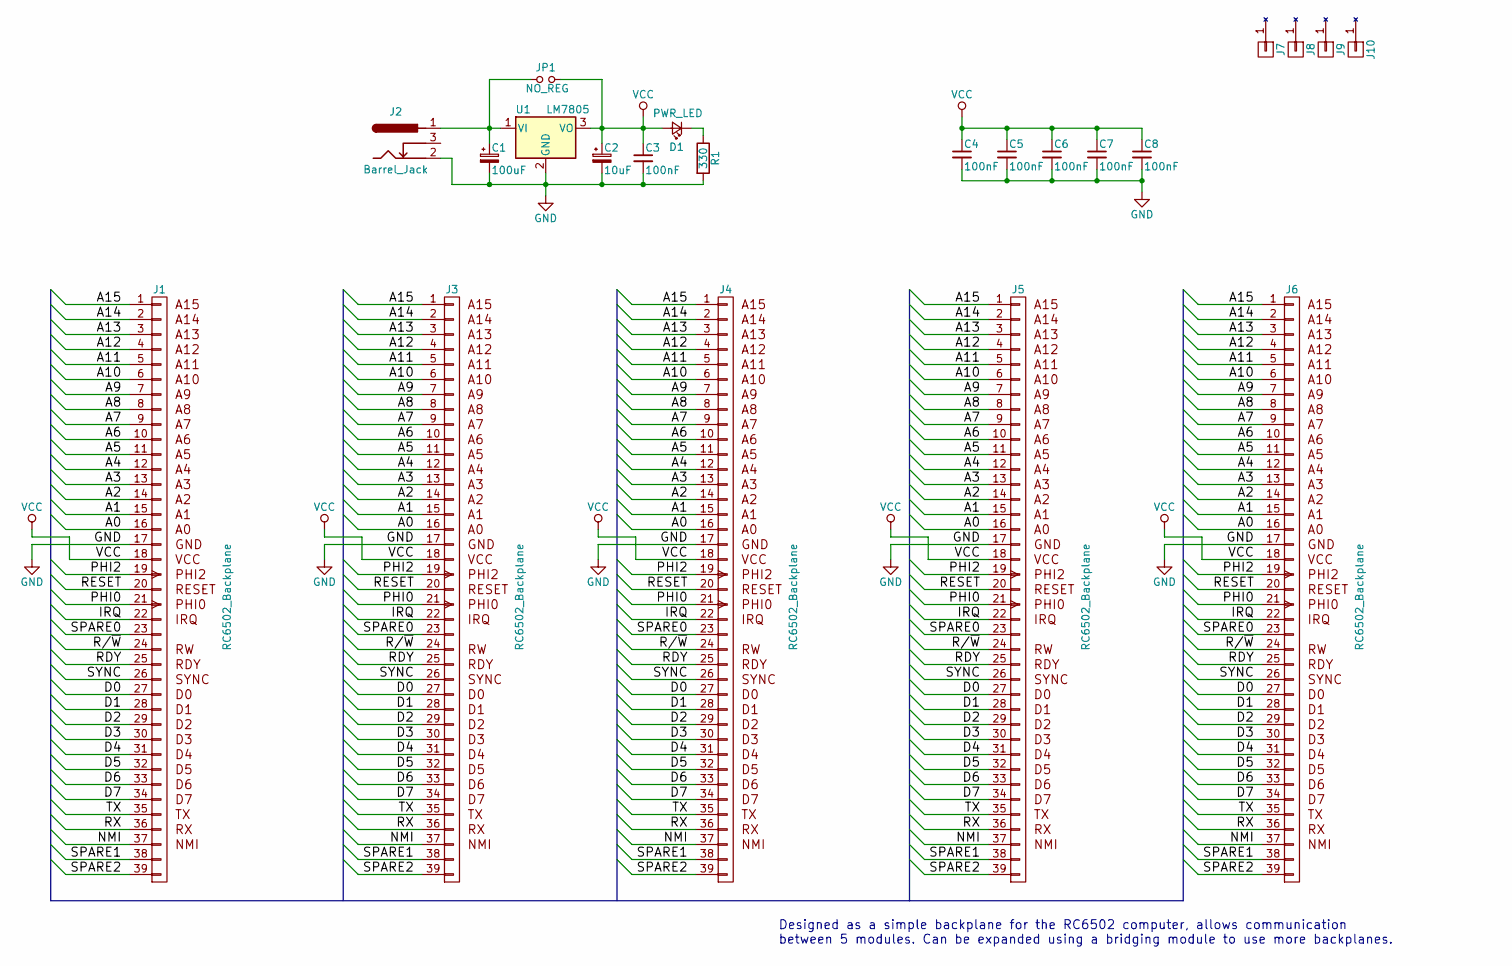
[picture p73: schematic RC6502 Backplane.sch]

Parts:
C1: 100uF; CP_Radial_D5.0mm_P2.50mm
C2: 10uF; CP_Radial_D4.0mm_P2.00mm
C3, C4, C5, C6, C7, C8: 100nF; C_Disc_D4.7mm_W2.5mm_P5.00mm
D1: PWR_LED; LED_D5.0mm
J1, J3, J4, J5, J6: RC6502_Backplane; Pin_Header_Straight_1x39_Pitch2.54mm
J2: Barrel_Jack; BARREL_JACK
J7, J8, J9, J10: Mounting
JP1: NO_REG; Pin_Header_Straight_1x02_Pitch2.54mm
R1: 330; R_Axial_DIN0207_L6.3mm_D2.5mm_P10.16mm_Horizontal
U1: LM7805; TO-220-3_Horizontal

Connections:
/A0: J1.16 (A0), J3.16 (A0), J4.16 (A0), J5.16 (A0), J6.16 (A0)
/A1: J1.15 (A1), J3.15 (A1), J4.15 (A1), J5.15 (A1), J6.15 (A1)
/A2: J1.14 (A2), J3.14 (A2), J4.14 (A2), J5.14 (A2), J6.14 (A2)
/A3: J1.13 (A3), J3.13 (A3), J4.13 (A3), J5.13 (A3), J6.13 (A3)
/A4: J1.12 (A4), J3.12 (A4), J4.12 (A4), J5.12 (A4), J6.12 (A4)
/A5: J1.11 (A5), J3.11 (A5), J4.11 (A5), J5.11 (A5), J6.11 (A5)
/A6: J1.10 (A6), J3.10 (A6), J4.10 (A6), J5.10 (A6), J6.10 (A6)
/A7: J1.9 (A7), J3.9 (A7), J4.9 (A7), J5.9 (A7), J6.9 (A7)
/A8: J1.8 (A8), J3.8 (A8), J4.8 (A8), J5.8 (A8), J6.8 (A8)
/A9: J1.7 (A9), J3.7 (A9), J4.7 (A9), J5.7 (A9), J6.7 (A9)
/A10: J1.6 (A10), J3.6 (A10), J4.6 (A10), J5.6 (A10), J6.6 (A10)
/A11: J1.5 (A11), J3.5 (A11), J4.5 (A11), J5.5 (A11), J6.5 (A11)
/A12: J1.4 (A12), J3.4 (A12), J4.4 (A12), J5.4 (A12), J6.4 (A12)
/A13: J1.3 (A13), J3.3 (A13), J4.3 (A13), J5.3 (A13), J6.3 (A13)
/A14: J1.2 (A14), J3.2 (A14), J4.2 (A14), J5.2 (A14), J6.2 (A14)
/A15: J1.1 (A15), J3.1 (A15), J4.1 (A15), J5.1 (A15), J6.1 (A15)
/D0: J1.27 (D0), J3.27 (D0), J4.27 (D0), J5.27 (D0), J6.27 (D0)
/D1: J1.28 (D1), J3.28 (D1), J4.28 (D1), J5.28 (D1), J6.28 (D1)
/D2: J1.29 (D2), J3.29 (D2), J4.29 (D2), J5.29 (D2), J6.29 (D2)
/D3: J1.30 (D3), J3.30 (D3), J4.30 (D3), J5.30 (D3), J6.30 (D3)
/D4: J1.31 (D4), J3.31 (D4), J4.31 (D4), J5.31 (D4), J6.31 (D4)
/D5: J1.32 (D5), J3.32 (D5), J4.32 (D5), J5.32 (D5), J6.32 (D5)
/D6: J1.33 (D6), J3.33 (D6), J4.33 (D6), J5.33 (D6), J6.33 (D6)
/D7: J1.34 (D7), J3.34 (D7), J4.34 (D7), J5.34 (D7), J6.34 (D7)
/IRQ: J1.22 (IRQ), J3.22 (IRQ), J4.22 (IRQ), J5.22 (IRQ), J6.22 (IRQ)
/NMI: J1.37 (NMI), J3.37 (NMI), J4.37 (NMI), J5.37 (NMI), J6.37 (NMI)
/PHI0: J1.21 (PHI0), J3.21 (PHI0), J4.21 (PHI0), J5.21 (PHI0), J6.21 (PHI0)
/PHI2: J1.19 (PHI2), J3.19 (PHI2), J4.19 (PHI2), J5.19 (PHI2), J6.19 (PHI2)
/R/~W: J1.24 (RW), J3.24 (RW), J4.24 (RW), J5.24 (RW), J6.24 (RW)
/RDY: J1.25 (READY), J3.25 (READY), J4.25 (READY), J5.25 (READY), J6.25 (READY)
/RESET: J1.20 (RESET), J3.20 (RESET), J4.20 (RESET), J5.20 (RESET), J6.20 (RESET)
/RX: J1.36 (RX), J3.36 (RX), J4.36 (RX), J5.36 (RX), J6.36 (RX)
/SPARE0: J1.23, J3.23, J4.23, J5.23, J6.23
/SPARE1: J1.38, J3.38, J4.38, J5.38, J6.38
/SPARE2: J1.39, J3.39, J4.39, J5.39, J6.39
/SYNC: J1.26 (SYNC), J3.26 (SYNC), J4.26 (SYNC), J5.26 (SYNC), J6.26 (SYNC)
/TX: J1.35 (TX), J3.35 (TX), J4.35 (TX), J5.35 (TX), J6.35 (TX)
GND: C1.2, C2.2, C3.2, C4.2, C5.2, C6.2, C7.2, C8.2, J1.17, J2.2, J3.17, J4.17, J5.17, J6.17, R1.2, U1.2 (GND)
unnamed: C1.1, J2.1, JP1.1, U1.1 (VI)
unnamed: D1.1 (K), R1.1
VCC: C2.1, C3.1, C4.1, C5.1, C6.1, C7.1, C8.1, D1.2 (A), J1.18, J3.18, J4.18, J5.18, J6.18, JP1.2, U1.3 (VO)

Notes on the sheet:
Designed as a simple backplane for the RC6502 computer, allows communication between 5 modules. Can be expanded using a bridging module to use more backplanes.

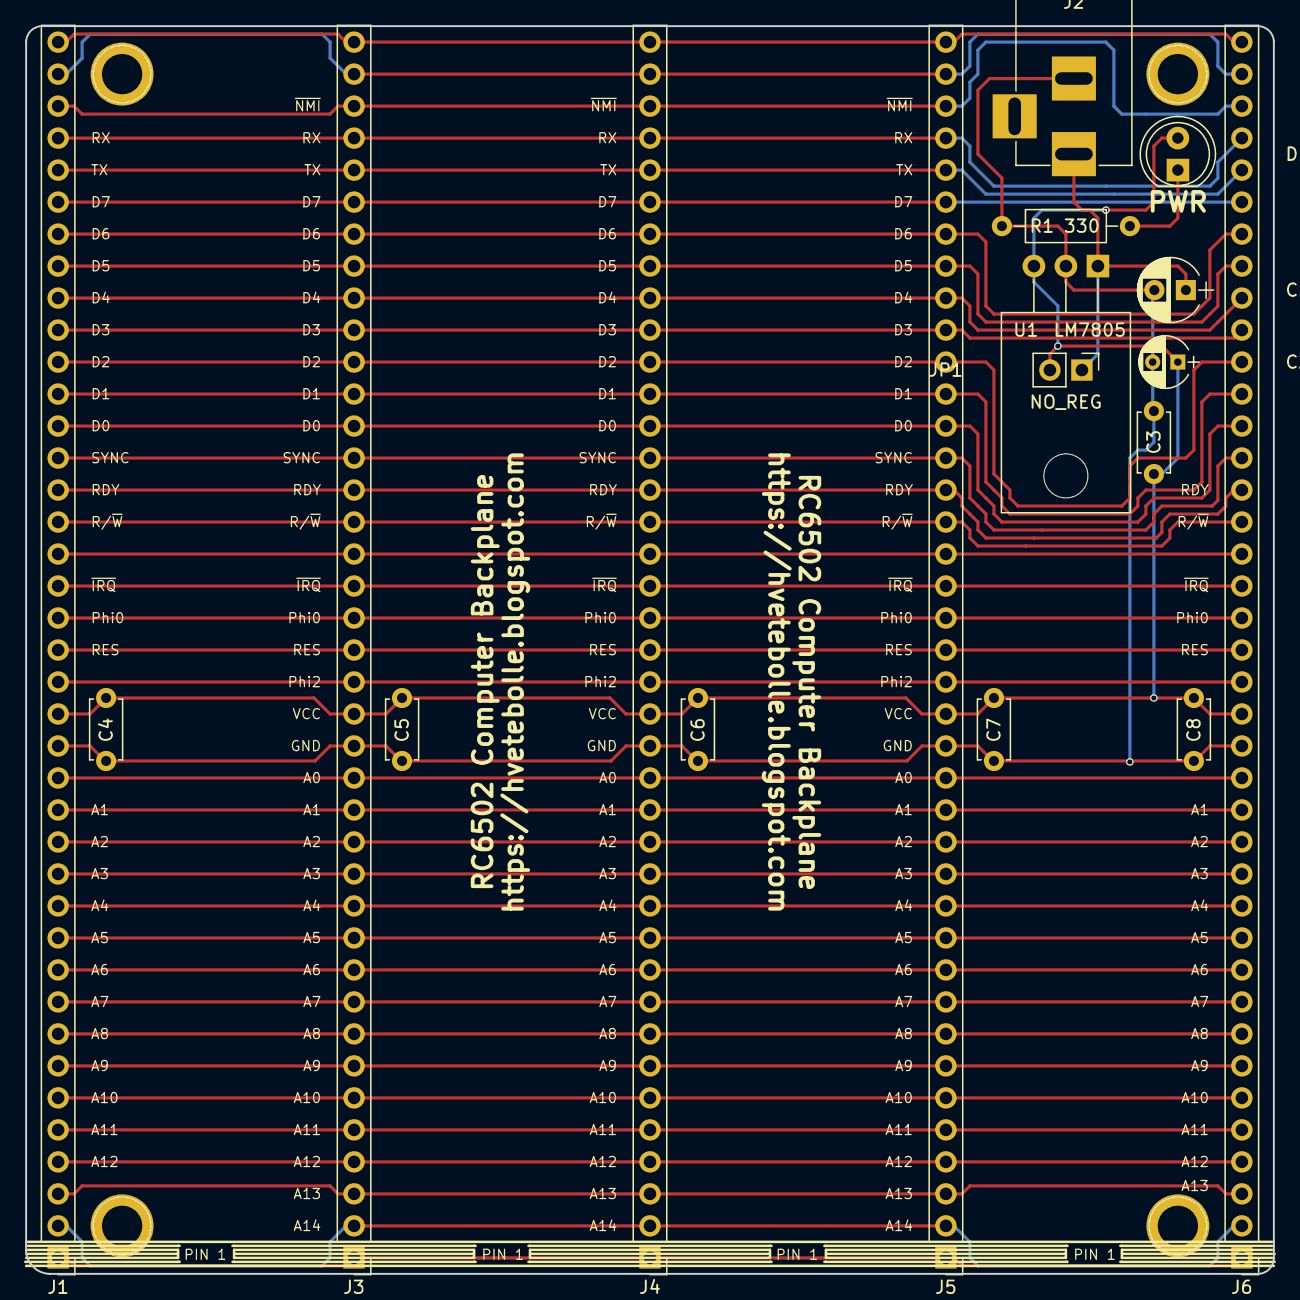
[picture p74: board RC6502 Backplane.kicad_pcb from above]

Board: 2 copper layers, 99.1 x 99.1 mm, 22 parts (0 on the bottom side), 41 nets.
