tebl/RC6502-Apple-1-Replica/RC6502 Prototyping/RC6502 Prototyping.kicad_pcb

## KiCad design RC6502 Prototyping/RC6502 Prototyping.kicad_pcb (2019-02-09)

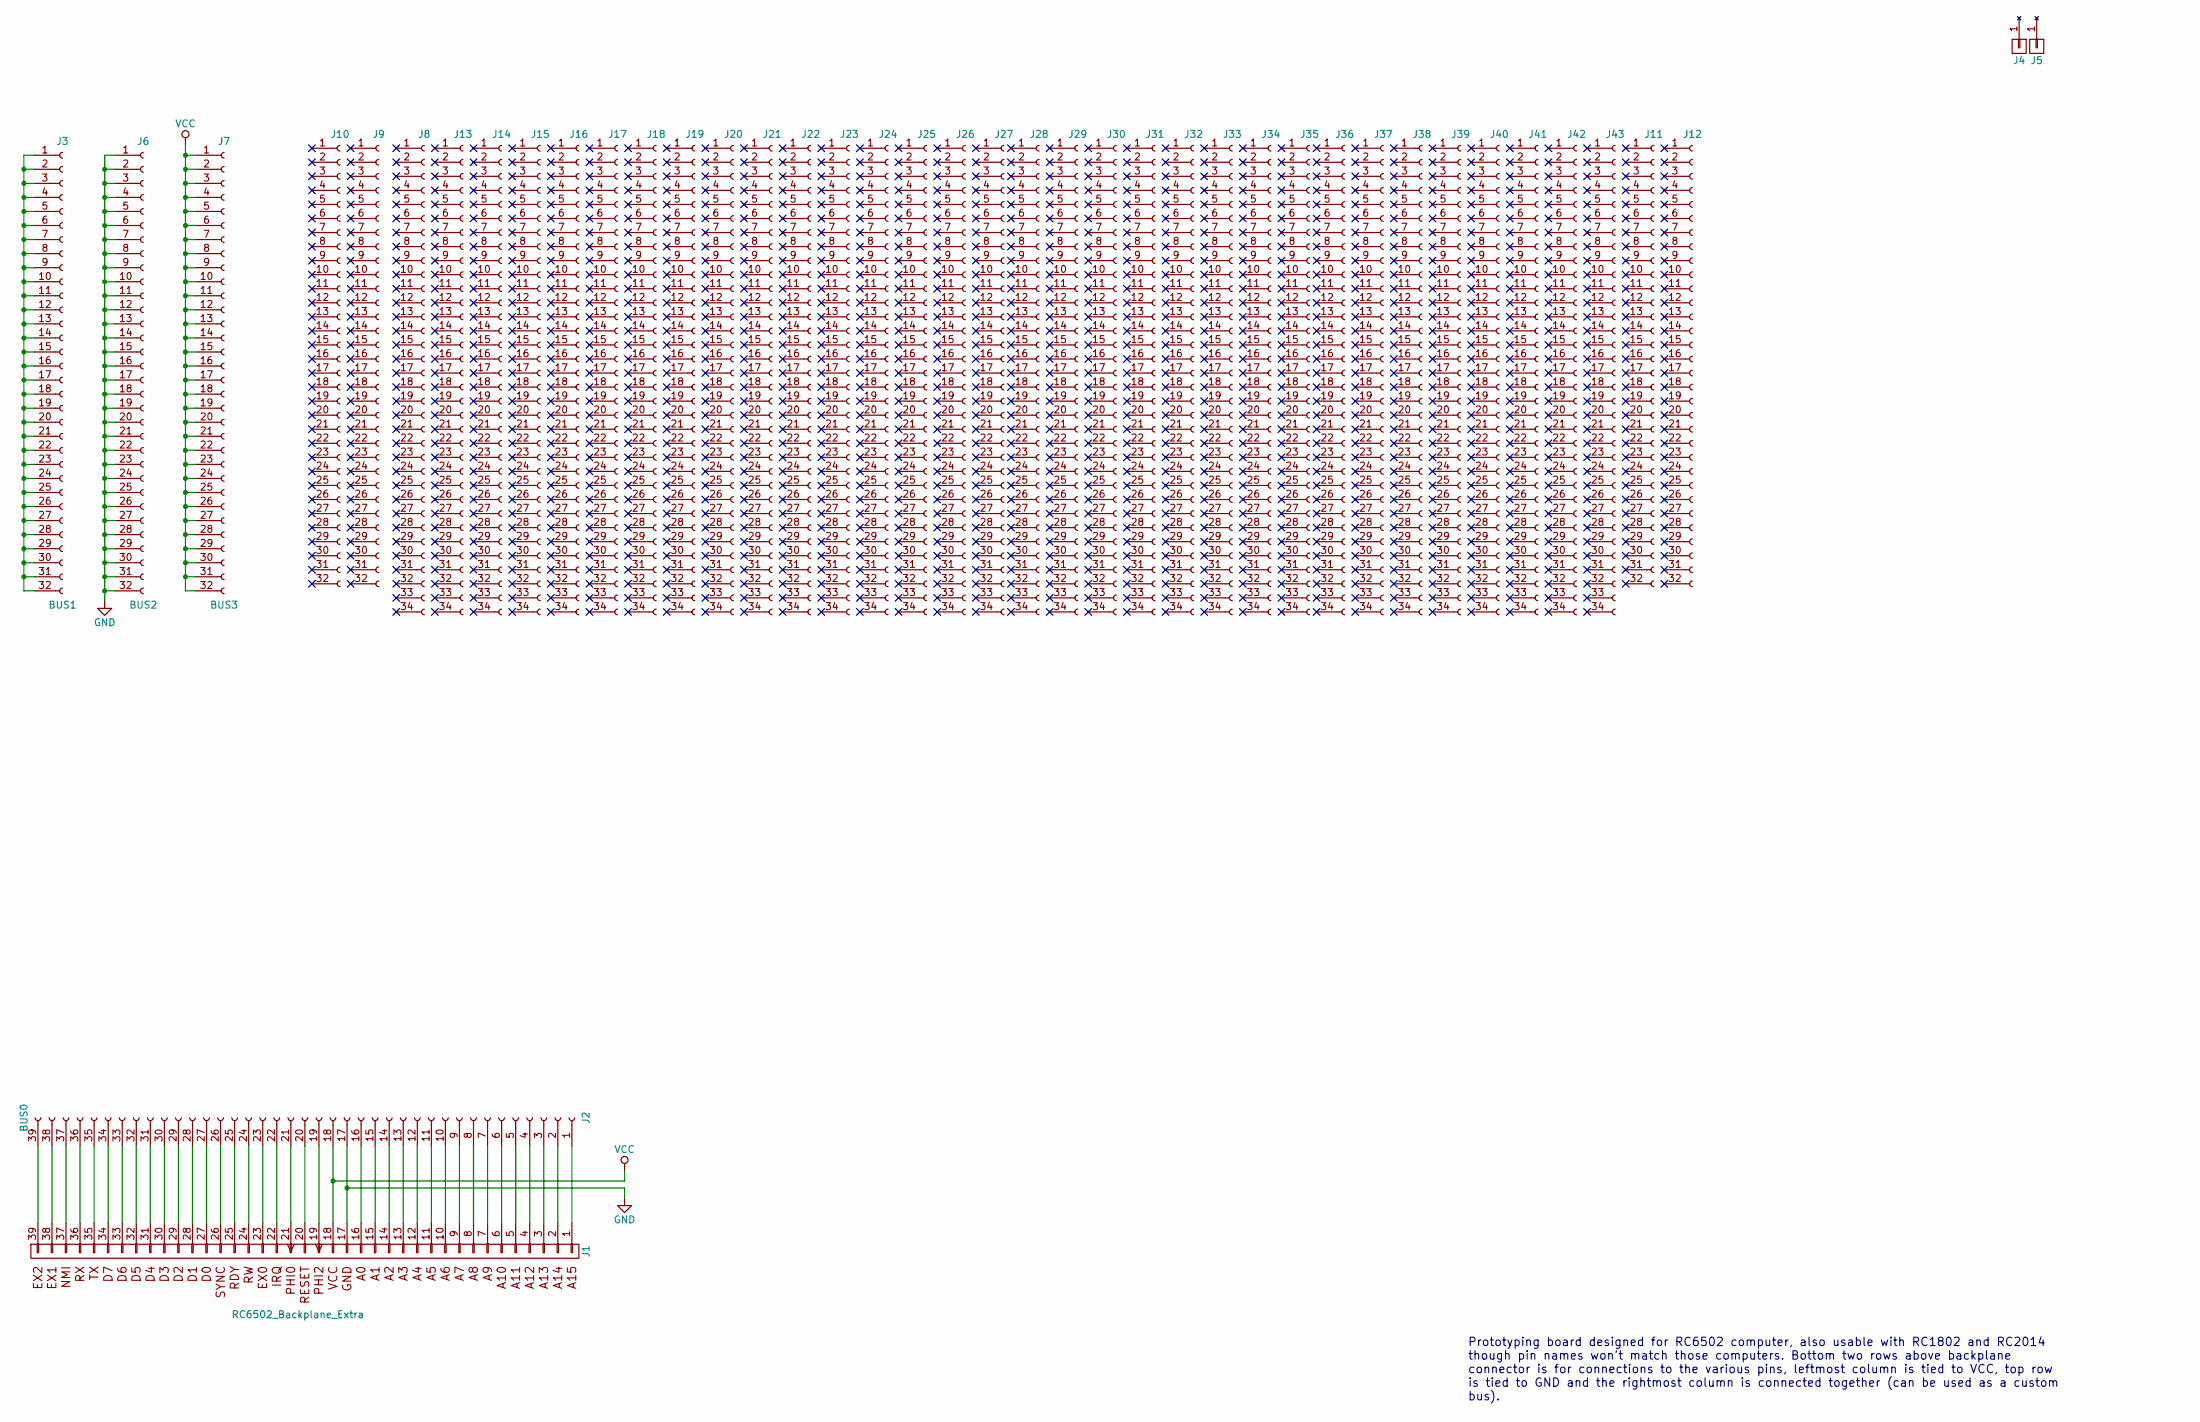
[picture p75: schematic RC6502 Prototyping.sch]

Parts:
J1: RC6502_Backplane_Extra; Pin_Header_Angled_1x39_Pitch2.54mm
J2: BUS0; Bus
J3: BUS1; Pin_Header_Straight_1x32_Pitch2.54mm
J4, J5: Mounting
J6: BUS2; Pin_Header_Straight_1x32_Pitch2.54mm
J7: BUS3; Pin_Header_Straight_1x32_Pitch2.54mm
J8, J13, J14, J15, J16, J17, J18, J19, J20, J21, J22, J23, J24, J25, J26, J27, J28, J29, J30, J31, J32, J33, J34, J35, J36, J37, J38, J39, J40, J41, J42, J43: Conn_01x34_Female; 34
J9, J10, J11, J12: Conn_01x32_Female; 32

Connections:
GND: J1.17, J2.17, J6.1, J6.2, J6.3, J6.4, J6.5, J6.6, J6.7, J6.8, J6.9, J6.10, J6.11, J6.12, J6.13, J6.14, J6.15, J6.16, J6.17, J6.18, J6.19, J6.20, J6.21, J6.22, J6.23, J6.24, J6.25, J6.26, J6.27, J6.28, J6.29, J6.30, J6.31, J6.32
unnamed: J1.1 (A15), J2.1
unnamed: J1.2 (A14), J2.2
unnamed: J1.3 (A13), J2.3
unnamed: J1.4 (A12), J2.4
unnamed: J1.5 (A11), J2.5
unnamed: J1.6 (A10), J2.6
unnamed: J1.7 (A9), J2.7
unnamed: J1.8 (A8), J2.8
unnamed: J1.9 (A7), J2.9
unnamed: J1.10 (A6), J2.10
unnamed: J1.11 (A5), J2.11
unnamed: J1.12 (A4), J2.12
unnamed: J1.13 (A3), J2.13
unnamed: J1.14 (A2), J2.14
unnamed: J1.15 (A1), J2.15
unnamed: J1.16 (A0), J2.16
unnamed: J1.19 (PHI2), J2.19
unnamed: J1.20 (RESET), J2.20
unnamed: J1.21 (PHI0), J2.21
unnamed: J1.22 (IRQ), J2.22
unnamed: J1.23 (EX0), J2.23
unnamed: J1.24 (RW), J2.24
unnamed: J1.25 (READY), J2.25
unnamed: J1.26 (SYNC), J2.26
unnamed: J1.27 (D0), J2.27
unnamed: J1.28 (D1), J2.28
unnamed: J1.29 (D2), J2.29
unnamed: J1.30 (D3), J2.30
unnamed: J1.31 (D4), J2.31
unnamed: J1.32 (D5), J2.32
unnamed: J1.33 (D6), J2.33
unnamed: J1.34 (D7), J2.34
unnamed: J1.35 (TX), J2.35
unnamed: J1.36 (RX), J2.36
unnamed: J1.37 (NMI), J2.37
unnamed: J1.38 (EX1), J2.38
unnamed: J1.39 (EX2), J2.39
unnamed: J3.1, J3.2, J3.3, J3.4, J3.5, J3.6, J3.7, J3.8, J3.9, J3.10, J3.11, J3.12, J3.13, J3.14, J3.15, J3.16, J3.17, J3.18, J3.19, J3.20, J3.21, J3.22, J3.23, J3.24, J3.25, J3.26, J3.27, J3.28, J3.29, J3.30, J3.31, J3.32
VCC: J1.18, J2.18, J7.1, J7.2, J7.3, J7.4, J7.5, J7.6, J7.7, J7.8, J7.9, J7.10, J7.11, J7.12, J7.13, J7.14, J7.15, J7.16, J7.17, J7.18, J7.19, J7.20, J7.21, J7.22, J7.23, J7.24, J7.25, J7.26, J7.27, J7.28, J7.29, J7.30, J7.31, J7.32

Notes on the sheet:
Prototyping board designed for RC6502 computer, also usable with RC1802 and RC2014 though pin names won't match those computers. Bottom two rows above backplane connector is for connections to the various pins, leftmost column is tied to VCC, top row is tied to GND and the rightmost column is conne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

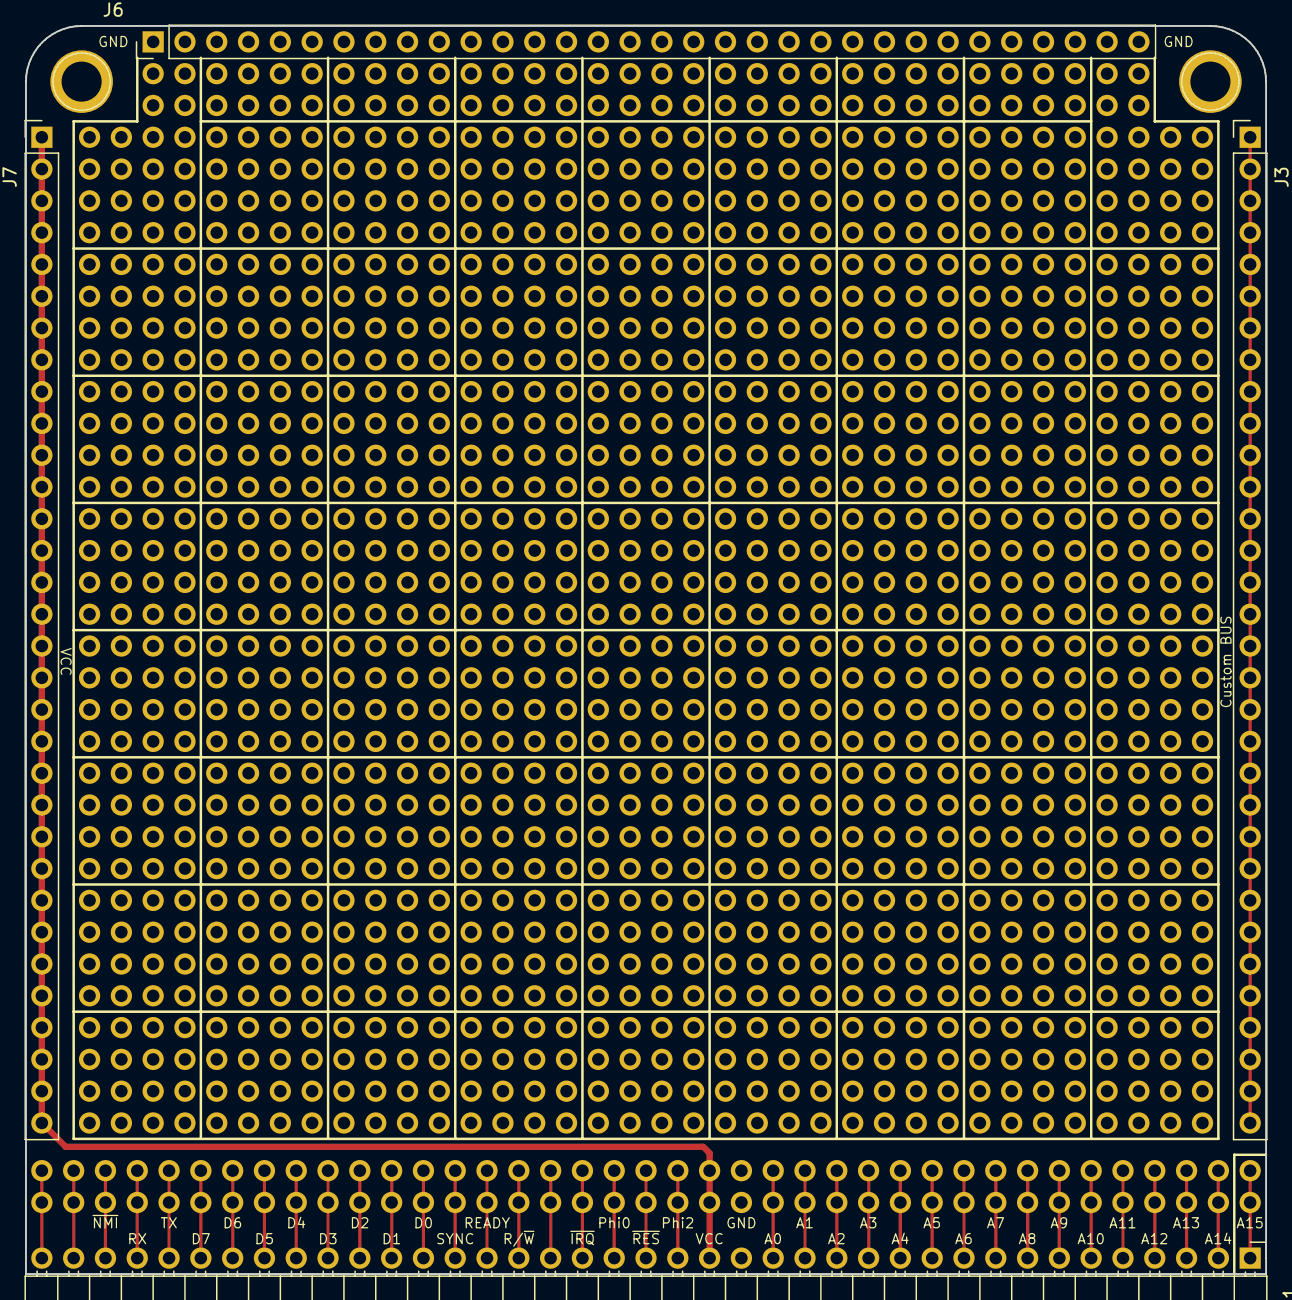
[picture p76: board RC6502 Prototyping.kicad_pcb from above]

Board: 2 copper layers, 99.1 x 99.7 mm, 43 parts (0 on the bottom side), 40 nets.
