tebl/RC6502-Apple-1-Replica/RC6502 VDU Amplifier/RC6502 VDU Amplifier.kicad_pcb

## KiCad design RC6502 VDU Amplifier/RC6502 VDU Amplifier.kicad_pcb (2019-01-12)

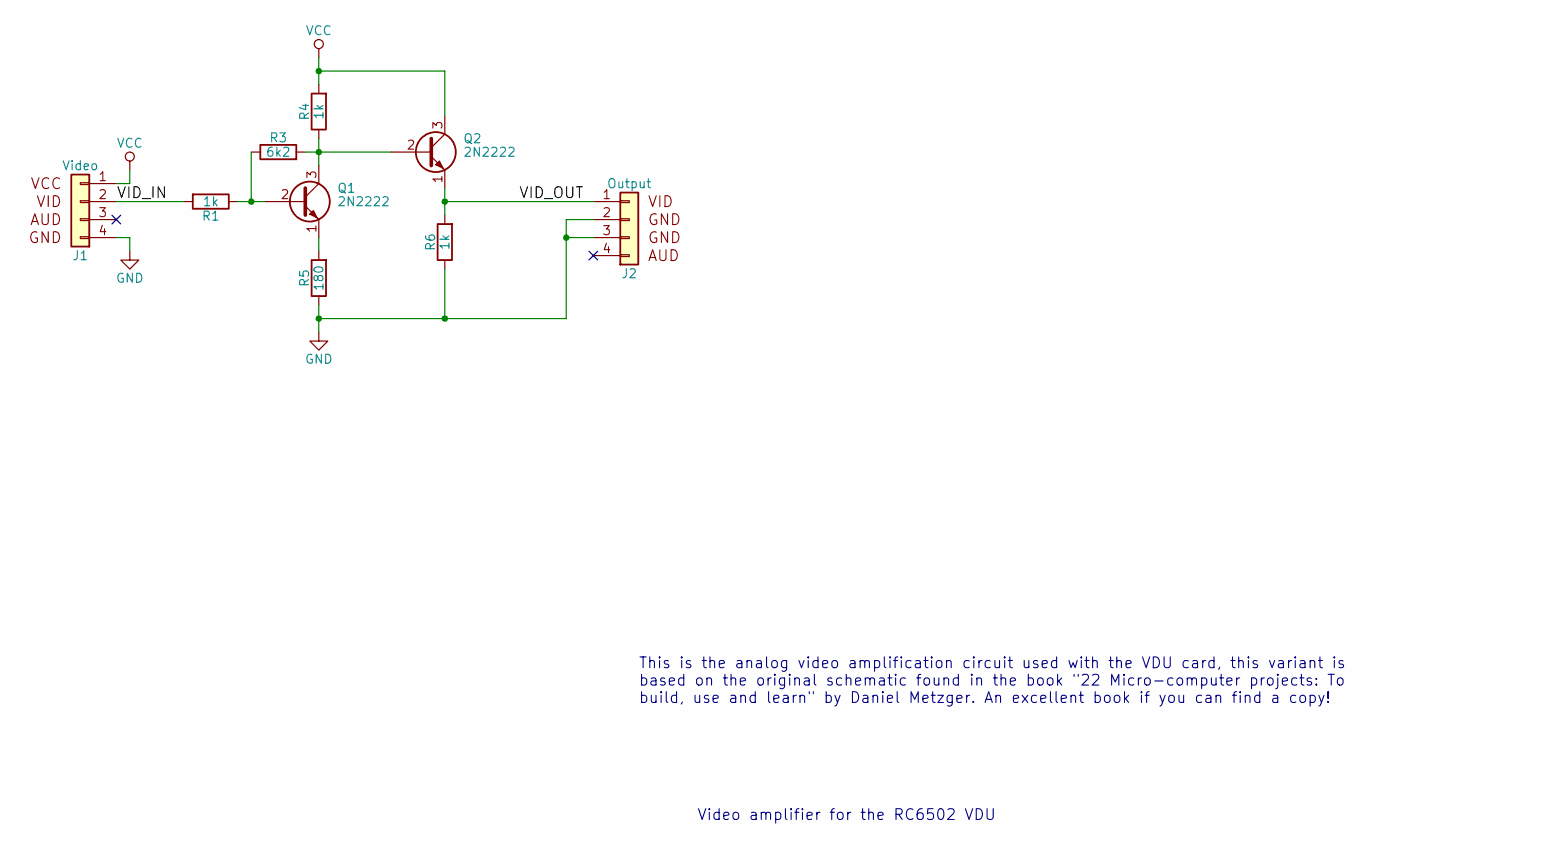
[picture p77: schematic RC6502 VDU Amplifier.sch]

Parts:
J1: Video; Pin_Header_Straight_1x04_Pitch2.54mm
J2: Output; Pin_Header_Straight_1x04_Pitch2.54mm
Q1, Q2: 2N2222; TO-92_Inline_Wide
R1, R4, R6: 1k; R_Axial_DIN0207_L6.3mm_D2.5mm_P10.16mm_Horizontal
R3: 6k2; R_Axial_DIN0207_L6.3mm_D2.5mm_P10.16mm_Horizontal
R5: 180; R_Axial_DIN0207_L6.3mm_D2.5mm_P10.16mm_Horizontal

Connections:
/VID_IN: J1.2 (Pin_3), R1.2
/VID_OUT: J2.1 (Pin_4), Q2.1 (E), R6.2
GND: J1.4 (Pin_1), J2.2 (Pin_3), J2.3 (Pin_2), R5.1, R6.1
unnamed: Q1.1 (E), R5.2
unnamed: Q1.2 (B), R1.1, R3.1
unnamed: Q1.3 (C), Q2.2 (B), R3.2, R4.1
VCC: J1.1 (Pin_4), Q2.3 (C), R4.2

Notes on the sheet:
This is the analog video amplification circuit used with the VDU card, this variant is based on the original schematic found in the book "22 Micro-computer projects: To build, use and learn" by Daniel Metzger. An excellent book if you can find a copy!
Video amplifier for the RC6502 VDU

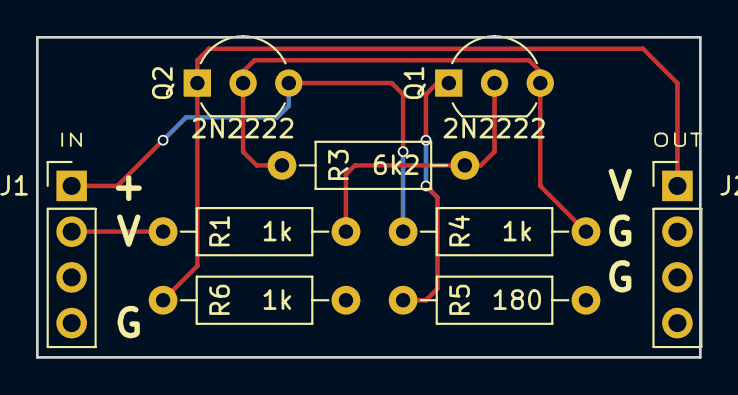
[picture p78: board RC6502 VDU Amplifier.kicad_pcb from above]

Board: 2 copper layers, 36.8 x 17.8 mm, 9 parts (0 on the bottom side), 7 nets.
