tebl/RC6502-Apple-1-Replica/Abandoned/RC6502 ATTiny Clock/ATTiny Clock.kicad_pcb

## KiCad design Abandoned/RC6502 ATTiny Clock/ATTiny Clock.kicad_pcb (2017-05-14)

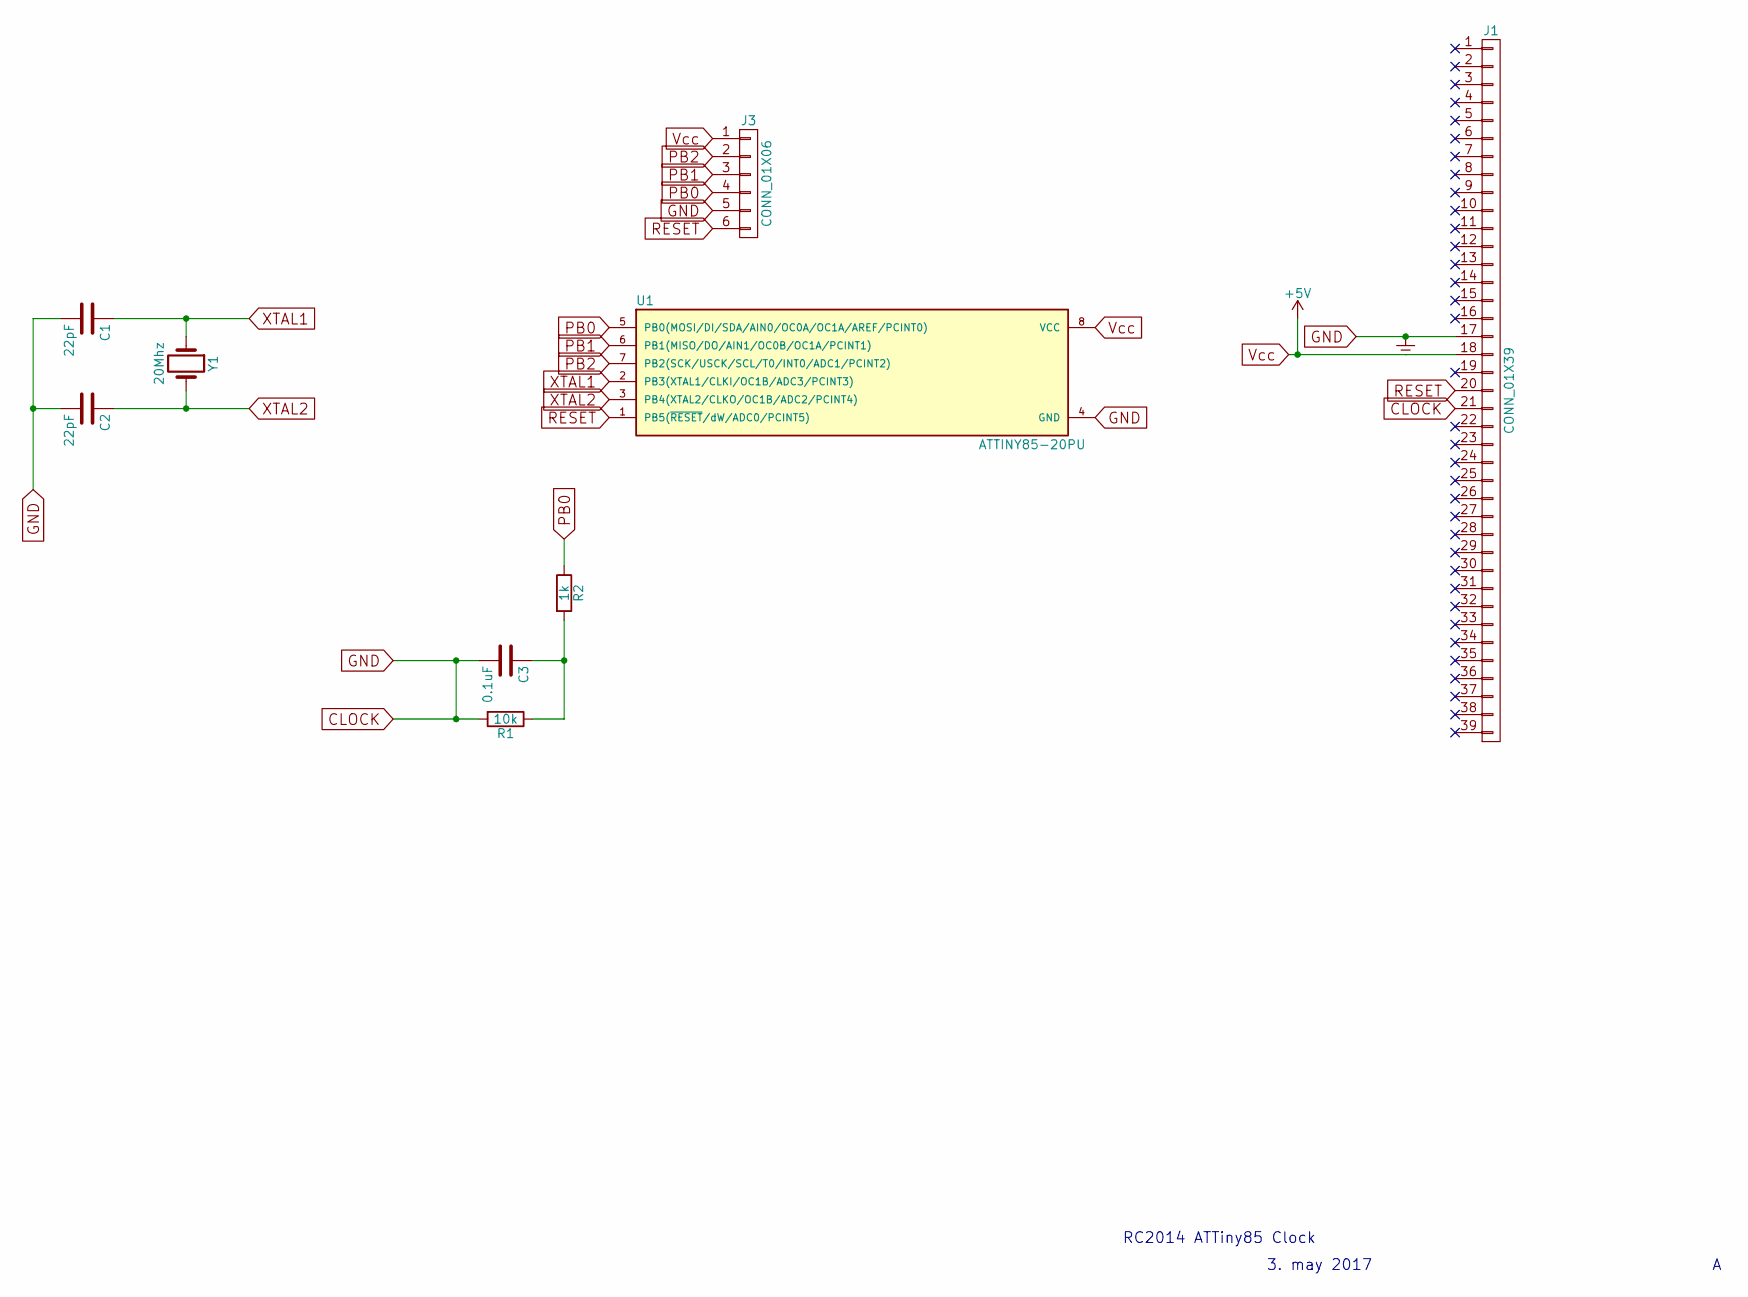
[picture p79: schematic ATTiny Clock.sch]

Parts:
C1, C2: 22pF; C_Disc_D4.7mm_W2.5mm_P5.00mm
C3: 0.1uF; C_Disc_D4.7mm_W2.5mm_P5.00mm
J1: CONN_01X39; Pin_Header_Angled_1x39_Pitch2.54mm
J3: CONN_01X06; Pin_Header_Angled_1x06_Pitch2.54mm
R1: 10k; R_Axial_DIN0207_L6.3mm_D2.5mm_P10.16mm_Horizontal
R2: 1k; R_Axial_DIN0207_L6.3mm_D2.5mm_P10.16mm_Horizontal
U1: ATTINY85-20PU; DIP-8_W7.62mm_Socket
Y1: 20Mhz; Crystal_HC49-4H_Vertical

Connections:
CLOCK: C1.2, C2.2, C3.2, J1.17, J1.21, J3.5, R1.2, U1.4 (GND)
unnamed: C3.1, R1.1, R2.2
PB0: J3.4, R2.1, U1.5 (PB0(MOSI/DI/SDA/AIN0/OC0A/OC1A/AREF/PCI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)
PB1: J3.3, U1.6 (PB1(MISO/DO/AIN1/OC0B/OC1A/PCINT1))
PB2: J3.2, U1.7 (PB2(SCK/USCK/SCL/T0/INT0/ADC1/PCINT2))
RESET: J1.20, J3.6, U1.1 (PB5(~RESET~/dW/ADC0/PCINT5))
Vcc: J1.18, J3.1, U1.8 (VCC)
XTAL1: C1.1, U1.2 (PB3(XTAL1/CLKI/OC1B/ADC3/PCINT3)), Y1.1
XTAL2: C2.1, U1.3 (PB4(XTAL2/CLKO/OC1B/ADC2/PCINT4)), Y1.2

Notes on the sheet:
RC2014 ATTiny85 Clock
3. may 2017

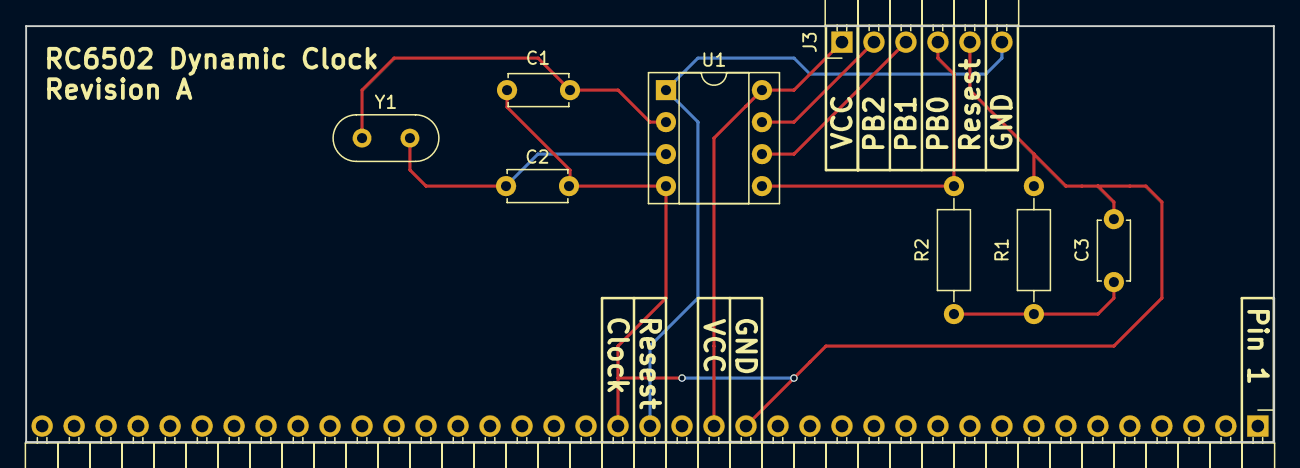
[picture p80: board ATTiny Clock.kicad_pcb from above]

Board: 2 copper layers, 99.1 x 33.0 mm, 9 parts (0 on the bottom side), 9 nets.
