tebl/RC6502-Apple-1-Replica/Abandoned/RC6502 Video Adapter/RC6502 Video Adapter.kicad_pcb

## KiCad design Abandoned/RC6502 Video Adapter/RC6502 Video Adapter.kicad_pcb (2017-06-15)

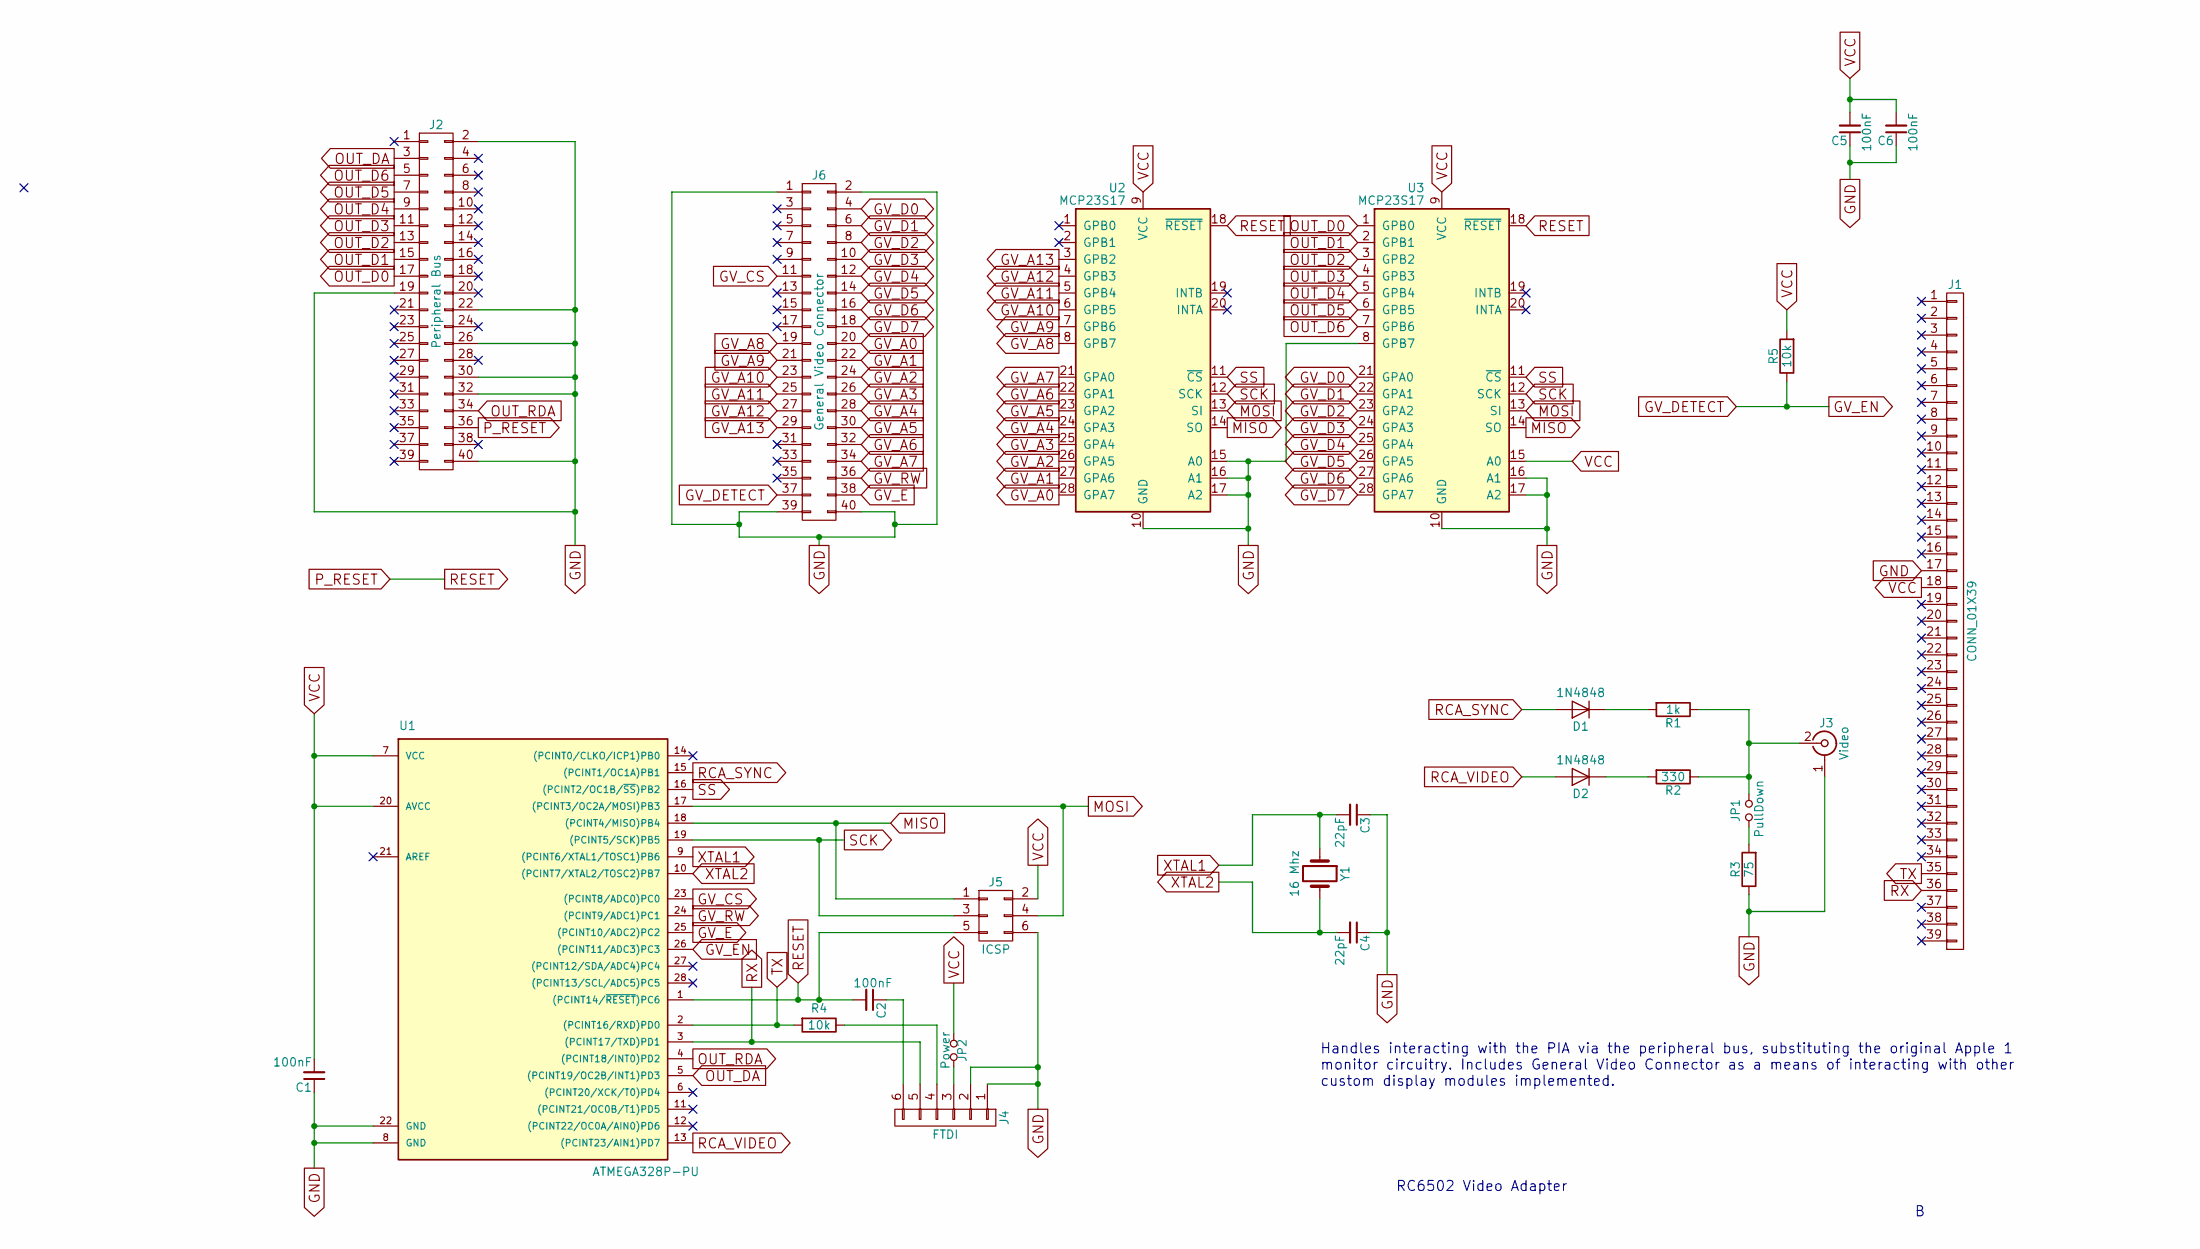
[picture p81: schematic RC6502 Video Adapter.sch]

Parts:
C1, C2, C5, C6: 100nF; C_Disc_D4.7mm_W2.5mm_P5.00mm
C3, C4: 22pF; C_Disc_D4.7mm_W2.5mm_P5.00mm
D1, D2: 1N4848; D_DO-35_SOD27_P7.62mm_Horizontal
J1: CONN_01X39; Pin_Header_Angled_1x39_Pitch2.54mm
J2: Peripheral Bus; IDC_Header_Straight_40pins
J3: Video; rca_yellow
J4: FTDI; Pin_Header_Angled_1x06_Pitch2.54mm
J5: ICSP; Pin_Header_Straight_2x03_Pitch2.54mm
J6: General Video Connector; IDC_Header_Straight_40pins
JP1: PullDown; Pin_Header_Straight_1x02_Pitch2.54mm
JP2: Power; Pin_Header_Angled_1x02_Pitch2.54mm
R1: 1k; R_Axial_DIN0207_L6.3mm_D2.5mm_P10.16mm_Horizontal
R2: 330; R_Axial_DIN0207_L6.3mm_D2.5mm_P10.16mm_Horizontal
R3: 75; R_Axial_DIN0207_L6.3mm_D2.5mm_P10.16mm_Horizontal
R4, R5: 10k; R_Axial_DIN0207_L6.3mm_D2.5mm_P10.16mm_Horizontal
U1: ATMEGA328P-PU; DIP-28_W7.62mm_Socket
U2, U3: MCP23S17; DIP-28_W7.62mm_Socket
Y1: 16 Mhz; Crystal_HC49-4H_Vertical

Connections:
GND: C1.1, C3.1, C4.1, C5.1, C6.1, J1.17, J2.2, J2.19, J2.22, J2.26, J2.30, J2.32, J2.40, J3.1 (Ext), J4.1, J4.2, J5.6, J6.1, J6.2, J6.39, J6.40, R3.1, U1.8 (GND), U1.22 (GND), U2.10 (GND), U2.15 (A0), U2.16 (A1), U2.17 (A2), U3.8 (GPB7), U3.10 (GND), U3.16 (A1), U3.17 (A2)
GV_A0: J6.20, U2.28 (GPA7)
GV_A1: J6.22, U2.27 (GPA6)
GV_A2: J6.24, U2.26 (GPA5)
GV_A3: J6.26, U2.25 (GPA4)
GV_A4: J6.28, U2.24 (GPA3)
GV_A5: J6.30, U2.23 (GPA2)
GV_A6: J6.32, U2.22 (GPA1)
GV_A7: J6.34, U2.21 (GPA0)
GV_A8: J6.19, U2.8 (GPB7)
GV_A9: J6.21, U2.7 (GPB6)
GV_A10: J6.23, U2.6 (GPB5)
GV_A11: J6.25, U2.5 (GPB4)
GV_A12: J6.27, U2.4 (GPB3)
GV_A13: J6.29, U2.3 (GPB2)
GV_CS: J6.11, U1.23 ((PCINT8/ADC0)PC0)
GV_D0: J6.4, U3.21 (GPA0)
GV_D1: J6.6, U3.22 (GPA1)
GV_D2: J6.8, U3.23 (GPA2)
GV_D3: J6.10, U3.24 (GPA3)
GV_D4: J6.12, U3.25 (GPA4)
GV_D5: J6.14, U3.26 (GPA5)
GV_D6: J6.16, U3.27 (GPA6)
GV_D7: J6.18, U3.28 (GPA7)
GV_DETECT: J6.37, R5.1, U1.26 ((PCINT11/ADC3)PC3)
GV_E: J6.38, U1.25 ((PCINT10/ADC2)PC2)
GV_RW: J6.36, U1.24 ((PCINT9/ADC1)PC1)
MISO: J5.1, U1.18 ((PCINT4/MISO)PB4), U2.14 (SO), U3.14 (SO)
MOSI: J5.4, U1.17 ((PCINT3/OC2A/MOSI)PB3), U2.13 (SI), U3.13 (SI)
unnamed: C2.1, J4.6
unnamed: D1.1 (K), R1.2
unnamed: D2.1 (K), R2.2
unnamed: J3.2 (In), JP1.2, R1.1, R2.1
unnamed: J4.3, JP2.2
unnamed: J4.4, R4.1
unnamed: JP1.1, R3.2
OUT_D0: J2.17, U3.1 (GPB0)
OUT_D1: J2.15, U3.2 (GPB1)
OUT_D2: J2.13, U3.3 (GPB2)
OUT_D3: J2.11, U3.4 (GPB3)
OUT_D4: J2.9, U3.5 (GPB4)
OUT_D5: J2.7, U3.6 (GPB5)
OUT_D6: J2.5, U3.7 (GPB6)
OUT_DA: J2.3, U1.5 ((PCINT19/OC2B/INT1)PD3)
OUT_RDA: J2.34, U1.4 ((PCINT18/INT0)PD2)
P_RESET: C2.2, J2.36, J5.5, U1.1 ((PCINT14/~RESET~)PC6), U2.18 (~RESET), U3.18 (~RESET)
RCA_SYNC: D1.2 (A), U1.15 ((PCINT1/OC1A)PB1)
RCA_VIDEO: D2.2 (A), U1.13 ((PCINT23/AIN1)PD7)
RX: J1.36, J4.5, U1.3 ((PCINT17/TXD)PD1)
SCK: J5.3, U1.19 ((PCINT5/SCK)PB5), U2.12 (SCK), U3.12 (SCK)
SS: U1.16 ((PCINT2/OC1B/~SS~)PB2), U2.11 (~CS), U3.11 (~CS)
TX: J1.35, R4.2, U1.2 ((PCINT16/RXD)PD0)
VCC: C1.2, C5.2, C6.2, J1.18, J5.2, JP2.1, R5.2, U1.7 (VCC), U1.20 (AVCC), U2.9 (VCC), U3.9 (VCC), U3.15 (A0)
XTAL1: C3.2, U1.9 ((PCINT6/XTAL1/TOSC1)PB6), Y1.1
XTAL2: C4.2, U1.10 ((PCINT7/XTAL2/TOSC2)PB7), Y1.2

Notes on the sheet:
RC6502 Video Adapter
Handles interacting with the PIA via the peripheral bus, substituting the original Apple 1 monitor circuitry. Includes General Video Connector as a means of interacting with other custom display modules implemented.

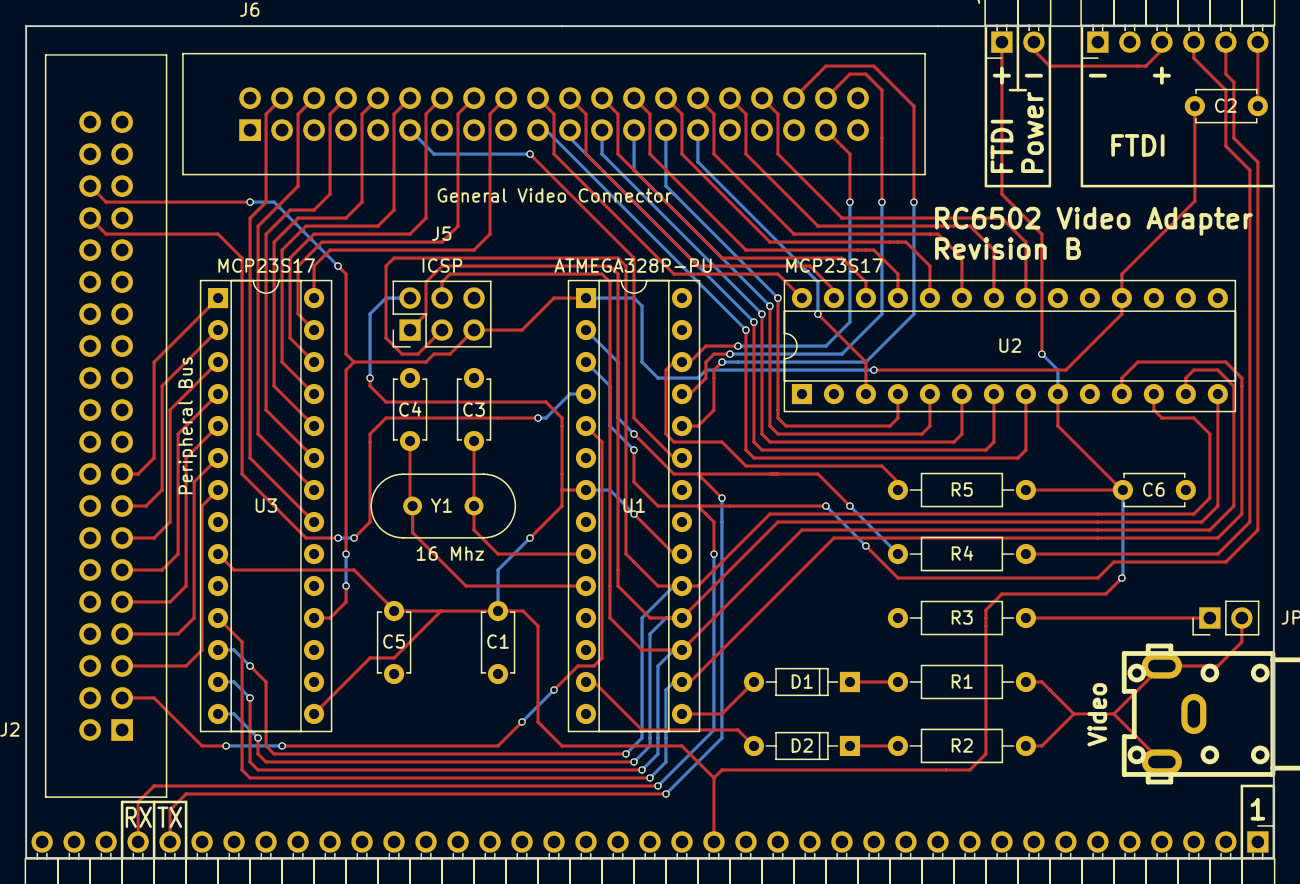
[picture p82: board RC6502 Video Adapter.kicad_pcb from above]

Board: 2 copper layers, 99.1 x 66.0 mm, 25 parts (0 on the bottom side), 55 nets.
