tebl/RC6502-Apple-1-Replica/Abandoned/RC6502 General Video Adapter/RC6502 General Video Adapter.kicad_pcb

## KiCad design Abandoned/RC6502 General Video Adapter/RC6502 General Video Adapter.kicad_pcb (2017-06-17)

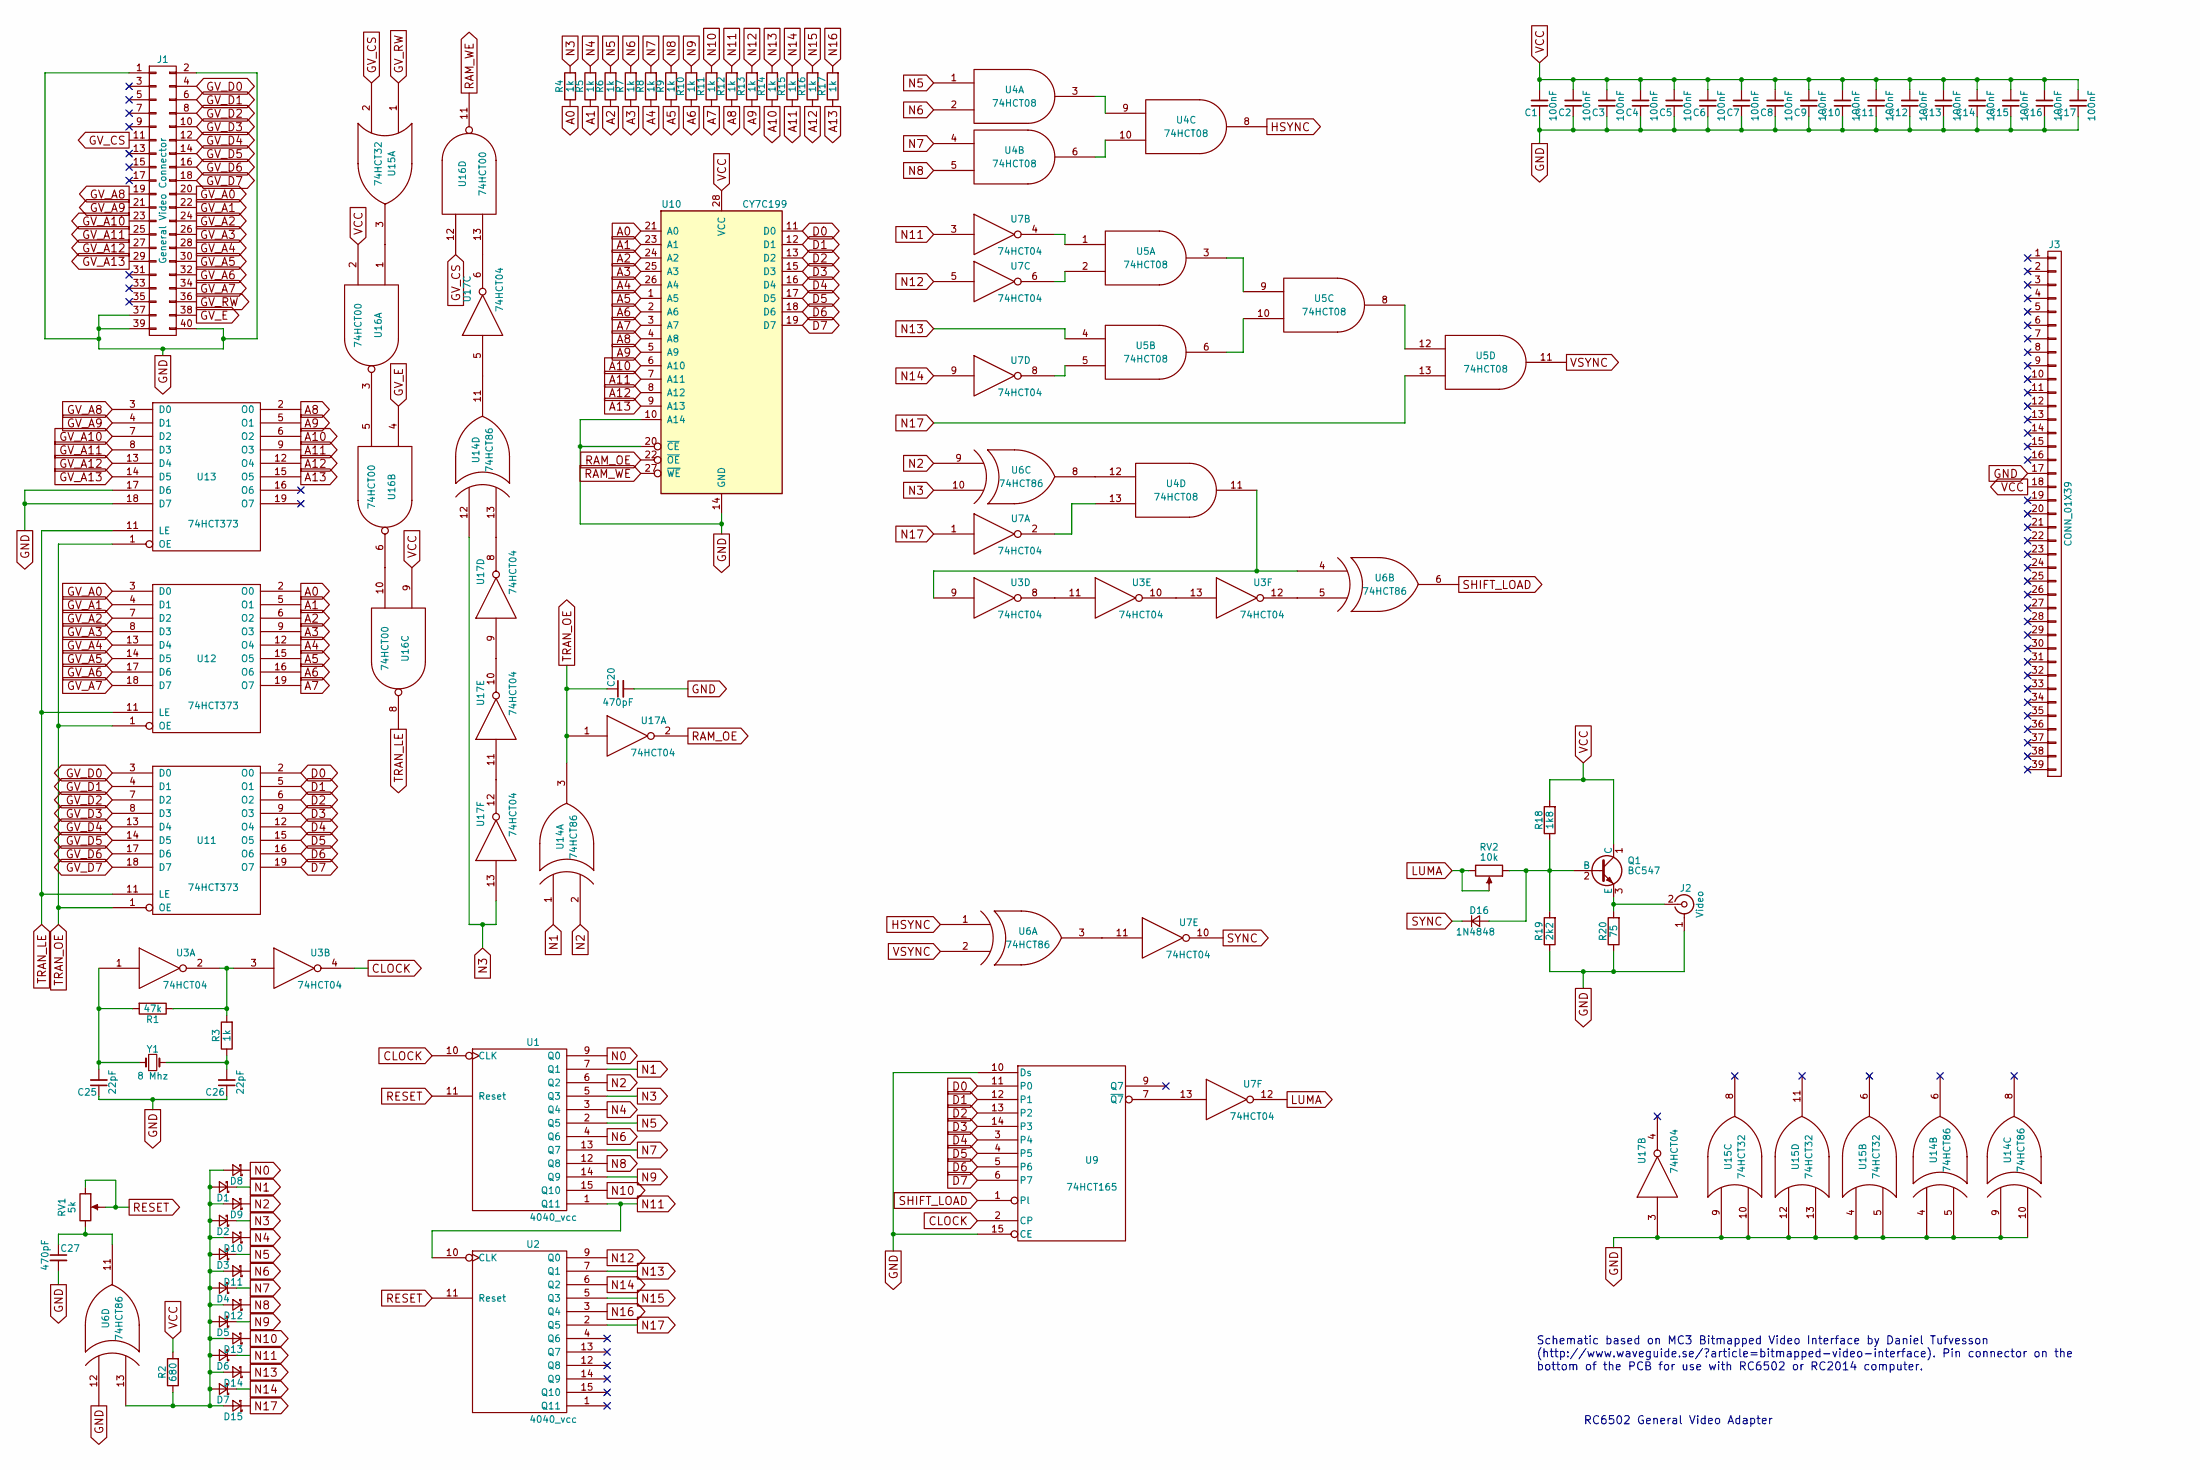
[picture p83: schematic RC6502 General Video Adapter.sch]

Parts:
C1, C2, C3, C4, C5, C6, C7, C8, C9, C10, C11, C12, C13, C14, C15, C16, C17: 100nF; C_Disc_D4.7mm_W2.5mm_P5.00mm
C20, C27: 470pF; C_Disc_D4.7mm_W2.5mm_P5.00mm
C25, C26: 22pF; C_Disc_D4.7mm_W2.5mm_P5.00mm
D1, D2, D3, D4, D5, D6, D7, D8, D9, D10, D11, D12, D13, D14, D15: BAT42; D_DO-35_SOD27_P7.62mm_Horizontal
D16: 1N4848; D_DO-35_SOD27_P7.62mm_Horizontal
J1: General Video Connector; IDC_Header_Straight_40pins
J2: Video; rca_yellow
J3: CONN_01X39; Pin_Header_Angled_1x39_Pitch2.54mm
Q1: BC547; TO-92_Molded_Narrow
R1: 47k; R_Axial_DIN0207_L6.3mm_D2.5mm_P10.16mm_Horizontal
R2: 680; R_Axial_DIN0207_L6.3mm_D2.5mm_P10.16mm_Horizontal
R3, R4, R5, R6, R7, R8, R9, R10, R11, R12, R13, R14, R15, R16, R17: 1k; R_Axial_DIN0207_L6.3mm_D2.5mm_P10.16mm_Horizontal
R18: 1k8; R_Axial_DIN0207_L6.3mm_D2.5mm_P10.16mm_Horizontal
R19: 2k2; R_Axial_DIN0207_L6.3mm_D2.5mm_P10.16mm_Horizontal
R20: 75; R_Axial_DIN0207_L6.3mm_D2.5mm_P10.16mm_Horizontal
RV1: 5k; Potentiometer_Trimmer_Bourns_3296W
RV2: 10k; Potentiometer_Trimmer_Bourns_3296W
U1, U2: 4040_vcc; DIP-16_W7.62mm_Socket
U3, U7, U17: 74HCT04; DIP-14_W7.62mm_Socket
U4, U5: 74HCT08; DIP-14_W7.62mm_Socket
U6, U14: 74HCT86; DIP-14_W7.62mm_Socket
U9: 74HCT165; DIP-16_W7.62mm_Socket
U10: CY7C199; DIP-28_W7.62mm_Socket
U11, U12, U13: 74HCT373; DIP-20_W7.62mm_Socket
U15: 74HCT32; DIP-14_W7.62mm_Socket
U16: 74HCT00; DIP-14_W7.62mm_Socket
Y1: 8 Mhz; Crystal_HC49-4H_Vertical

Connections:
A0: R4.1, U10.21 (A0), U12.2 (O0)
A1: R5.1, U10.23 (A1), U12.5 (O1)
A2: R6.1, U10.24 (A2), U12.6 (O2)
A3: R7.1, U10.25 (A3), U12.9 (O3)
A4: R8.1, U10.26 (A4), U12.12 (O4)
A5: R9.1, U10.1 (A5), U12.15 (O5)
A6: R10.1, U10.2 (A6), U12.16 (O6)
A7: R11.1, U10.3 (A7), U12.19 (O7)
A8: R12.1, U10.4 (A8), U13.2 (O0)
A9: R13.1, U10.5 (A9), U13.5 (O1)
A10: R14.1, U10.6 (A10), U13.6 (O2)
A11: R15.1, U10.7 (A11), U13.9 (O3)
A12: R16.1, U10.8 (A12), U13.12 (O4)
A13: R17.1, U10.9 (A13), U13.15 (O5)
CLOCK: U1.10 (CLK), U3.4, U9.2 (CP)
D0: U9.11 (P0), U10.11 (D0), U11.2 (O0)
D1: U9.12 (P1), U10.12 (D1), U11.5 (O1)
D2: U9.13 (P2), U10.13 (D2), U11.6 (O2)
D3: U9.14 (P3), U10.15 (D3), U11.9 (O3)
D4: U9.3 (P4), U10.16 (D4), U11.12 (O4)
D5: U9.4 (P5), U10.17 (D5), U11.15 (O5)
D6: U9.5 (P6), U10.18 (D6), U11.16 (O6)
D7: U9.6 (P7), U10.19 (D7), U11.19 (O7)
GND: C1.1, C2.1, C3.1, C4.1, C5.1, C6.1, C7.1, C8.1, C9.1, C10.1, C11.1, C12.1, C13.1, C14.1, C15.1, C16.1, C17.1, C20.2, C25.1, C26.1, C27.2, J1.1, J1.2, J1.37, J1.39, J1.40, J2.1 (Ext), J3.17, R19.1, R20.1, U1.8 (GND), U2.8 (GND), U3.7 (GND), U4.7 (GND), U5.7 (GND), U6.7 (GND), U6.12 (IN1), U7.7 (GND), U9.8 (GND), U9.10 (Ds), U9.15 (CE), U10.10 (A14), U10.14 (GND), U10.20 (~CE~), U11.10 (GND), U12.10 (GND), U13.10 (GND), U13.17 (D6), U13.18 (D7), U14.4 (IN1), U14.5 (IN2), U14.7 (GND), U14.9 (IN1), U14.10 (IN2), U15.4, U15.5, U15.7 (GND), U15.9, U15.10, U15.12, U15.13, U16.7 (GND), U17.3, U17.7 (GND)
GV_A0: J1.20, U12.3 (D0)
GV_A1: J1.22, U12.4 (D1)
GV_A2: J1.24, U12.7 (D2)
GV_A3: J1.26, U12.8 (D3)
GV_A4: J1.28, U12.13 (D4)
GV_A5: J1.30, U12.14 (D5)
GV_A6: J1.32, U12.17 (D6)
GV_A7: J1.34, U12.18 (D7)
GV_A8: J1.19, U13.3 (D0)
GV_A9: J1.21, U13.4 (D1)
GV_A10: J1.23, U13.7 (D2)
GV_A11: J1.25, U13.8 (D3)
GV_A12: J1.27, U13.13 (D4)
GV_A13: J1.29, U13.14 (D5)
GV_CS: J1.11, U15.2, U16.12
GV_D0: J1.4, U11.3 (D0)
GV_D1: J1.6, U11.4 (D1)
GV_D2: J1.8, U11.7 (D2)
GV_D3: J1.10, U11.8 (D3)
GV_D4: J1.12, U11.13 (D4)
GV_D5: J1.14, U11.14 (D5)
GV_D6: J1.16, U11.17 (D6)
GV_D7: J1.18, U11.18 (D7)
GV_E: J1.38, U16.4
GV_RW: J1.36, U15.1
HSYNC: U4.8, U6.1 (IN1)
LUMA: RV2.2, RV2.3, U7.12
N0: D8.1 (K), U1.9 (Q0)
N1: D1.1 (K), U1.7 (Q1), U14.1 (IN1)
N2: D9.1 (K), U1.6 (Q2), U6.9 (IN1), U14.2 (IN2)
N3: D2.1 (K), R4.2, U1.5 (Q3), U6.10 (IN2), U14.12 (IN1), U17.13
N4: D10.1 (K), R5.2, U1.3 (Q4)
N5: D3.1 (K), R6.2, U1.2 (Q5), U4.1
N6: D11.1 (K), R7.2, U1.4 (Q6), U4.2
N7: D4.1 (K), R8.2, U1.13 (Q7), U4.4
N8: D12.1 (K), R9.2, U1.12 (Q8), U4.5
N9: D5.1 (K), R10.2, U1.14 (Q9)
N10: D13.1 (K), R11.2, U1.15 (Q10)
N11: D6.1 (K), R12.2, U1.1 (Q11), U2.10 (CLK), U7.3
N12: R13.2, U2.9 (Q0), U7.5
N13: D14.1 (K), R14.2, U2.7 (Q1), U5.4
N14: D7.1 (K), R15.2, U2.6 (Q2), U7.9
N15: R16.2, U2.5 (Q3)
N16: R17.2, U2.3 (Q4)
N17: D15.1 (K), U2.2 (Q5), U5.13, U7.1
unnamed: C25.2, R1.2, U3.1, Y1.1
unnamed: C26.2, R3.1, Y1.2
unnamed: C27.1, RV1.3, U6.11 (OUT)
unnamed: D1.2 (A), D2.2 (A), D3.2 (A), D4.2 (A), D5.2 (A), D6.2 (A), D7.2 (A), D8.2 (A), D9.2 (A), D10.2 (A), D11.2 (A), D12.2 (A), D13.2 (A), D14.2 (A), D15.2 (A), R2.1, U6.13 (IN2)
unnamed: D16.2 (A), Q1.2 (B), R18.1, R19.2, RV2.1
unnamed: J2.2 (In), Q1.3 (E), R20.2
unnamed: R1.1, R3.2, U3.2, U3.3
unnamed: U3.9, U4.11, U6.4 (IN1)
unnamed: U3.10, U3.13
unnamed: U3.8, U3.11
unnamed: U3.12, U6.5 (IN2)
unnamed: U4.3, U4.9
unnamed: U4.6, U4.10
unnamed: U4.12, U6.8 (OUT)
unnamed: U4.13, U7.2
unnamed: U5.1, U7.4
unnamed: U5.2, U7.6
unnamed: U5.3, U5.9
unnamed: U5.5, U7.8
unnamed: U5.6, U5.10
unnamed: U5.8, U5.12
unnamed: U6.3 (OUT), U7.11
unnamed: U7.13, U9.7 (~Q7)
unnamed: U14.11 (OUT), U17.5
unnamed: U14.13 (IN2), U17.8
unnamed: U15.3, U16.1
unnamed: U16.3, U16.5
unnamed: U16.6, U16.10
unnamed: U16.13, U17.6
unnamed: U17.9, U17.10
unnamed: U17.11, U17.12
RAM_OE: U10.22 (~OE~), U17.2
RAM_WE: U10.27 (~WE~), U16.11
RESET: RV1.1, RV1.2, U1.11 (Reset), U2.11 (Reset)
SHIFT_LOAD: U6.6 (OUT), U9.1 (Pl)
SYNC: D16.1 (K), U7.10
TRAN_LE: U11.11 (LE), U12.11 (LE), U13.11 (LE), U16.8
TRAN_OE: C20.1, U11.1 (OE), U12.1 (OE), U13.1 (OE), U14.3 (OUT), U17.1
VCC: C1.2, C2.2, C3.2, C4.2, C5.2, C6.2, C7.2, C8.2, C9.2, C10.2, C11.2, C12.2, C13.2, C14.2, C15.2, C16.2, C17.2, J3.18, Q1.1 (C), R2.2, R18.2, U1.16 (VCC), U2.16 (VCC), U3.14 (VCC), U4.14 (VCC), U5.14 (VCC), U6.14 (VCC), U7.14 (VCC), U9.16 (VCC), U10.28 (VCC), U11.20 (VCC), U12.20 (VCC), U13.20 (VCC), U14.14 (VCC), U15.14 (VCC), U16.2, U16.9, U16.14 (VCC), U17.14 (VCC)
VSYNC: U5.11, U6.2 (IN2)

Notes on the sheet:
Schematic based on MC3 Bitmapped Video Interface by Daniel Tufvesson (http://www.waveguide.se/?article=bitmapped-video-interface). Pin connector on the bottom of the PCB for use with RC6502 or RC2014 computer.
RC6502 General Video Adapter

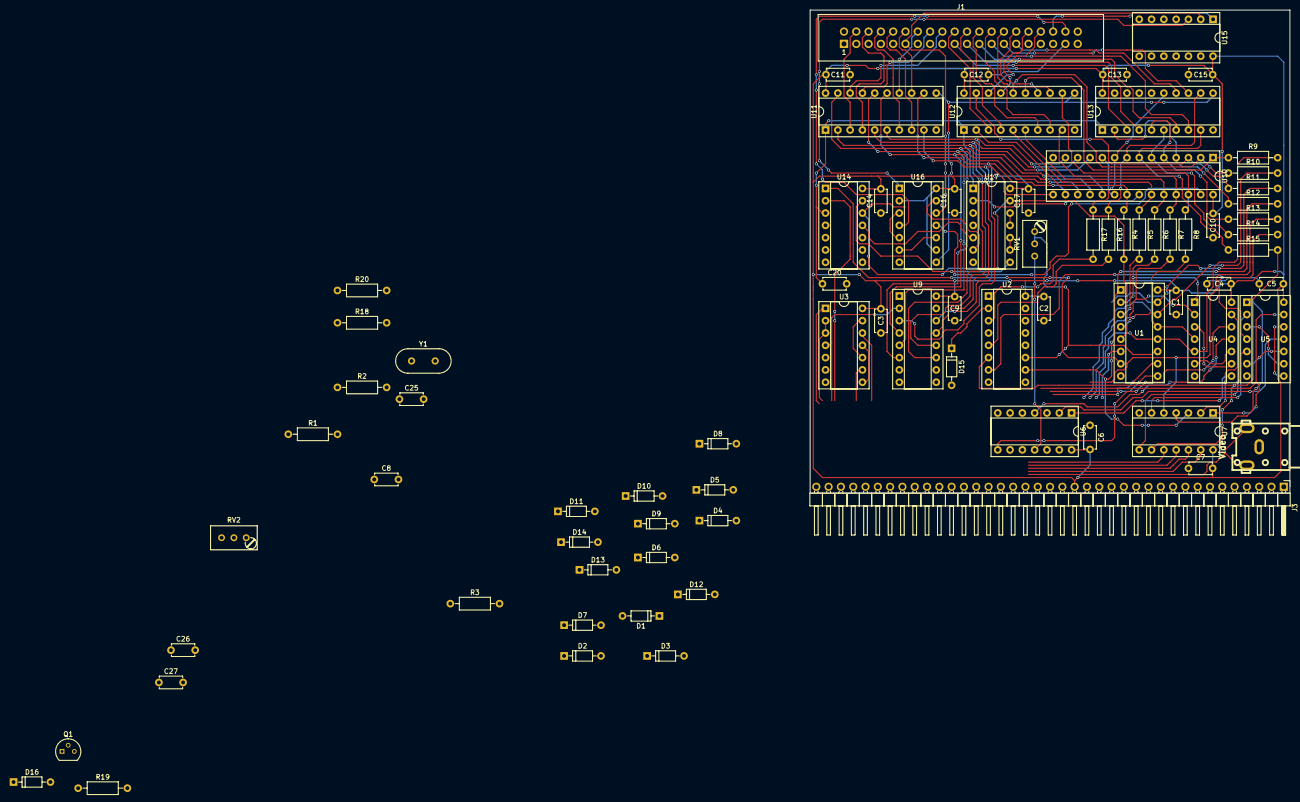
[picture p84: board RC6502 General Video Adapter.kicad_pcb from above]

Board: 2 copper layers, 99.1 x 99.7 mm, 80 parts (0 on the bottom side), 109 nets.
