tebl/RC6502-Apple-1-Replica/RC6502 Reset Circuit/Reset circuit.kicad_pcb

## KiCad design RC6502 Reset Circuit/Reset circuit.kicad_pcb (2017-06-19)

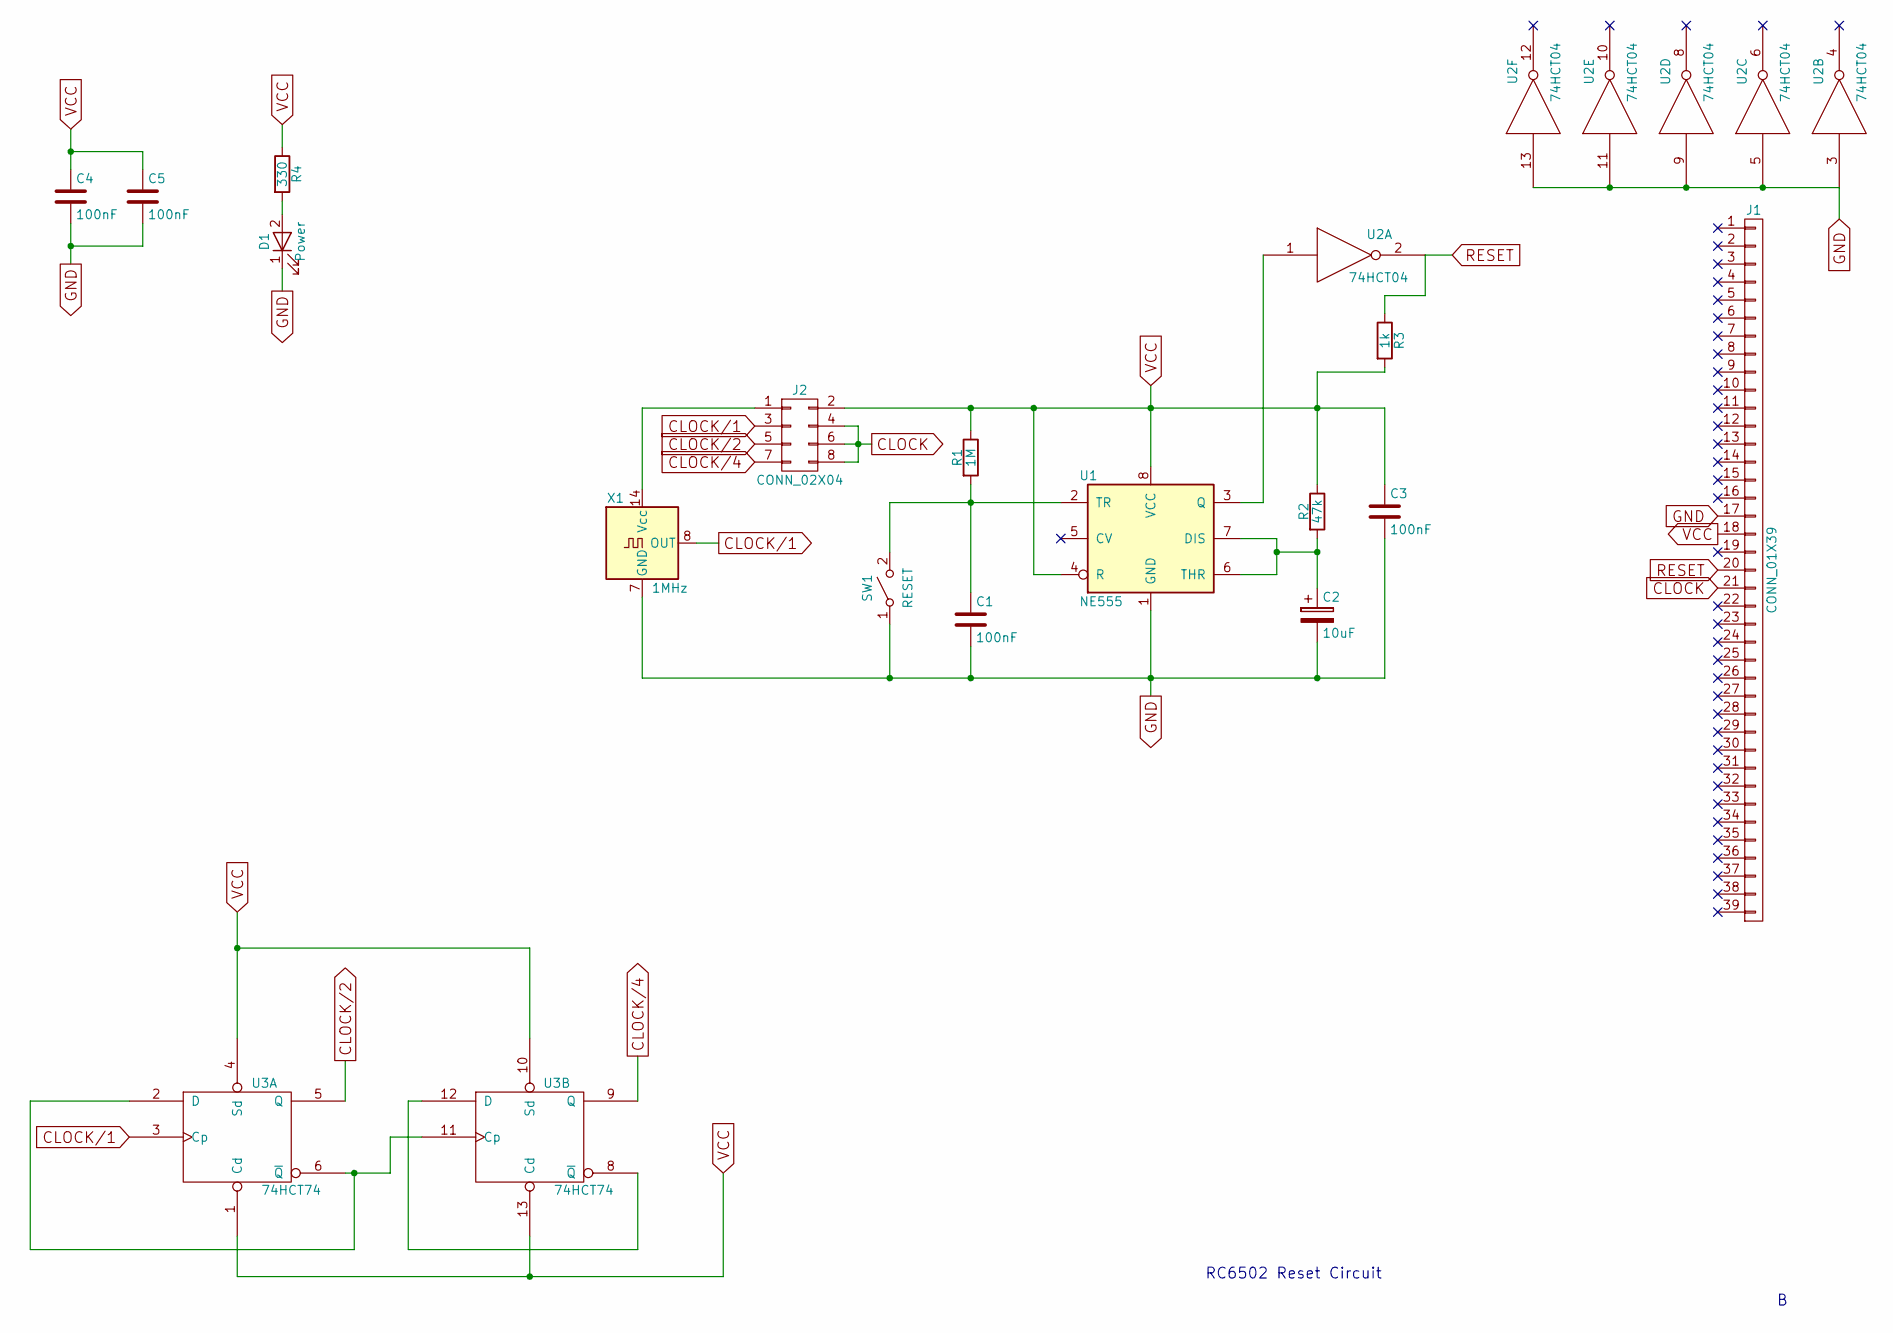
[picture p85: schematic Reset circuit.sch]

Parts:
C1, C3, C4, C5: 100nF; C_Disc_D4.7mm_W2.5mm_P5.00mm
C2: 10uF; CP_Radial_D4.0mm_P2.00mm
D1: Power; LED_D5.0mm
J1: CONN_01X39; Pin_Header_Angled_1x39_Pitch2.54mm
J2: CONN_02X04; Pin_Header_Straight_2x04_Pitch2.54mm
R1: 1M; R_Axial_DIN0207_L6.3mm_D2.5mm_P10.16mm_Horizontal
R2: 47k; R_Axial_DIN0207_L6.3mm_D2.5mm_P10.16mm_Horizontal
R3: 1k; R_Axial_DIN0207_L6.3mm_D2.5mm_P10.16mm_Horizontal
R4: 330; R_Axial_DIN0207_L6.3mm_D2.5mm_P10.16mm_Horizontal
SW1: RESET; SW_PUSH_6mm
U1: NE555; DIP-8_W7.62mm
U2: 74HCT04; DIP-14_W7.62mm
U3: 74HCT74; DIP-14_W7.62mm_Socket
X1: 1MHz; Oscillator_DIP-14

Connections:
CLOCK: J1.21, J2.4, J2.6, J2.8
CLOCK/1: J2.3, U3.3 (Cp), X1.8 (OUT)
CLOCK/2: J2.5, U3.5 (Q)
CLOCK/4: J2.7, U3.9 (Q)
GND: C1.2, C2.2, C3.2, C4.2, C5.2, D1.1 (K), J1.17, SW1.1 (A), U1.1 (GND), U2.3, U2.5, U2.7 (GND), U2.9, U2.11, U2.13, U3.7 (GND), X1.7 (GND)
unnamed: C1.1, R1.2, SW1.2 (B), U1.2 (TR)
unnamed: C2.1, R2.2, U1.6 (THR), U1.7 (DIS)
unnamed: D1.2 (A), R4.2
unnamed: J2.1, X1.14 (Vcc)
unnamed: U1.3 (Q), U2.1
unnamed: U3.2 (D), U3.6 (~Q), U3.11 (Cp)
unnamed: U3.8 (~Q), U3.12 (D)
RESET: J1.20, R3.1, U2.2
VCC: C3.1, C4.1, C5.1, J1.18, J2.2, R1.1, R2.1, R3.2, R4.1, U1.4 (R), U1.8 (VCC), U2.14 (VCC), U3.1 (Cd), U3.4 (Sd), U3.10 (Sd), U3.13 (Cd), U3.14 (VCC)

Notes on the sheet:
RC6502 Reset Circuit

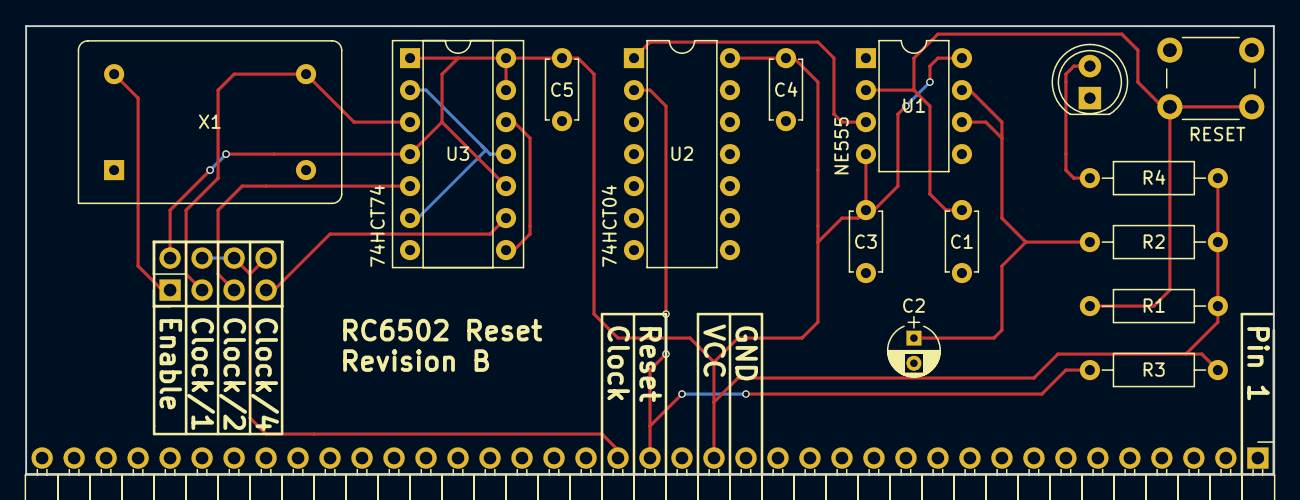
[picture p86: board Reset circuit.kicad_pcb from above]

Board: 2 copper layers, 99.1 x 35.6 mm, 17 parts (0 on the bottom side), 14 nets.
