tebl/RC6502-Apple-1-Replica/RC6502 CPU/RC6502 CPU.kicad_pcb

## KiCad design RC6502 CPU/RC6502 CPU.kicad_pcb (2017-06-15)

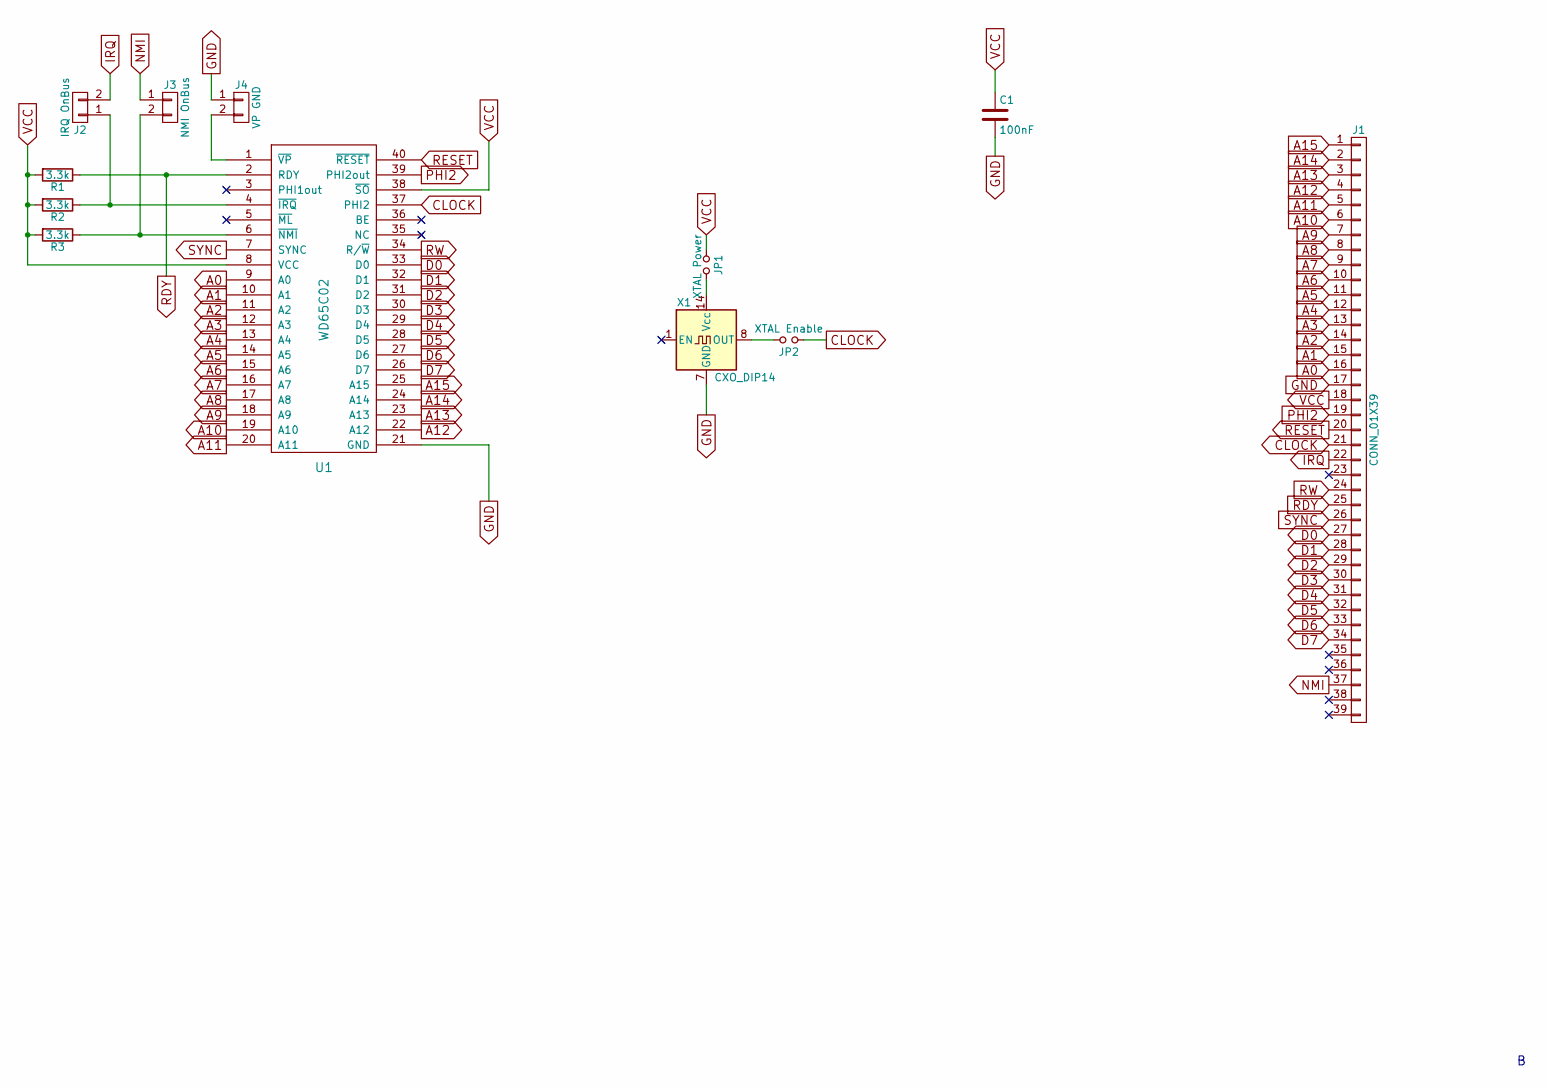
[picture p87: schematic RC6502 CPU.sch]

Parts:
C1: 100nF; C_Disc_D4.7mm_W2.5mm_P5.00mm
J1: CONN_01X39; Pin_Header_Angled_1x39_Pitch2.54mm
J2: IRQ OnBus; Pin_Header_Angled_1x02_Pitch2.54mm
J3: NMI OnBus; Pin_Header_Angled_1x02_Pitch2.54mm
J4: VP GND; Pin_Header_Angled_1x02_Pitch2.54mm
JP1: XTAL Power; Pin_Header_Angled_1x02_Pitch2.54mm
JP2: XTAL Enable; Pin_Header_Angled_1x02_Pitch2.54mm
R1, R2, R3: 3.3k; R_Axial_DIN0207_L6.3mm_D2.5mm_P10.16mm_Horizontal
U1: WD65C02; DIP-40_W15.24mm_Socket
X1: CXO_DIP14; Oscillator_DIP-14

Connections:
A0: J1.16, U1.9 (A0)
A1: J1.15, U1.10 (A1)
A2: J1.14, U1.11 (A2)
A3: J1.13, U1.12 (A3)
A4: J1.12, U1.13 (A4)
A5: J1.11, U1.14 (A5)
A6: J1.10, U1.15 (A6)
A7: J1.9, U1.16 (A7)
A8: J1.8, U1.17 (A8)
A9: J1.7, U1.18 (A9)
A10: J1.6, U1.19 (A10)
A11: J1.5, U1.20 (A11)
A12: J1.4, U1.22 (A12)
A13: J1.3, U1.23 (A13)
A14: J1.2, U1.24 (A14)
A15: J1.1, U1.25 (A15)
CLOCK: J1.21, JP2.1, U1.37 (PHI2)
D0: J1.27, U1.33 (D0)
D1: J1.28, U1.32 (D1)
D2: J1.29, U1.31 (D2)
D3: J1.30, U1.30 (D3)
D4: J1.31, U1.29 (D4)
D5: J1.32, U1.28 (D5)
D6: J1.33, U1.27 (D6)
D7: J1.34, U1.26 (D7)
GND: C1.2, J1.17, J4.1, U1.21 (GND), X1.7 (GND)
IRQ: J1.22, J2.2
NMI: J1.37, J3.1
unnamed: J2.1, R2.1, U1.4 (~IRQ)
unnamed: J3.2, R3.1, U1.6 (~NMI)
unnamed: J4.2, U1.1 (~VP)
unnamed: JP1.2, X1.14 (Vcc)
unnamed: JP2.2, X1.8 (OUT)
PHI2: J1.19, U1.39 (PHI2out)
RDY: J1.25, R1.1, U1.2 (RDY)
RESET: J1.20, U1.40 (~RESET)
RW: J1.24, U1.34 (R/~W)
SYNC: J1.26, U1.7 (SYNC)
VCC: C1.1, J1.18, JP1.1, R1.2, R2.2, R3.2, U1.8 (VCC), U1.38 (~SO)

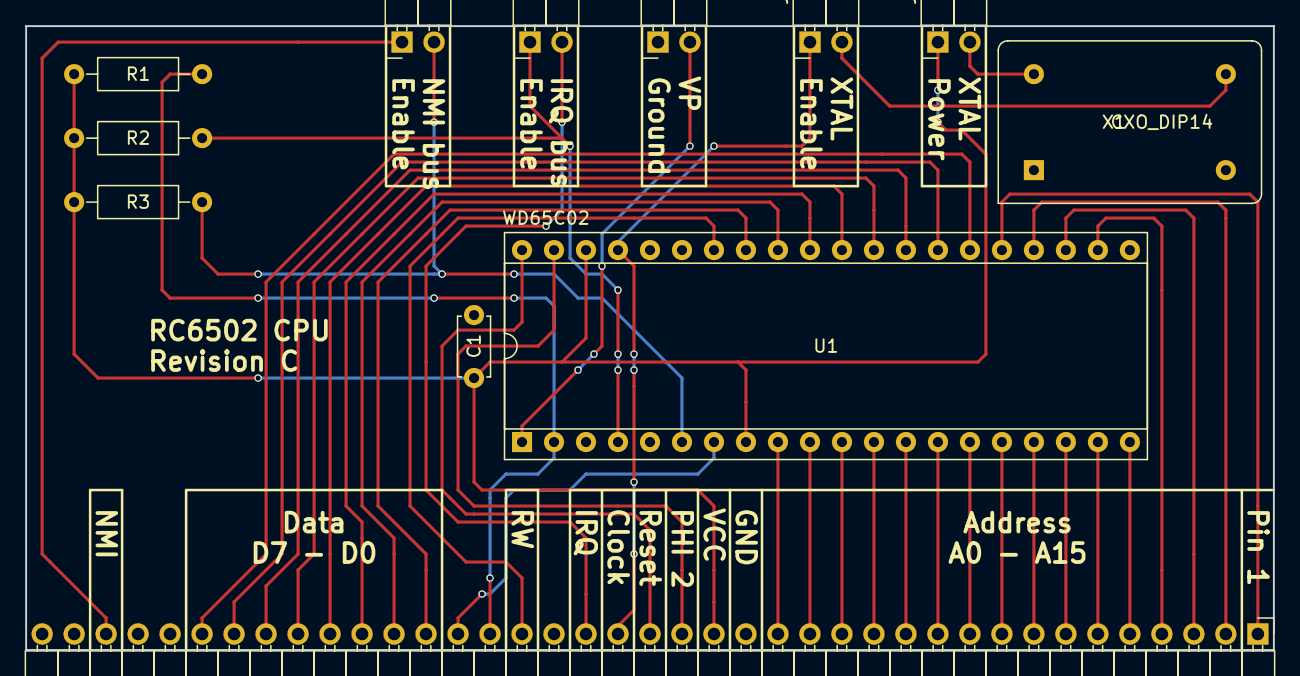
[picture p88: board RC6502 CPU.kicad_pcb from above]

Board: 2 copper layers, 99.1 x 49.5 mm, 12 parts (0 on the bottom side), 39 nets.
