tebl/RC6502-Apple-1-Replica/RC6502 Serial IO/RC6502 Serial IO.kicad_pcb

## KiCad design RC6502 Serial IO/RC6502 Serial IO.kicad_pcb (2017-06-10)

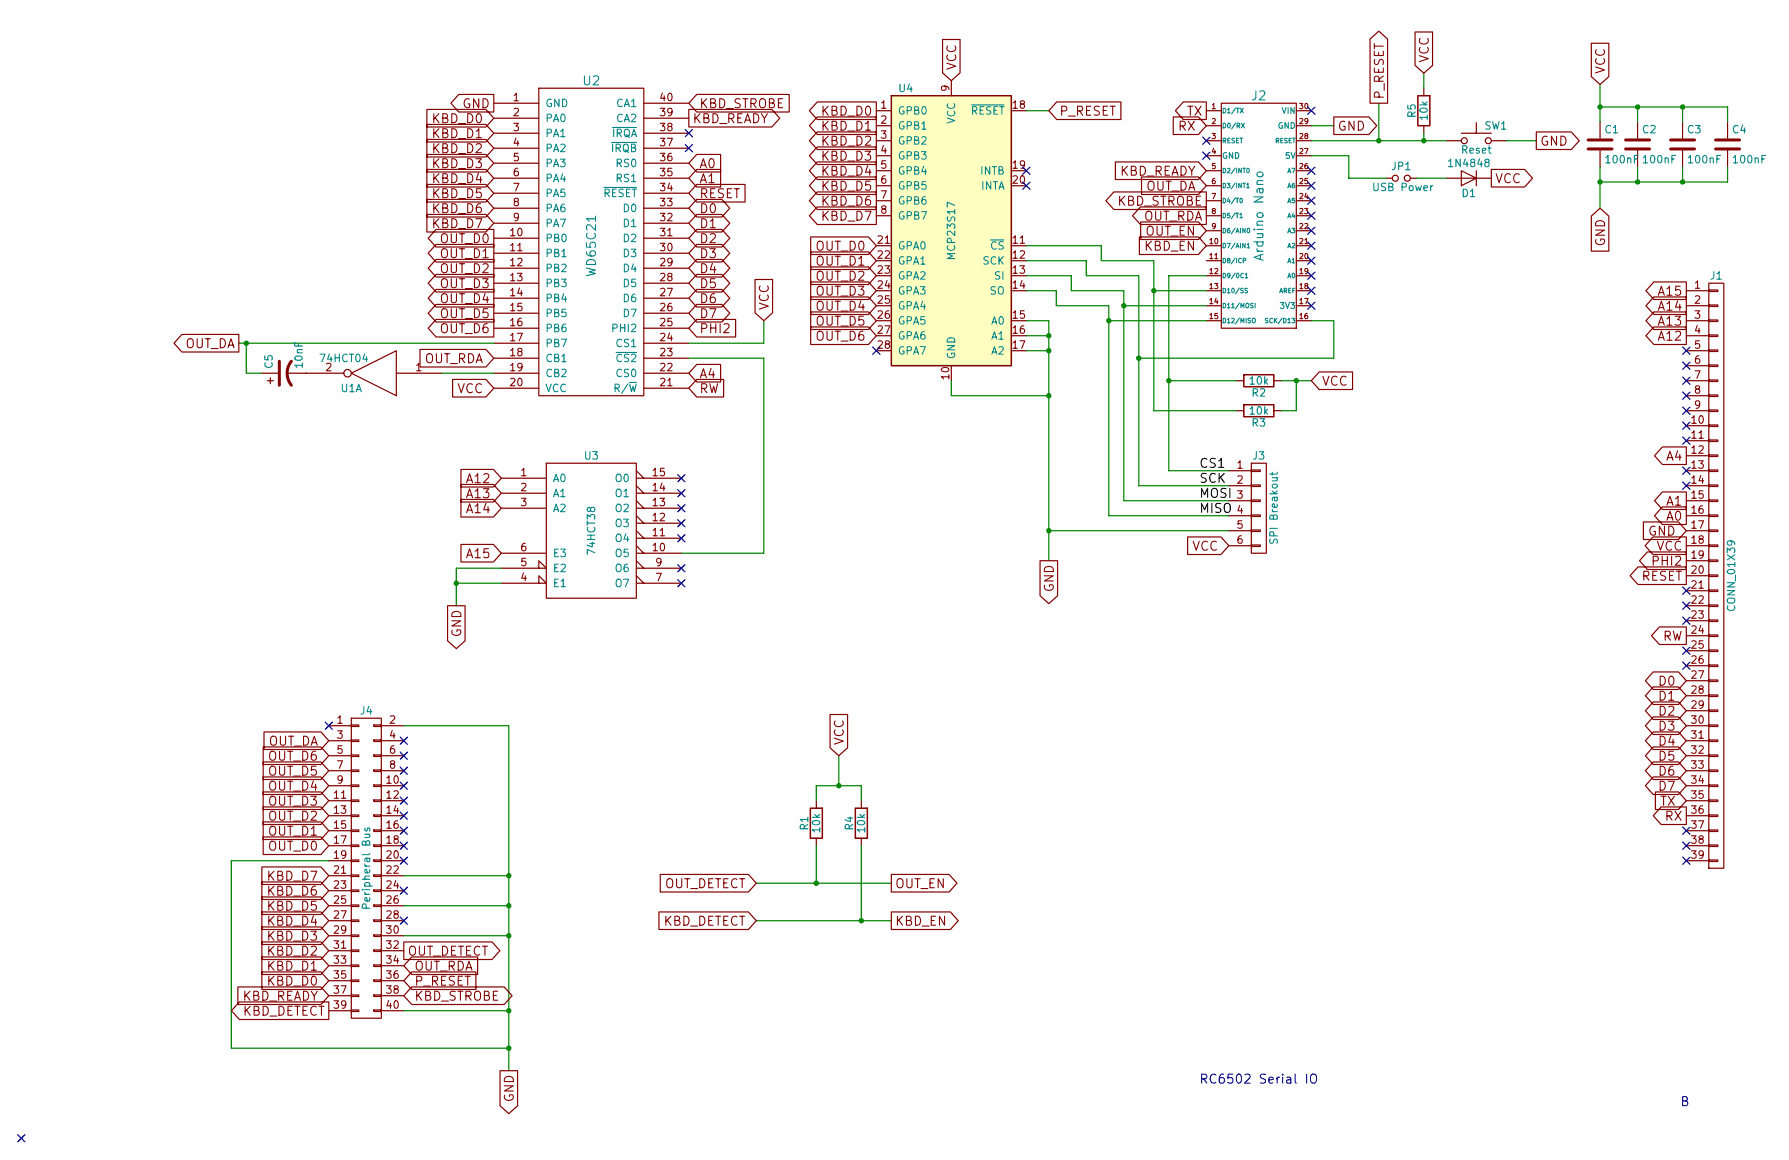
[picture p89: schematic RC6502 Serial IO.sch]

Parts:
C1, C2, C3, C4: 100nF; C_Disc_D4.7mm_W2.5mm_P5.00mm
C5: 10nF; C_Disc_D4.7mm_W2.5mm_P5.00mm
D1: 1N4848; D_DO-35_SOD27_P7.62mm_Horizontal
J1: CONN_01X39; Pin_Header_Angled_1x39_Pitch2.54mm
J2: Arduino Nano; Arduino_Nano
J3: SPI Breakout; Pin_Header_Angled_1x06_Pitch2.54mm
J4: Peripheral Bus; IDC_Header_Straight_40pins
JP1: USB Power; Pin_Header_Angled_1x02_Pitch2.54mm
R1, R2, R3, R4, R5: 10k; R_Axial_DIN0207_L6.3mm_D2.5mm_P10.16mm_Horizontal
SW1: Reset; SW_PUSH_6mm
U1: 74HCT04; DIP-14_W7.62mm_Socket
U2: WD65C21; DIP-40_W15.24mm_Socket
U3: 74HCT38; DIP-16_W7.62mm_Socket
U4: MCP23S17; DIP-28_W7.62mm_Socket

Connections:
/CS1: J2.12 (D9/0C1), J3.1, R2.2
/MISO: J2.15 (D12/MISO), J3.4, U4.14 (SO)
/MOSI: J2.14 (D11/MOSI), J3.3, U4.13 (SI)
/SCK: J2.16 (SCK/D13), J3.2, U4.12 (SCK)
A0: J1.16, U2.36 (RS0)
A1: J1.15, U2.35 (RS1)
A4: J1.12, U2.22 (CS0)
A12: J1.4, U3.1 (A0)
A13: J1.3, U3.2 (A1)
A14: J1.2, U3.3 (A2)
A15: J1.1, U3.6 (E3)
D0: J1.27, U2.33 (D0)
D1: J1.28, U2.32 (D1)
D2: J1.29, U2.31 (D2)
D3: J1.30, U2.30 (D3)
D4: J1.31, U2.29 (D4)
D5: J1.32, U2.28 (D5)
D6: J1.33, U2.27 (D6)
D7: J1.34, U2.26 (D7)
GND: C1.2, C2.2, C3.2, C4.2, J1.17, J2.29 (GND), J3.5, J4.2, J4.19, J4.22, J4.26, J4.30, J4.40, SW1.2, U1.7 (GND), U2.1 (GND), U3.4 (E1), U3.5 (E2), U3.8 (GND), U4.10 (GND), U4.15 (A0), U4.16 (A1), U4.17 (A2)
KBD_D0: J4.35, U2.2 (PA0), U4.1 (GPB0)
KBD_D1: J4.33, U2.3 (PA1), U4.2 (GPB1)
KBD_D2: J4.31, U2.4 (PA2), U4.3 (GPB2)
KBD_D3: J4.29, U2.5 (PA3), U4.4 (GPB3)
KBD_D4: J4.27, U2.6 (PA4), U4.5 (GPB4)
KBD_D5: J4.25, U2.7 (PA5), U4.6 (GPB5)
KBD_D6: J4.23, U2.8 (PA6), U4.7 (GPB6)
KBD_D7: J4.21, U2.9 (PA7), U4.8 (GPB7)
KBD_DETECT: J2.10 (D7/AIN1), J4.39, R4.1
KBD_READY: J2.5 (D2/INT0), J4.37, U2.39 (CA2)
KBD_STROBE: J2.7 (D4/T0), J4.38, U2.40 (CA1)
unnamed: C5.2, U1.2
unnamed: D1.2 (A), JP1.2
unnamed: J2.13 (D10/SS), R3.2, U4.11 (~CS)
unnamed: J2.27 (5V), JP1.1
unnamed: U1.1, U2.19 (CB2)
unnamed: U2.23 (~CS2), U3.10 (O5)
OUT_D0: J4.17, U2.10 (PB0), U4.21 (GPA0)
OUT_D1: J4.15, U2.11 (PB1), U4.22 (GPA1)
OUT_D2: J4.13, U2.12 (PB2), U4.23 (GPA2)
OUT_D3: J4.11, U2.13 (PB3), U4.24 (GPA3)
OUT_D4: J4.9, U2.14 (PB4), U4.25 (GPA4)
OUT_D5: J4.7, U2.15 (PB5), U4.26 (GPA5)
OUT_D6: J4.5, U2.16 (PB6), U4.27 (GPA6)
OUT_DA: C5.1, J2.6 (D3/INT1), J4.3, U2.17 (PB7)
OUT_DETECT: J2.9 (D6/AIN0), J4.32, R1.1
OUT_RDA: J2.8 (D5/T1), J4.34, U2.18 (CB1)
PHI2: J1.19, U2.25 (PHI2)
P_RESET: J2.28 (RESET), J4.36, R5.1, SW1.1, U4.18 (~RESET)
RESET: J1.20, U2.34 (~RESET)
RW: J1.24, U2.21 (R/~W)
RX: J1.36, J2.2 (D0/RX)
TX: J1.35, J2.1 (D1/TX)
VCC: C1.1, C2.1, C3.1, C4.1, D1.1 (K), J1.18, J3.6, R1.2, R2.1, R3.1, R4.2, R5.2, U1.14 (VCC), U2.20 (VCC), U2.24 (CS1), U3.16 (VCC), U4.9 (VCC)

Notes on the sheet:
RC6502 Serial IO

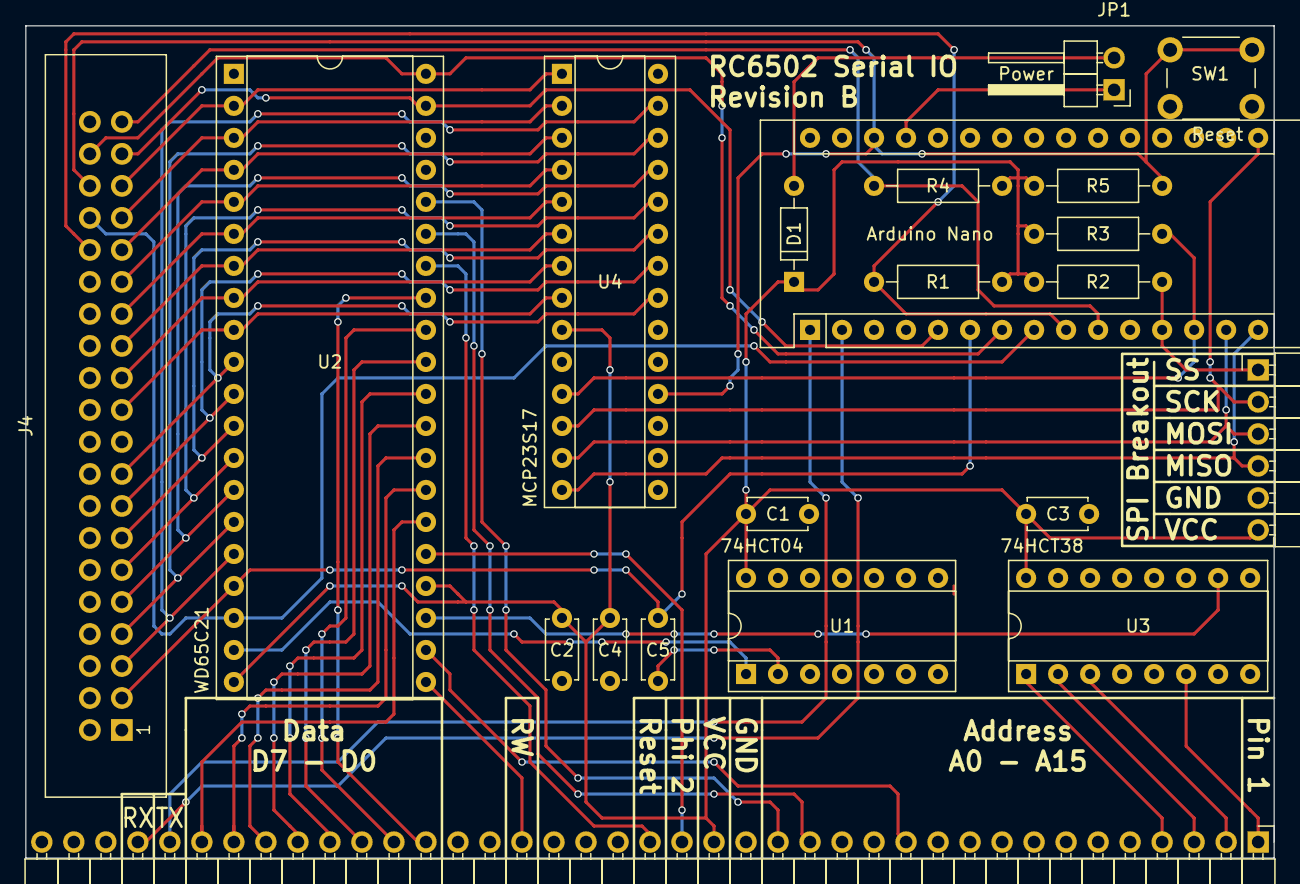
[picture p90: board RC6502 Serial IO.kicad_pcb from above]

Board: 2 copper layers, 99.1 x 66.0 mm, 21 parts (0 on the bottom side), 54 nets.
