tebl/RC6502-Apple-1-Replica/RC6502 ROM/RC6502 ROM.kicad_pcb

## KiCad design RC6502 ROM/RC6502 ROM.kicad_pcb (2017-06-09)

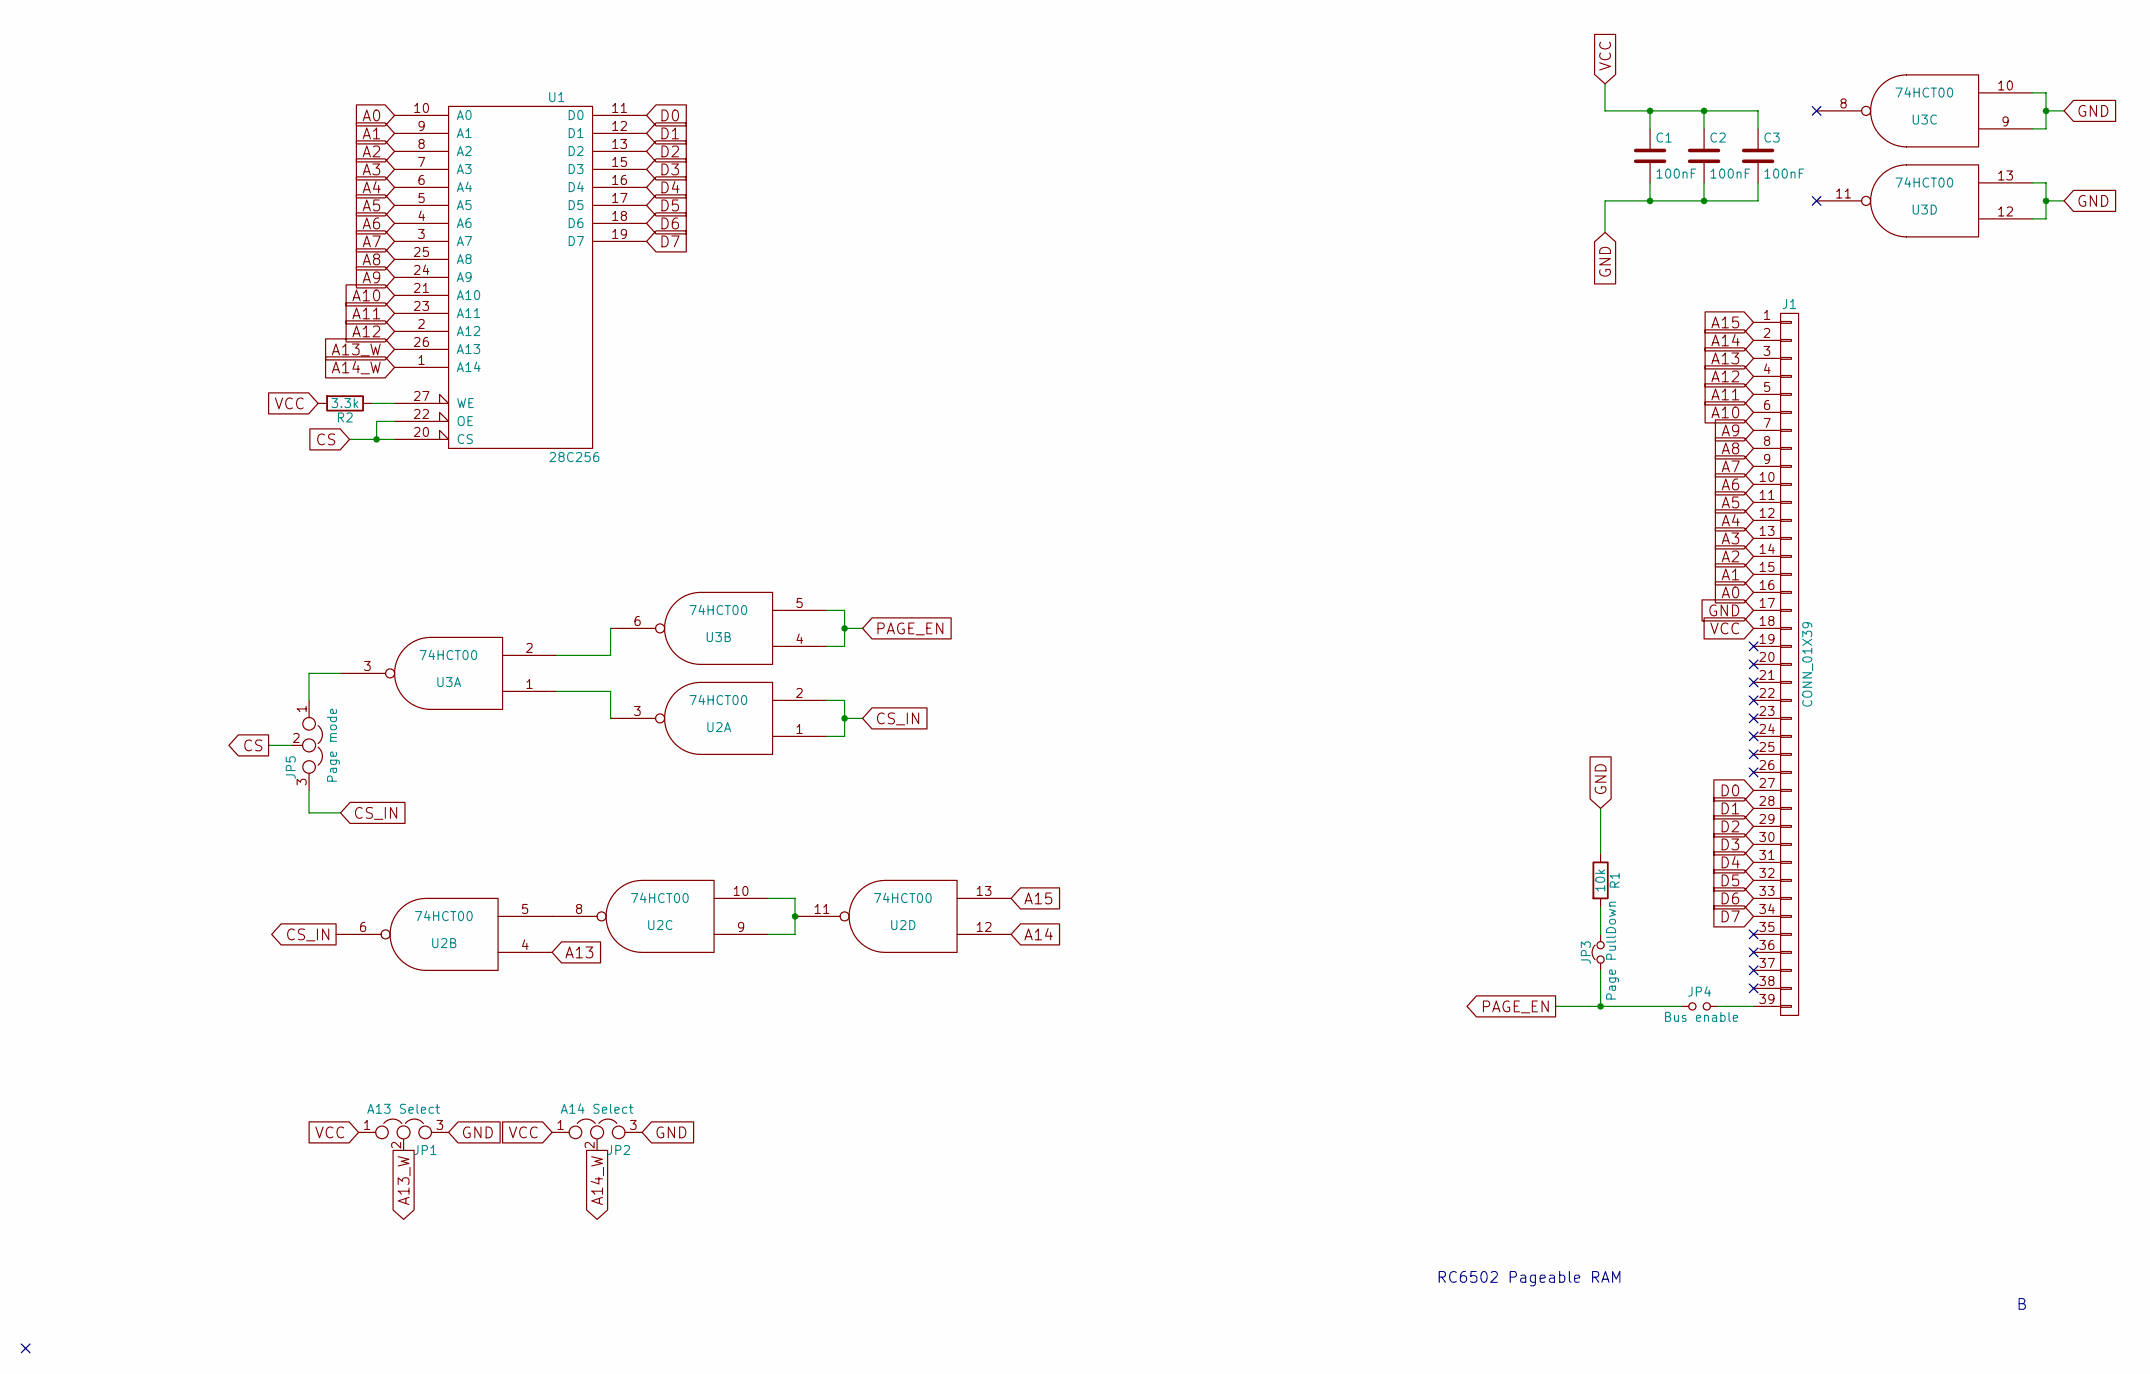
[picture p91: schematic RC6502 ROM.sch]

Parts:
C1, C2, C3: 100nF; C_Disc_D4.7mm_W2.5mm_P5.00mm
J1: CONN_01X39; Pin_Header_Angled_1x39_Pitch2.54mm
JP1: A13 Select; Pin_Header_Straight_1x03_Pitch2.54mm
JP2: A14 Select; Pin_Header_Straight_1x03_Pitch2.54mm
JP3: Page PullDown; Pin_Header_Angled_1x02_Pitch2.54mm
JP4: Bus enable; Pin_Header_Angled_1x02_Pitch2.54mm
JP5: Page mode; Pin_Header_Straight_1x03_Pitch2.54mm
R1: 10k; R_Axial_DIN0207_L6.3mm_D2.5mm_P10.16mm_Horizontal
R2: 3.3k; R_Axial_DIN0207_L6.3mm_D2.5mm_P10.16mm_Horizontal
U1: 28C256; DIP-28_W15.24mm_Socket_LongPads
U2, U3: 74HCT00; DIP-14_W7.62mm_Socket

Connections:
A0: J1.16, U1.10 (A0)
A1: J1.15, U1.9 (A1)
A2: J1.14, U1.8 (A2)
A3: J1.13, U1.7 (A3)
A4: J1.12, U1.6 (A4)
A5: J1.11, U1.5 (A5)
A6: J1.10, U1.4 (A6)
A7: J1.9, U1.3 (A7)
A8: J1.8, U1.25 (A8)
A9: J1.7, U1.24 (A9)
A10: J1.6, U1.21 (A10)
A11: J1.5, U1.23 (A11)
A12: J1.4, U1.2 (A12)
A13: J1.3, U2.4
A13_W: JP1.2, U1.26 (A13)
A14: J1.2, U2.12
A14_W: JP2.2, U1.1 (A14)
A15: J1.1, U2.13
CS: JP5.2, U1.20 (CS), U1.22 (OE)
CS_IN: JP5.3, U2.1, U2.2, U2.6
D0: J1.27, U1.11 (D0)
D1: J1.28, U1.12 (D1)
D2: J1.29, U1.13 (D2)
D3: J1.30, U1.15 (D3)
D4: J1.31, U1.16 (D4)
D5: J1.32, U1.17 (D5)
D6: J1.33, U1.18 (D6)
D7: J1.34, U1.19 (D7)
GND: C1.2, C2.2, C3.2, J1.17, JP1.3, JP2.3, R1.1, U1.14 (GND), U2.7 (GND), U3.7 (GND), U3.9, U3.10, U3.12, U3.13
unnamed: J1.39, JP4.2
unnamed: JP3.2, R1.2
unnamed: JP5.1, U3.3
unnamed: R2.1, U1.27 (WE)
unnamed: U2.3, U3.1
unnamed: U2.5, U2.8
unnamed: U2.9, U2.10, U2.11
unnamed: U3.2, U3.6
PAGE_EN: JP3.1, JP4.1, U3.4, U3.5
VCC: C1.1, C2.1, C3.1, J1.18, JP1.1, JP2.1, R2.2, U1.28 (VCC), U2.14 (VCC), U3.14 (VCC)

Notes on the sheet:
RC6502 Pageable RAM

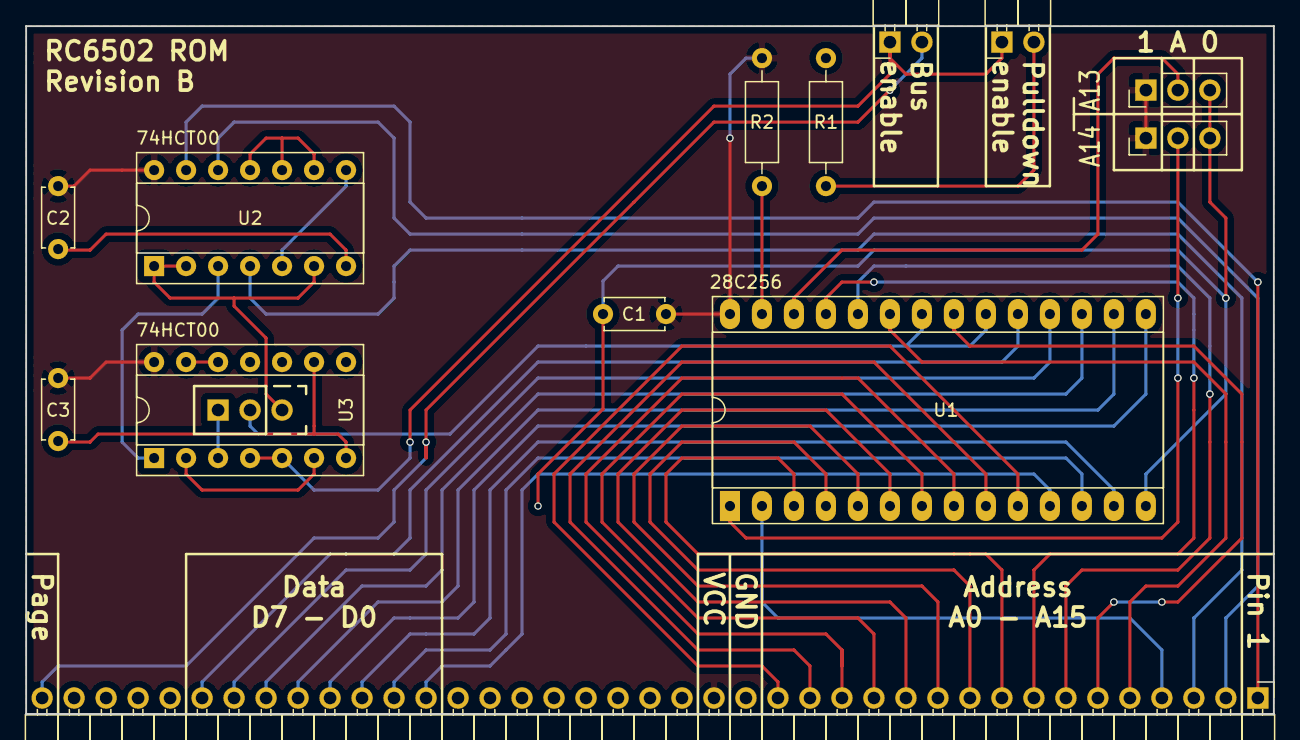
[picture p92: board RC6502 ROM.kicad_pcb from above]

Board: 2 copper layers, 99.1 x 54.6 mm, 14 parts (1 on the bottom side), 39 nets.
