tebl/RC6502-Apple-1-Replica/RC6502 Terminal/RC6502 Terminal.kicad_pcb

## KiCad design RC6502 Terminal/RC6502 Terminal.kicad_pcb (2020-01-22)

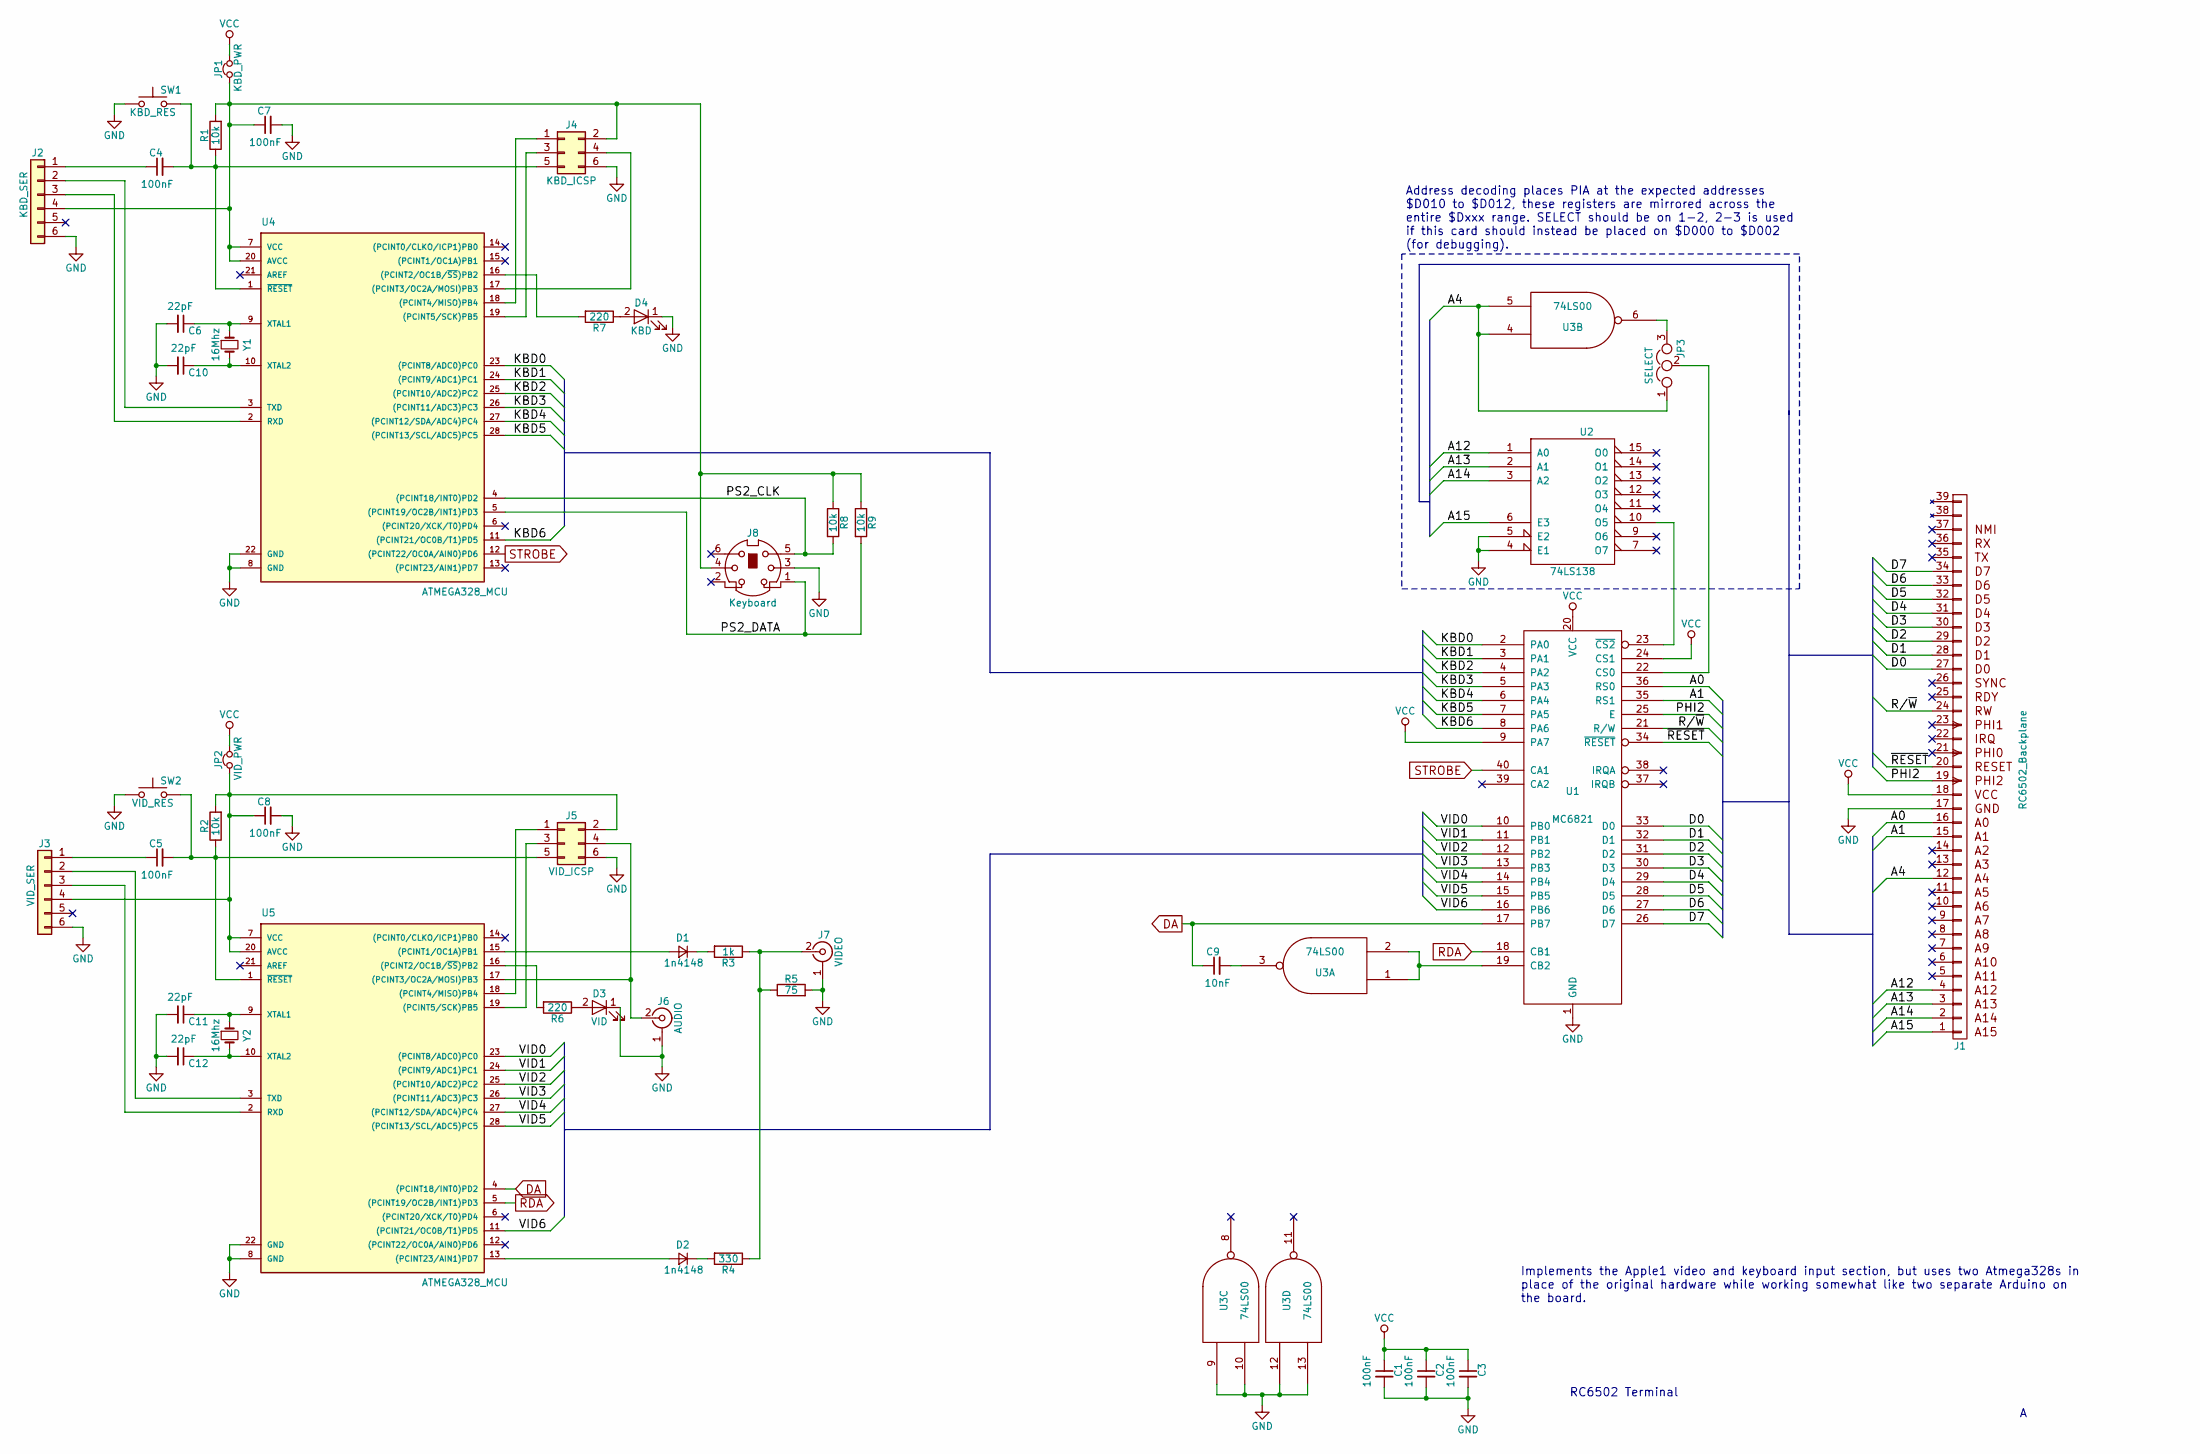
[picture p93: schematic RC6502 Terminal-2022-01-25-22-15-36.sch]

Parts:
C1, C2, C3, C4, C5, C7, C8: 100nF; C_Disc_D4.7mm_W2.5mm_P5.00mm
C6, C10, C11, C12: 22pF; C_Disc_D4.7mm_W2.5mm_P5.00mm
C9: 10nF; C_Disc_D4.7mm_W2.5mm_P5.00mm
D1, D2: 1n4148; D_DO-35_SOD27_P7.62mm_Horizontal
D3: VID; LED_D5.0mm
D4: KBD; LED_D5.0mm
J1: RC6502_Backplane; Pin_Header_Angled_1x39_Pitch2.54mm
J2: KBD_SER; Pin_Header_Straight_1x06_Pitch2.54mm
J3: VID_SER; Pin_Header_Straight_1x06_Pitch2.54mm
J4: KBD_ICSP; Pin_Header_Straight_2x03_Pitch2.54mm
J5: VID_ICSP; Pin_Header_Straight_2x03_Pitch2.54mm
J6: AUDIO; rca_yellow
J7: VIDEO; rca_yellow
J8: Keyboard; MINI-DIN-6-FULL-SHIELD
JP1: KBD_PWR; Pin_Header_Straight_1x02_Pitch2.54mm
JP2: VID_PWR; Pin_Header_Straight_1x02_Pitch2.54mm
JP3: SELECT; Pin_Header_Straight_1x03_Pitch2.54mm
R1, R2, R8, R9: 10k; R_Axial_DIN0207_L6.3mm_D2.5mm_P10.16mm_Horizontal
R3: 1k; R_Axial_DIN0207_L6.3mm_D2.5mm_P10.16mm_Horizontal
R4: 330; R_Axial_DIN0207_L6.3mm_D2.5mm_P10.16mm_Horizontal
R5: 75; R_Axial_DIN0207_L6.3mm_D2.5mm_P10.16mm_Horizontal
R6, R7: 220; R_Axial_DIN0207_L6.3mm_D2.5mm_P10.16mm_Horizontal
SW1: KBD_RES; SW_PUSH_6mm
SW2: VID_RES; SW_PUSH_6mm
U1: MC6821; DIP-40_W15.24mm_Socket_LongPads
U2: 74LS138; DIP-16_W7.62mm_Socket_LongPads
U3: 74LS00; DIP-14_W7.62mm_Socket_LongPads
U4, U5: ATMEGA328_MCU; DIP-28_W7.62mm_Socket
Y1, Y2: 16Mhz; Crystal_HC49-4H_Vertical

Connections:
/A0: J1.16 (A0), U1.36 (RS0)
/A1: J1.15 (A1), U1.35 (RS1)
/A4: J1.12 (A4), JP3.1, U3.4, U3.5
/A12: J1.4 (A12), U2.1 (A0)
/A13: J1.3 (A13), U2.2 (A1)
/A14: J1.2 (A14), U2.3 (A2)
/A15: J1.1 (A15), U2.6 (E3)
/D0: J1.27 (D0), U1.33 (D0)
/D1: J1.28 (D1), U1.32 (D1)
/D2: J1.29 (D2), U1.31 (D2)
/D3: J1.30 (D3), U1.30 (D3)
/D4: J1.31 (D4), U1.29 (D4)
/D5: J1.32 (D5), U1.28 (D5)
/D6: J1.33 (D6), U1.27 (D6)
/D7: J1.34 (D7), U1.26 (D7)
/KBD0: U1.2 (PA0), U4.23 ((PCINT8/ADC0)PC0)
/KBD1: U1.3 (PA1), U4.24 ((PCINT9/ADC1)PC1)
/KBD2: U1.4 (PA2), U4.25 ((PCINT10/ADC2)PC2)
/KBD3: U1.5 (PA3), U4.26 ((PCINT11/ADC3)PC3)
/KBD4: U1.6 (PA4), U4.27 ((PCINT12/SDA/ADC4)PC4)
/KBD5: U1.7 (PA5), U4.28 ((PCINT13/SCL/ADC5)PC5)
/KBD6: U1.8 (PA6), U4.11 ((PCINT21/OC0B/T1)PD5)
/PHI2: J1.19 (PHI2), U1.25 (E)
/PS2_CLK: J8.5, R8.2, U4.4 ((PCINT18/INT0)PD2)
/PS2_DATA: J8.1, R9.2, U4.5 ((PCINT19/OC2B/INT1)PD3)
/R/~W: J1.24 (RW), U1.21 (R/W)
/VID0: U1.10 (PB0), U5.23 ((PCINT8/ADC0)PC0)
/VID1: U1.11 (PB1), U5.24 ((PCINT9/ADC1)PC1)
/VID2: U1.12 (PB2), U5.25 ((PCINT10/ADC2)PC2)
/VID3: U1.13 (PB3), U5.26 ((PCINT11/ADC3)PC3)
/VID4: U1.14 (PB4), U5.27 ((PCINT12/SDA/ADC4)PC4)
/VID5: U1.15 (PB5), U5.28 ((PCINT13/SCL/ADC5)PC5)
/VID6: U1.16 (PB6), U5.11 ((PCINT21/OC0B/T1)PD5)
/~RESET: J1.20 (RESET), U1.34 (~RESET)
DA: C9.1, U1.17 (PB7), U5.4 ((PCINT18/INT0)PD2)
GND: C1.2, C2.2, C3.2, C6.2, C7.2, C8.2, C10.2, C11.2, C12.2, D3.1 (K), D4.1 (K), J1.17, J2.6, J3.6, J4.6, J5.6, J6.1 (Ext), J7.1 (Ext), J8.3, R5.2, SW1.1, SW2.1, U1.1 (GND), U2.4 (E1), U2.5 (E2), U2.8 (GND), U3.7 (GND), U3.9, U3.10, U3.12, U3.13, U4.8 (GND), U4.22 (GND), U5.8 (GND), U5.22 (GND)
unnamed: C4.1, J2.1
unnamed: C4.2, J4.5, R1.1, SW1.2, U4.1 (~RESET)
unnamed: C5.1, J3.1
unnamed: C5.2, J5.5, R2.1, SW2.2, U5.1 (~RESET)
unnamed: C6.1, U4.9 (XTAL1), Y1.1
unnamed: C7.1, J2.4, J4.2, J8.4, JP1.1, R1.2, R8.1, R9.1, U4.7 (VCC), U4.20 (AVCC)
unnamed: C8.1, J3.4, J5.2, JP2.1, R2.2, U5.7 (VCC), U5.20 (AVCC)
unnamed: C9.2, U3.3
unnamed: C10.1, U4.10 (XTAL2), Y1.2
unnamed: C11.1, U5.9 (XTAL1), Y2.1
unnamed: C12.1, U5.10 (XTAL2), Y2.2
unnamed: D1.1 (K), R3.2
unnamed: D1.2 (A), U5.15 ((PCINT1/OC1A)PB1)
unnamed: D2.1 (K), R4.2
unnamed: D2.2 (A), U5.13 ((PCINT23/AIN1)PD7)
unnamed: D3.2 (A), R6.1
unnamed: D4.2 (A), R7.1
unnamed: J2.2, U4.3 (TXD)
unnamed: J2.3, U4.2 (RXD)
unnamed: J3.2, U5.3 (TXD)
unnamed: J3.3, U5.2 (RXD)
unnamed: J4.1, U4.18 ((PCINT4/MISO)PB4)
unnamed: J4.3, U4.19 ((PCINT5/SCK)PB5)
unnamed: J4.4, U4.17 ((PCINT3/OC2A/MOSI)PB3)
unnamed: J5.1, U5.18 ((PCINT4/MISO)PB4)
unnamed: J5.3, U5.19 ((PCINT5/SCK)PB5)
unnamed: J5.4, J6.2 (In), U5.17 ((PCINT3/OC2A/MOSI)PB3)
unnamed: J7.2 (In), R3.1, R4.1, R5.1
unnamed: JP3.2, U1.22 (CS0)
unnamed: JP3.3, U3.6
unnamed: R6.2, U5.16 ((PCINT2/OC1B/~SS~)PB2)
unnamed: R7.2, U4.16 ((PCINT2/OC1B/~SS~)PB2)
unnamed: U1.19 (CB2), U3.1, U3.2
unnamed: U1.23 (~CS2), U2.10 (O5)
RDA: U1.18 (CB1), U5.5 ((PCINT19/OC2B/INT1)PD3)
STROBE: U1.40 (CA1), U4.12 ((PCINT22/OC0A/AIN0)PD6)
VCC: C1.1, C2.1, C3.1, J1.18, JP1.2, JP2.2, U1.9 (PA7), U1.20 (VCC), U1.24 (CS1), U2.16 (VCC), U3.14 (VCC)

Notes on the sheet:
RC6502 Terminal
Implements the Apple1 video and keyboard input section, but uses two Atmega328s in place of the original hardware while working somewhat like two separate Arduino on the board.
Address decoding places PIA at the expected addresses $D010 to $D012, these registers are mirrored across the entire $Dxxx range. SELECT should be on 1-2, 2-3 is used if this card should instead be placed on $D000 to $D002 (for debugging).

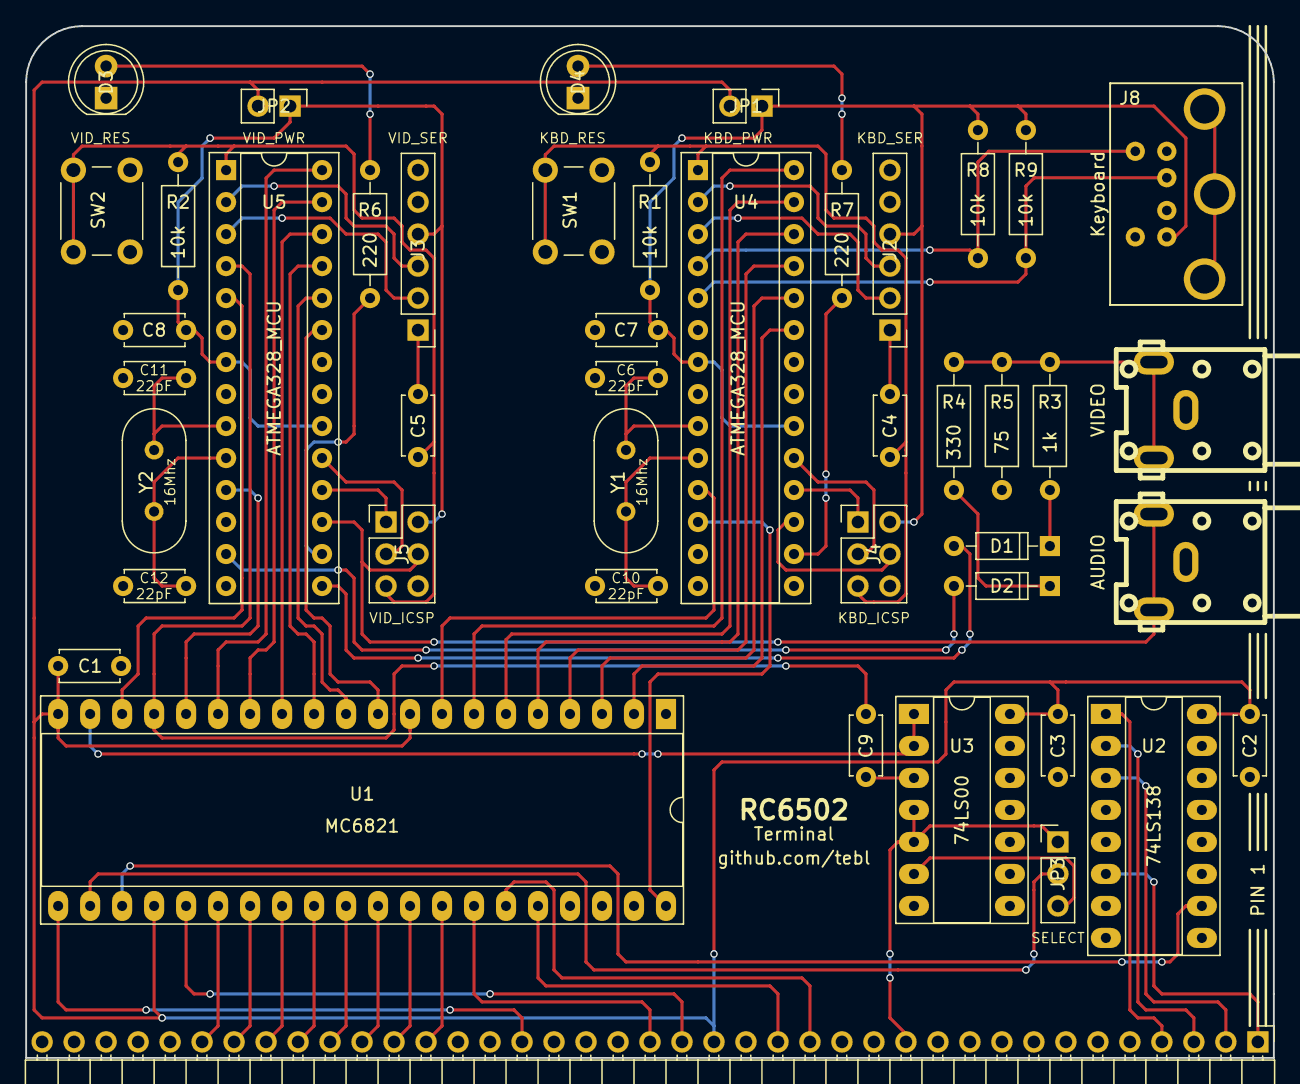
[picture p94: board RC6502 Terminal.kicad_pcb from above]

Board: 2 copper layers, 99.1 x 81.9 mm, 45 parts (0 on the bottom side), 73 nets.
